testezt/EZTFinder5/images/hardware_overview.png

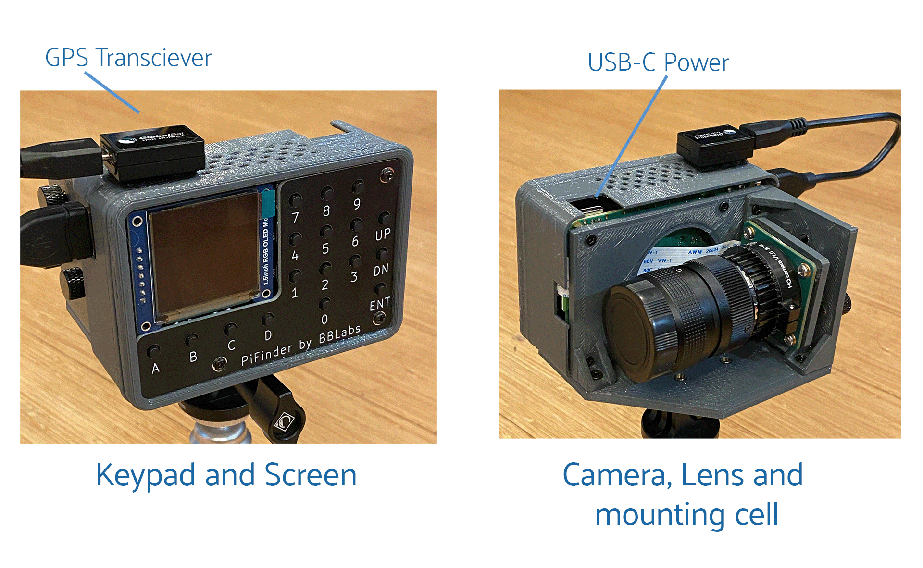
images/hardware_overview.png
