testezt/EZTFinder5/case/v3/flat/flat_plug.stl

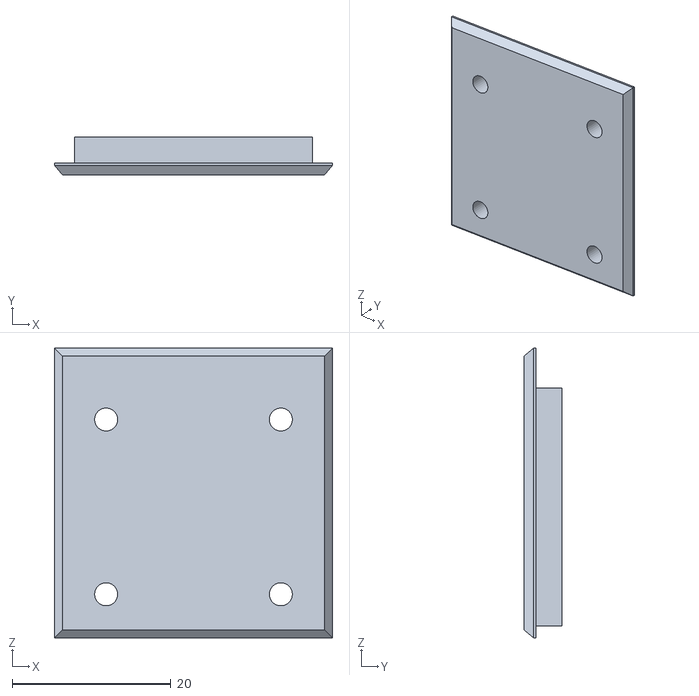
[picture p19: CAD file, 2026-02-22]
case/v3/flat/flat_plug.stl
35.0 x 4.75 x 36.5
