testezt/EZTFinder5/case/v3/left_right/camera_mount.stl

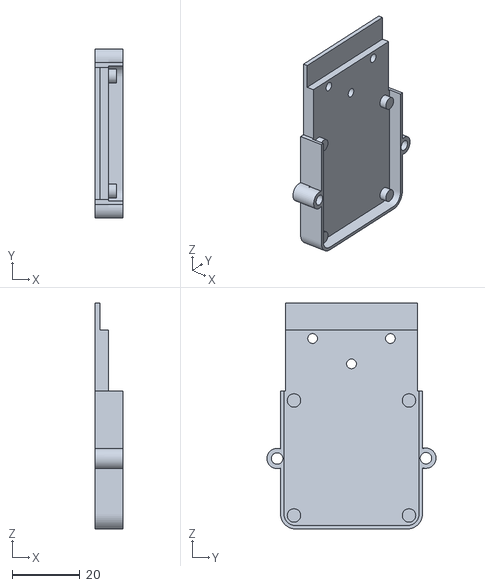
[picture p20: CAD file, 2026-02-22]
case/v3/left_right/camera_mount.stl
8.40 x 50.0 x 66.8
