testezt/EZTFinder5/case/v3/straight/st_tray.stl

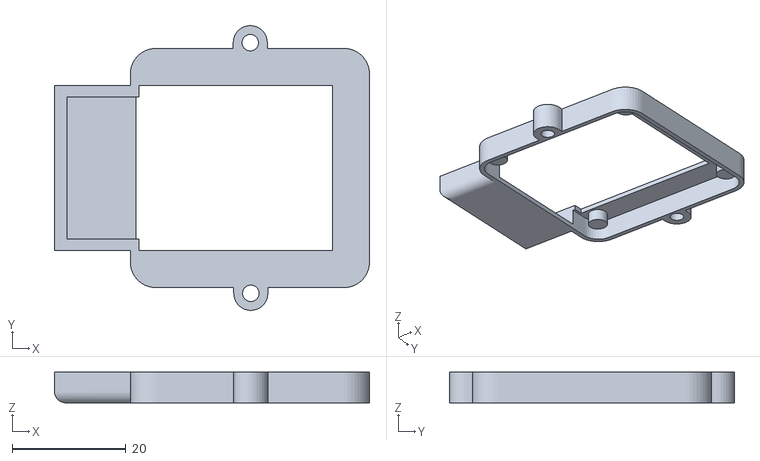
[picture p21: CAD file, 2026-02-22]
case/v3/straight/st_tray.stl
55.3 x 50.0 x 5.40
