testezt/EZTFinder5/case/accessories/tall_dovetal_bottom.stl

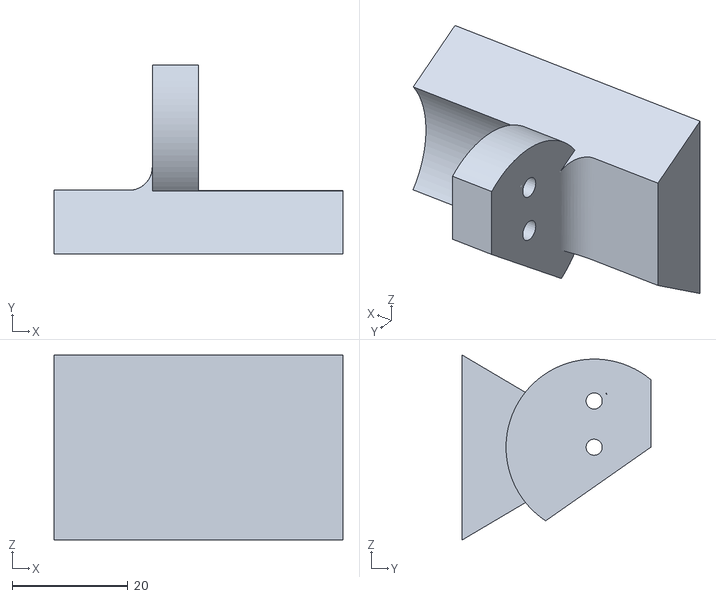
[picture p22: CAD file, 2026-02-22]
case/accessories/tall_dovetal_bottom.stl
50.0 x 32.6 x 32.0
