testezt/EZTFinder5/case/adapters/flat30_adapter_sidemount.stl

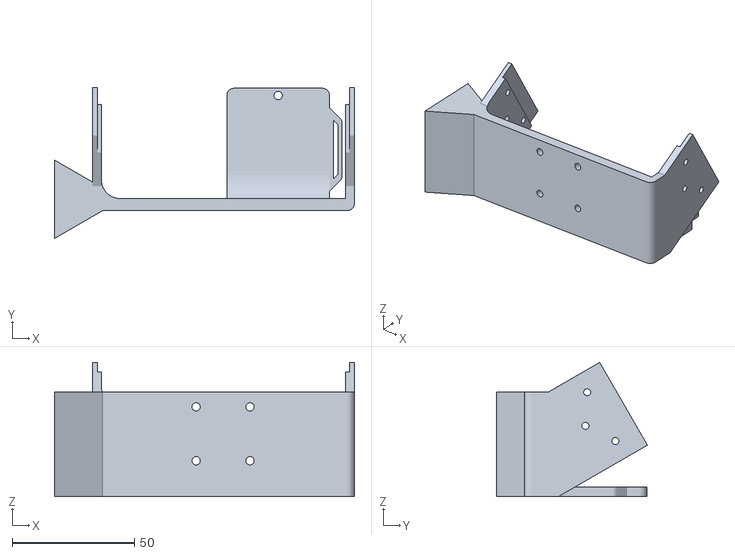
[picture p23: CAD file, 2026-02-22]
case/adapters/flat30_adapter_sidemount.stl
122.5 x 61.6 x 54.8
