testezt/EZTFinder5/case/adapters/quikfinder/PiToQuikfinder v2 - Part 2.stl

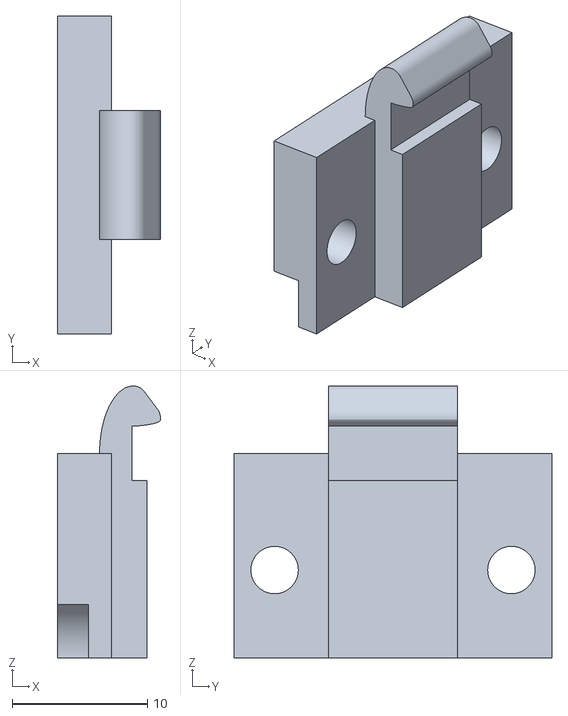
[picture p24: CAD file, 2026-02-22]
case/adapters/quikfinder/PiToQuikfinder v2 - Part 2.stl
7.60 x 23.5 x 20.1
