testezt/EZTFinder5/case/v3/common/shroud_front.stl

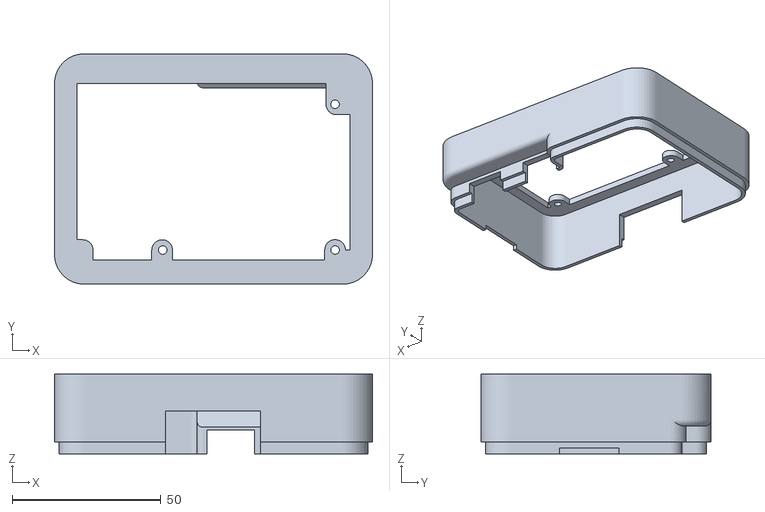
[picture p25: CAD file, 2026-02-22]
case/v3/common/shroud_front.stl
107.0 x 77.5 x 26.9
