testezt/EZTFinder5/case/v3/flat/flat30_adapter.stl

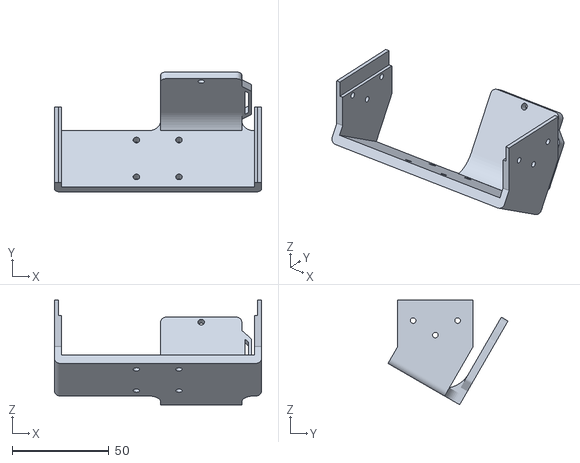
[picture p26: CAD file, 2026-02-22]
case/v3/flat/flat30_adapter.stl
107.0 x 62.1 x 54.0
