testezt/EZTFinder5/case/accessories/tube_shoe_mount_38mm_bottom.stl

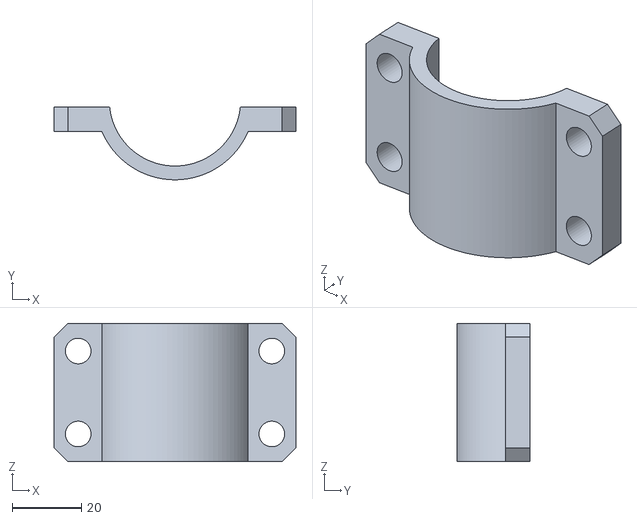
[picture p27: CAD file, 2026-02-22]
case/accessories/tube_shoe_mount_38mm_bottom.stl
70.0 x 21.0 x 40.0
