testezt/EZTFinder5/case/adapters/dovetail_losmandy.stl

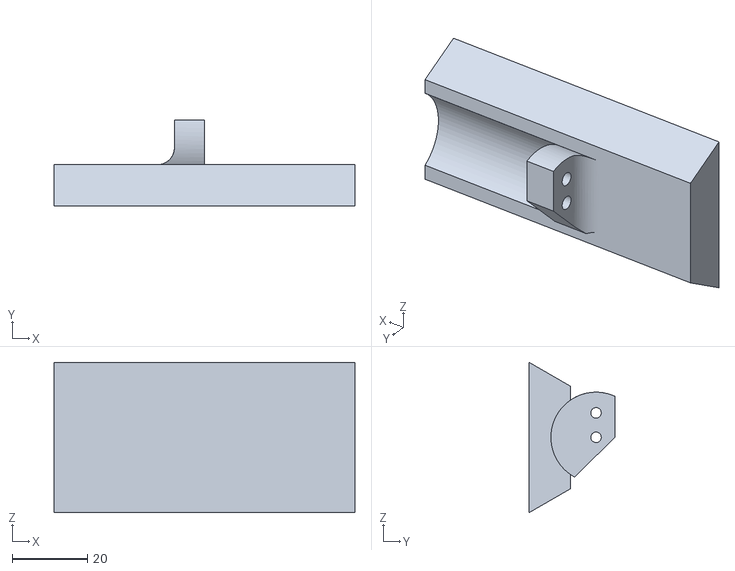
[picture p28: CAD file, 2026-02-22]
case/adapters/dovetail_losmandy.stl
80.0 x 22.9 x 40.0
