testezt/EZTFinder5/case/v3/common/pi_sugar_spacer.stl

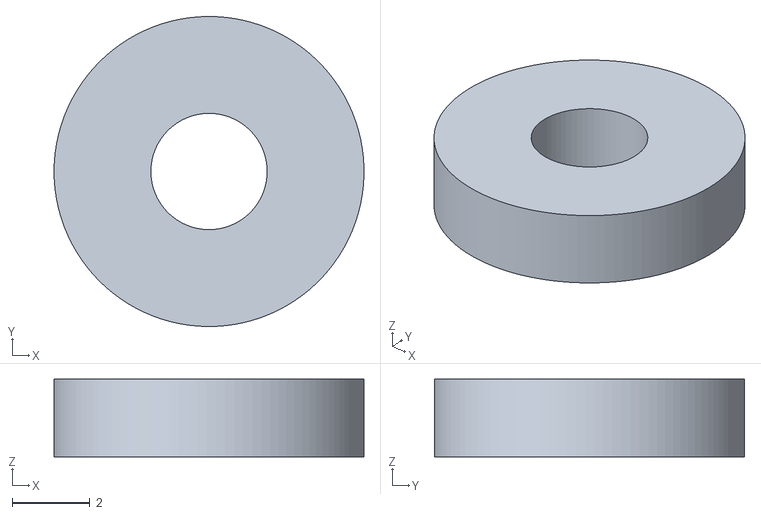
[picture p29: CAD file, 2026-02-22]
case/v3/common/pi_sugar_spacer.stl
8.00 x 8.00 x 2.00
