testezt/EZTFinder5/case/accessories/tube_shoe_mount_38mm_top.stl

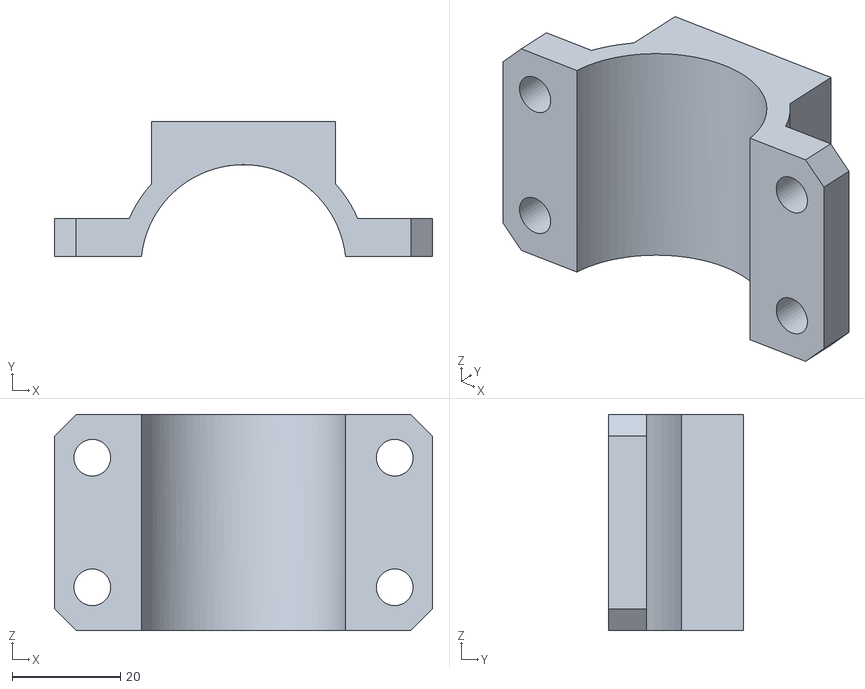
[picture p30: CAD file, 2026-02-22]
case/accessories/tube_shoe_mount_38mm_top.stl
70.0 x 25.0 x 40.0
