testezt/EZTFinder5/case/v3/common/pi_mount.stl

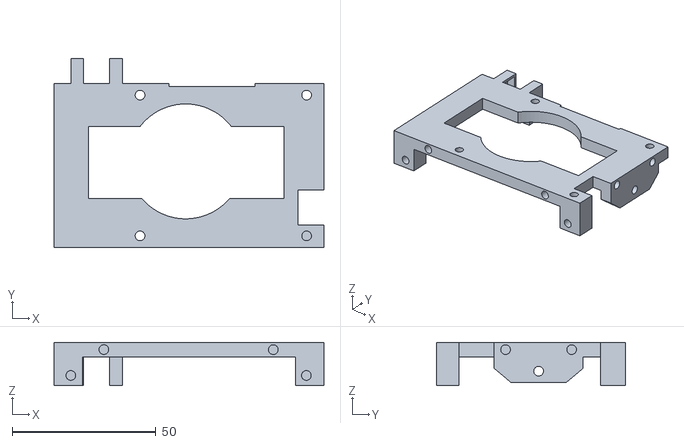
[picture p31: CAD file, 2026-02-22]
case/v3/common/pi_mount.stl
94.0 x 65.7 x 15.0
