testezt/EZTFinder5/case/accessories/tube_shoe_mount_30mm_bottom.stl

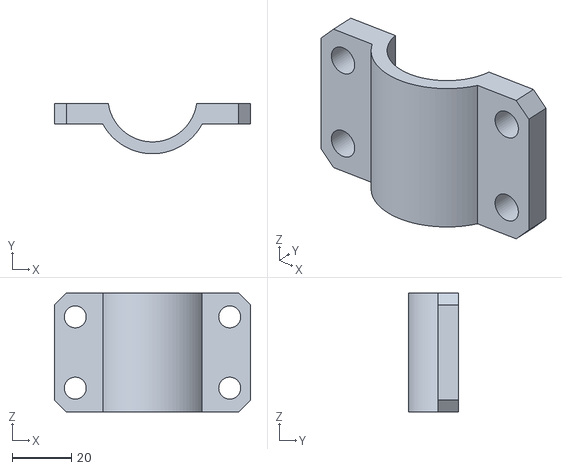
[picture p32: CAD file, 2026-02-22]
case/accessories/tube_shoe_mount_30mm_bottom.stl
66.0 x 17.0 x 40.0
