testezt/EZTFinder5/case/accessories/tube_shoe_mount_25mm_top.stl

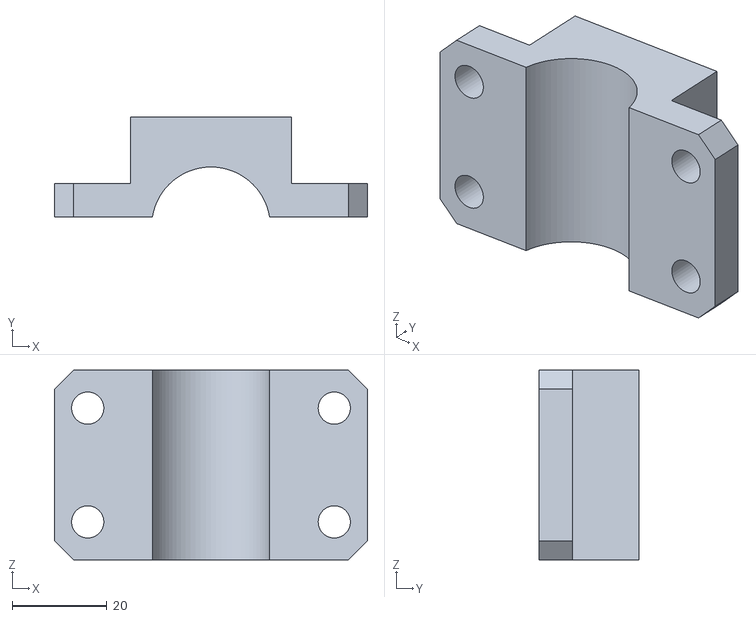
[picture p34: CAD file, 2026-02-22]
case/accessories/tube_shoe_mount_25mm_top.stl
66.0 x 21.0 x 40.0
