testezt/EZTFinder5/case/v3/common/camera_holddown_tap.stl

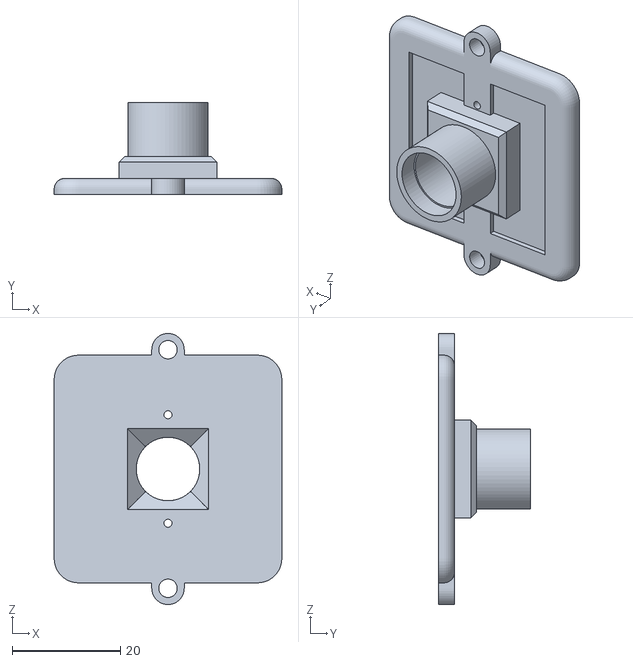
[picture p35: CAD file, 2026-02-22]
case/v3/common/camera_holddown_tap.stl
42.0 x 17.0 x 50.0
