testezt/EZTFinder5/case/accessories/tube_shoe_mount_22mm_bottom.stl

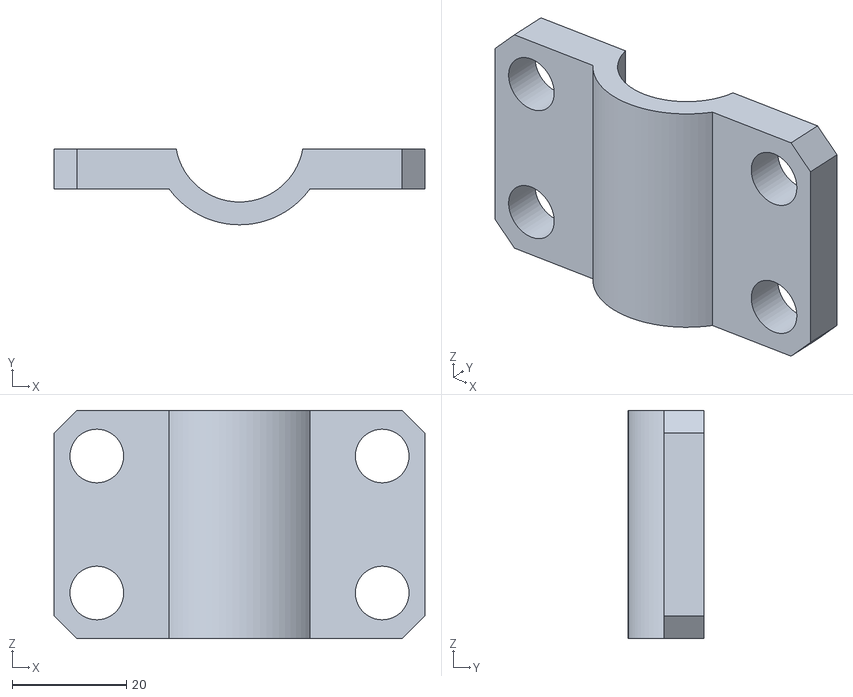
[picture p36: CAD file, 2026-02-22]
case/accessories/tube_shoe_mount_22mm_bottom.stl
65.0 x 13.2 x 40.0
