testezt/EZTFinder5/case/v3/common/shroud_back.stl

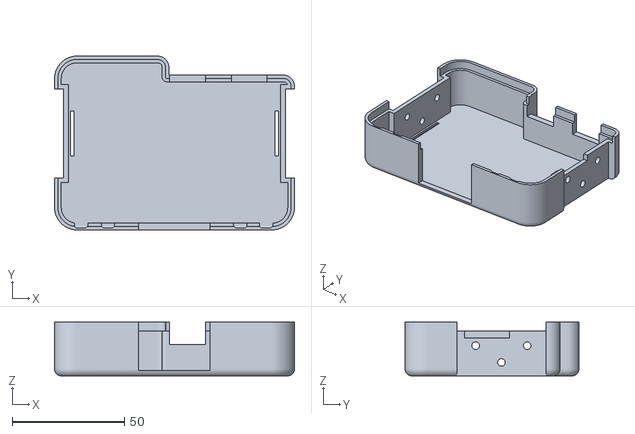
[picture p37: CAD file, 2026-02-22]
case/v3/common/shroud_back.stl
107.0 x 77.5 x 24.0
