testezt/EZTFinder5/case/v3/common/dovetail_bottom.stl

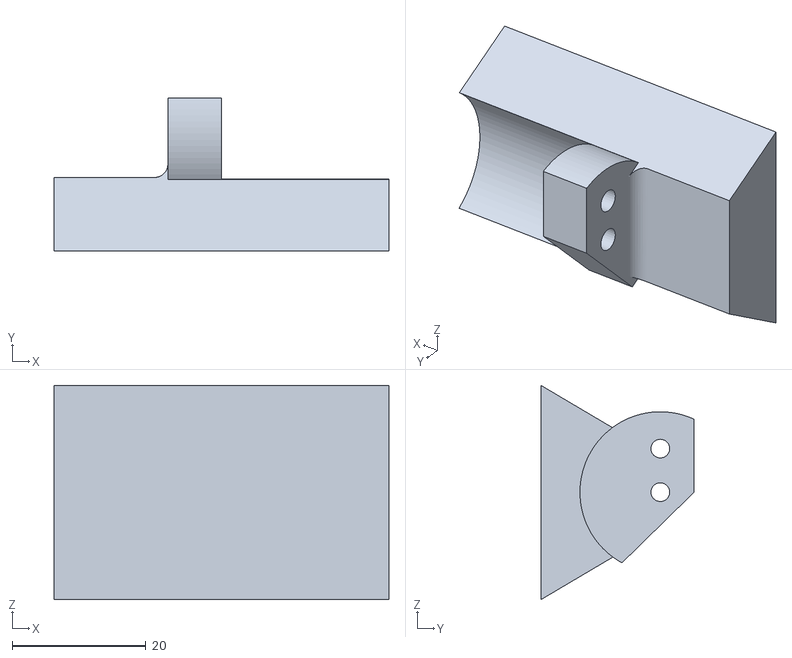
[picture p39: CAD file, 2026-02-22]
case/v3/common/dovetail_bottom.stl
50.0 x 22.9 x 32.0
