testezt/EZTFinder5/case/accessories/vixen_right_angle.stl

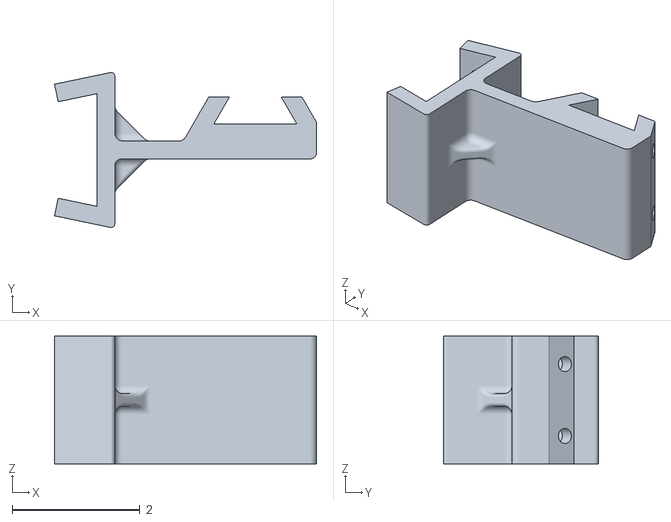
[picture p40: CAD file, 2026-02-22]
case/accessories/vixen_right_angle.stl
4.10 x 2.43 x 2.00
