testezt/EZTFinder5/case/v3/common/dovetail_top.stl

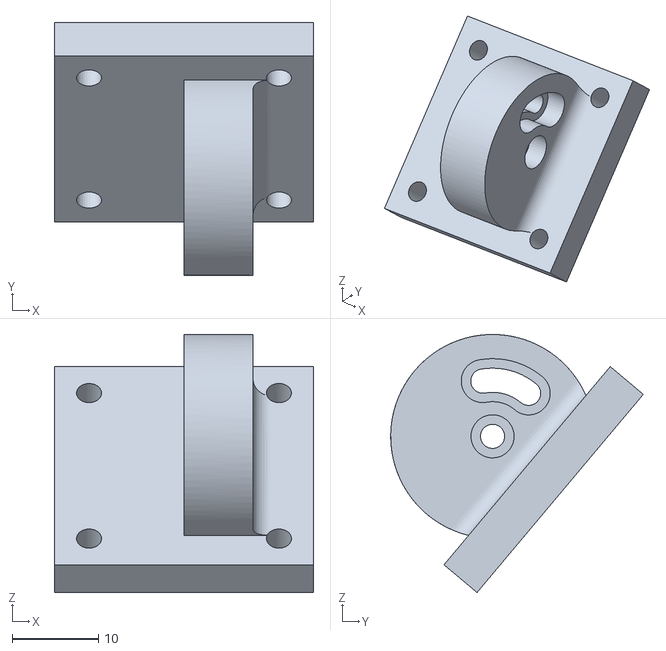
[picture p41: CAD file, 2026-02-22]
case/v3/common/dovetail_top.stl
30.0 x 29.3 x 29.9
