testezt/EZTFinder5/case/accessories/90_degree_dovetail.stl

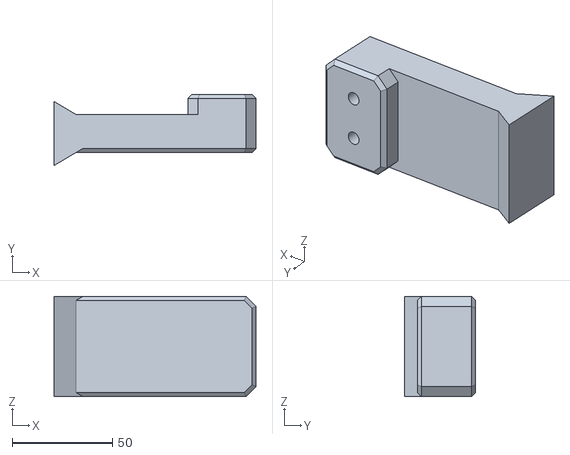
[picture p42: CAD file, 2026-02-22]
case/accessories/90_degree_dovetail.stl
100.9 x 35.5 x 50.0
