testezt/EZTFinder5/case/v3/common/bottom.stl

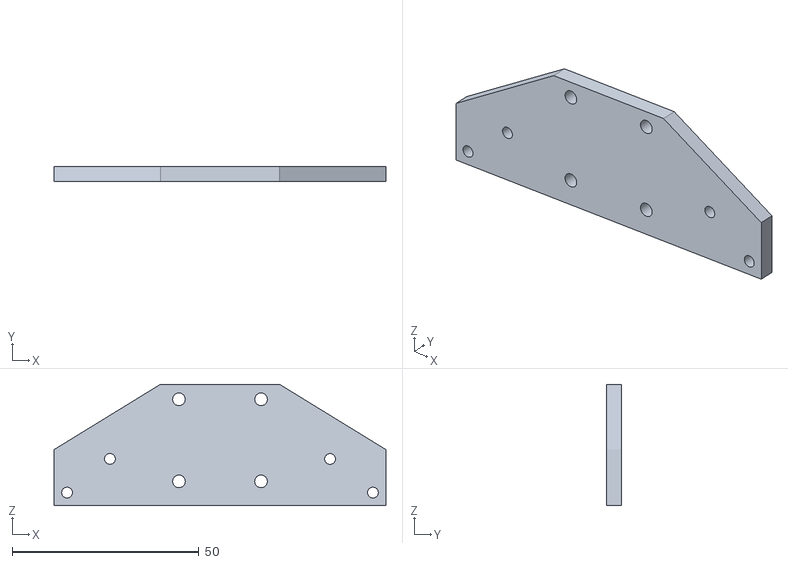
[picture p43: CAD file, 2026-02-22]
case/v3/common/bottom.stl
89.0 x 4.00 x 32.5
