testezt/EZTFinder5/case/accessories/tube_shoe_mount_32mm_bottom.stl

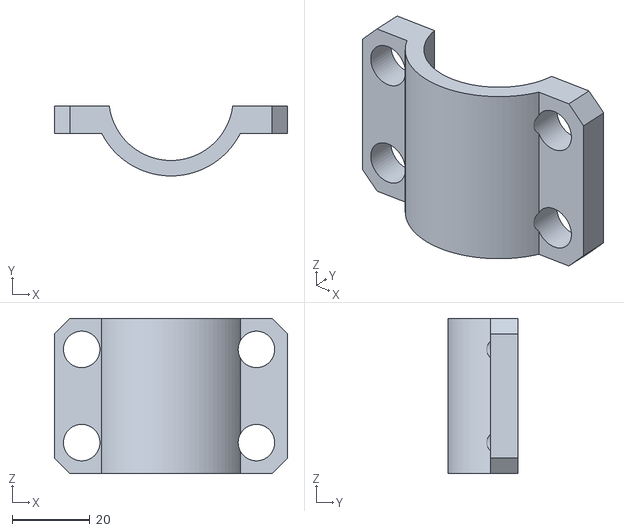
[picture p44: CAD file, 2026-02-22]
case/accessories/tube_shoe_mount_32mm_bottom.stl
60.0 x 18.0 x 40.0
