testezt/EZTFinder5/case/accessories/tube_shoe_mount_22mm_top.stl

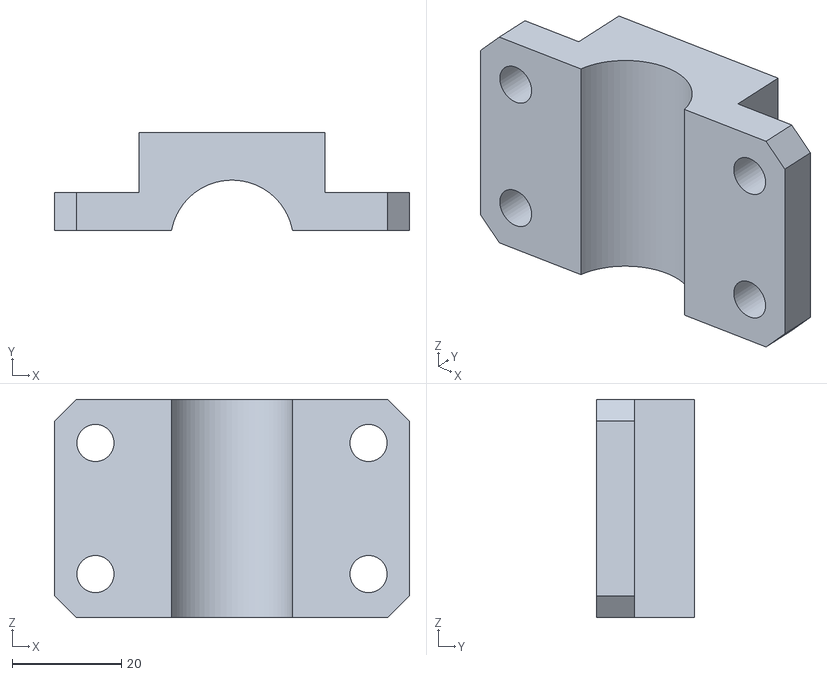
[picture p45: CAD file, 2026-02-22]
case/accessories/tube_shoe_mount_22mm_top.stl
65.0 x 18.0 x 40.0
