testezt/EZTFinder5/case/accessories/tube_shoe_mount_32mm_top.stl

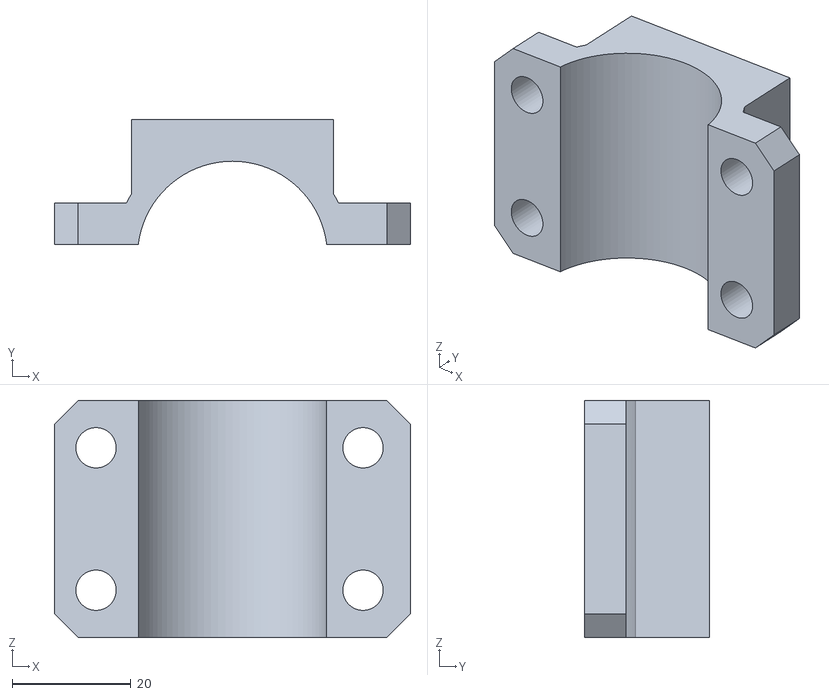
[picture p46: CAD file, 2026-02-22]
case/accessories/tube_shoe_mount_32mm_top.stl
60.0 x 21.0 x 40.0
