testezt/EZTFinder5/docs/source/images/build_guide/assembly_left_02.jpeg

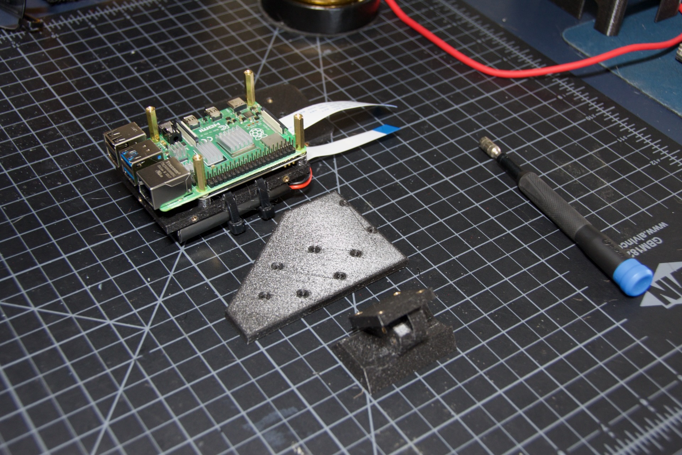
docs/source/images/build_guide/assembly_left_02.jpeg
