testezt/EZTFinder5/docs/source/images/build_guide/assembly_left_09.jpeg

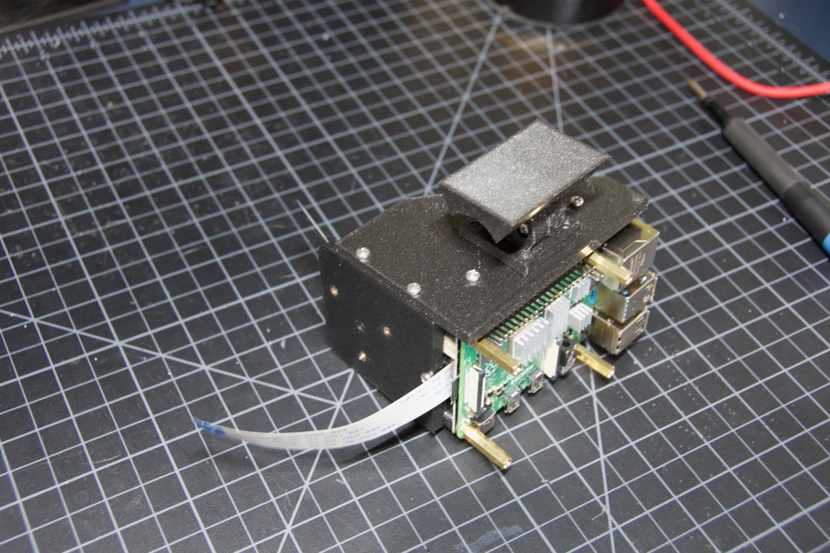
docs/source/images/build_guide/assembly_left_09.jpeg
