testezt/EZTFinder5/docs/source/images/build_guide/assembly_left_11.jpeg

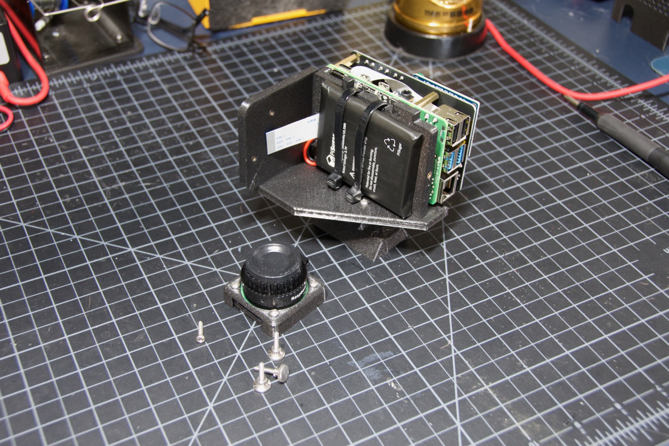
docs/source/images/build_guide/assembly_left_11.jpeg
