testezt/EZTFinder5/docs/source/images/build_guide/assembly_right_01.jpeg

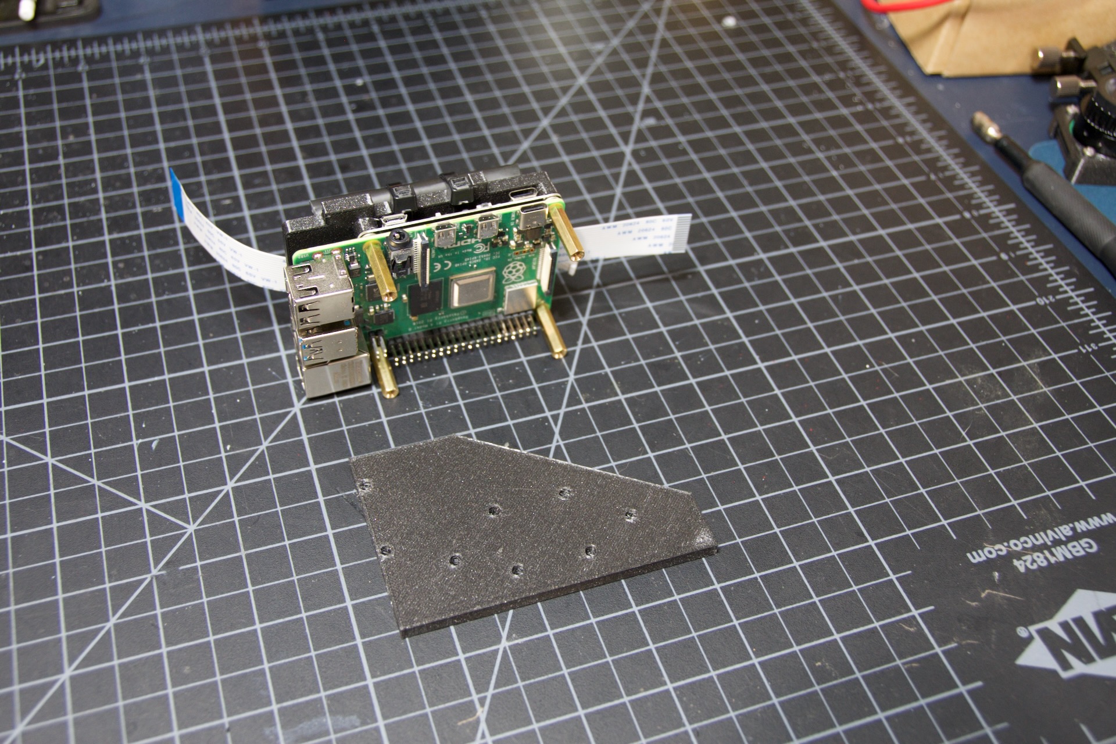
docs/source/images/build_guide/assembly_right_01.jpeg
