testezt/EZTFinder5/docs/source/images/build_guide/assembly_right_11.jpeg

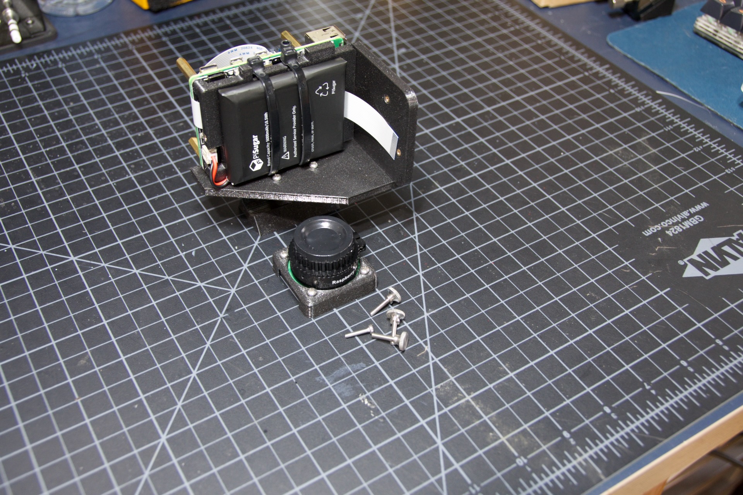
docs/source/images/build_guide/assembly_right_11.jpeg
