testezt/EZTFinder5/docs/source/images/build_guide/assembly_right_14.jpeg

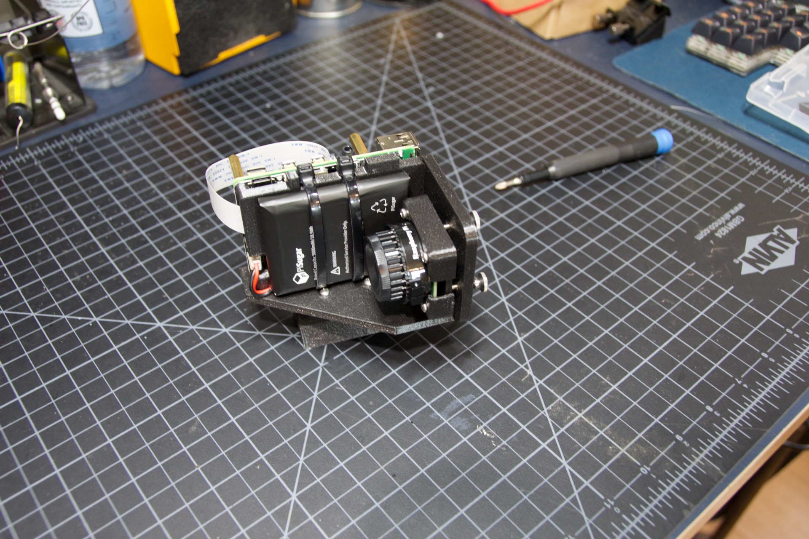
docs/source/images/build_guide/assembly_right_14.jpeg
