testezt/EZTFinder5/docs/source/images/build_guide/left_12.jpeg

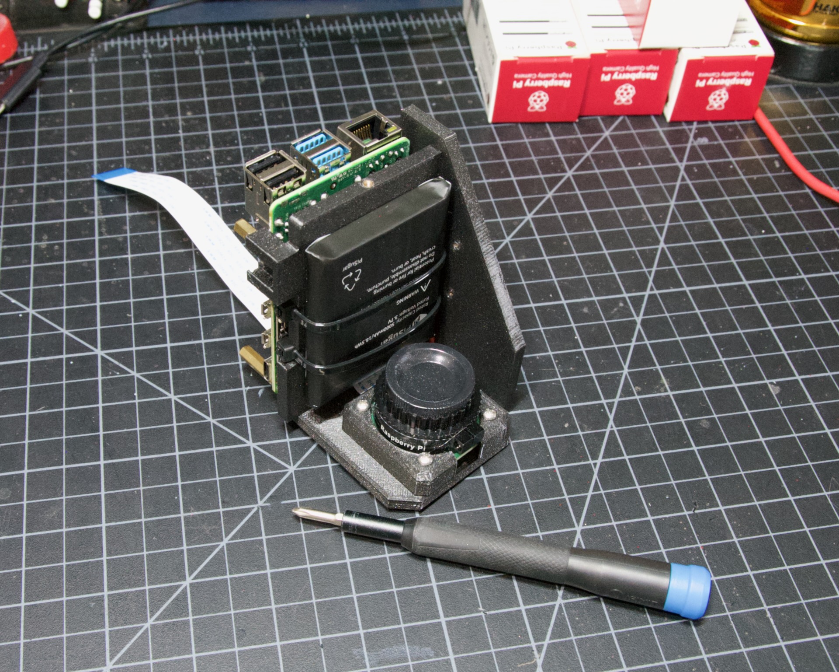
docs/source/images/build_guide/left_12.jpeg
