testezt/EZTFinder5/docs/source/images/build_guide/pisugar_stack_left02.jpeg

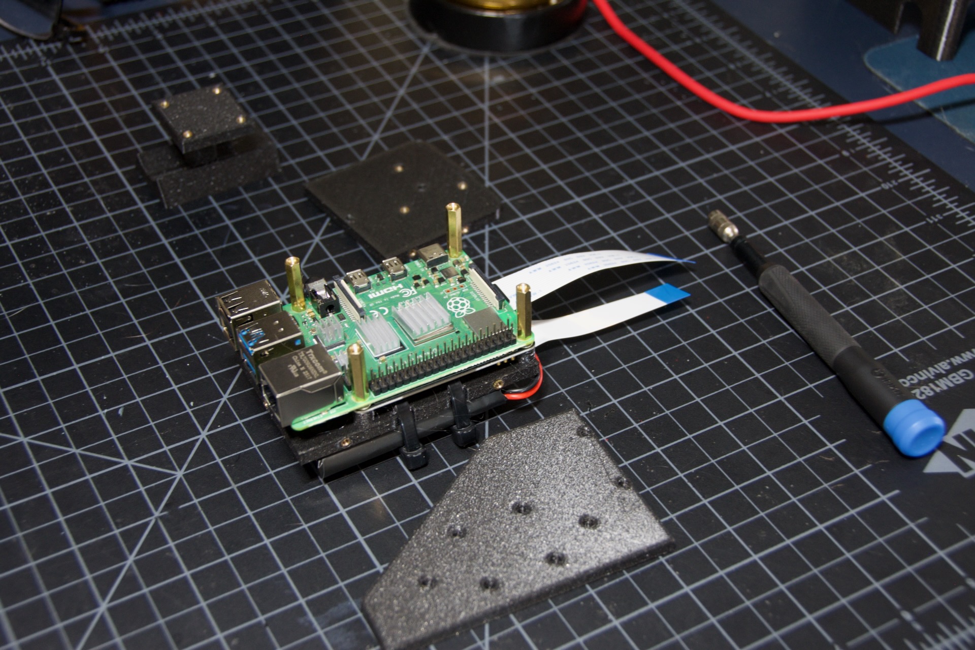
docs/source/images/build_guide/pisugar_stack_left02.jpeg
