testezt/EZTFinder5/docs/source/images/build_guide/right_10.jpeg

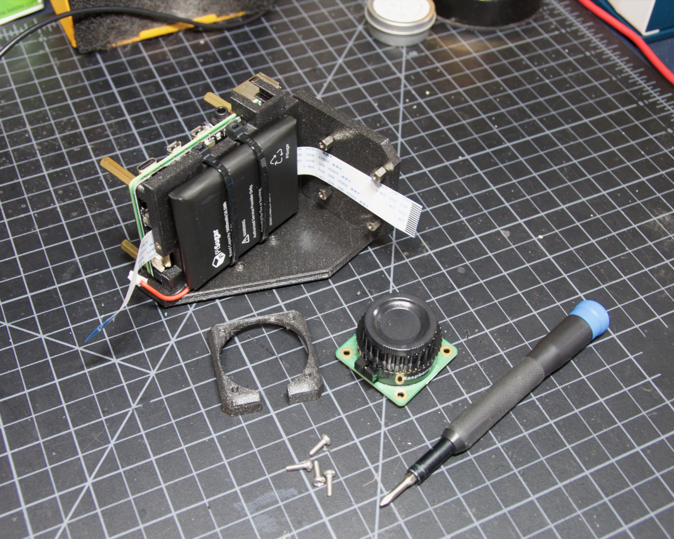
docs/source/images/build_guide/right_10.jpeg
