testezt/EZTFinder5/docs/source/images/build_guide/right_11.jpeg

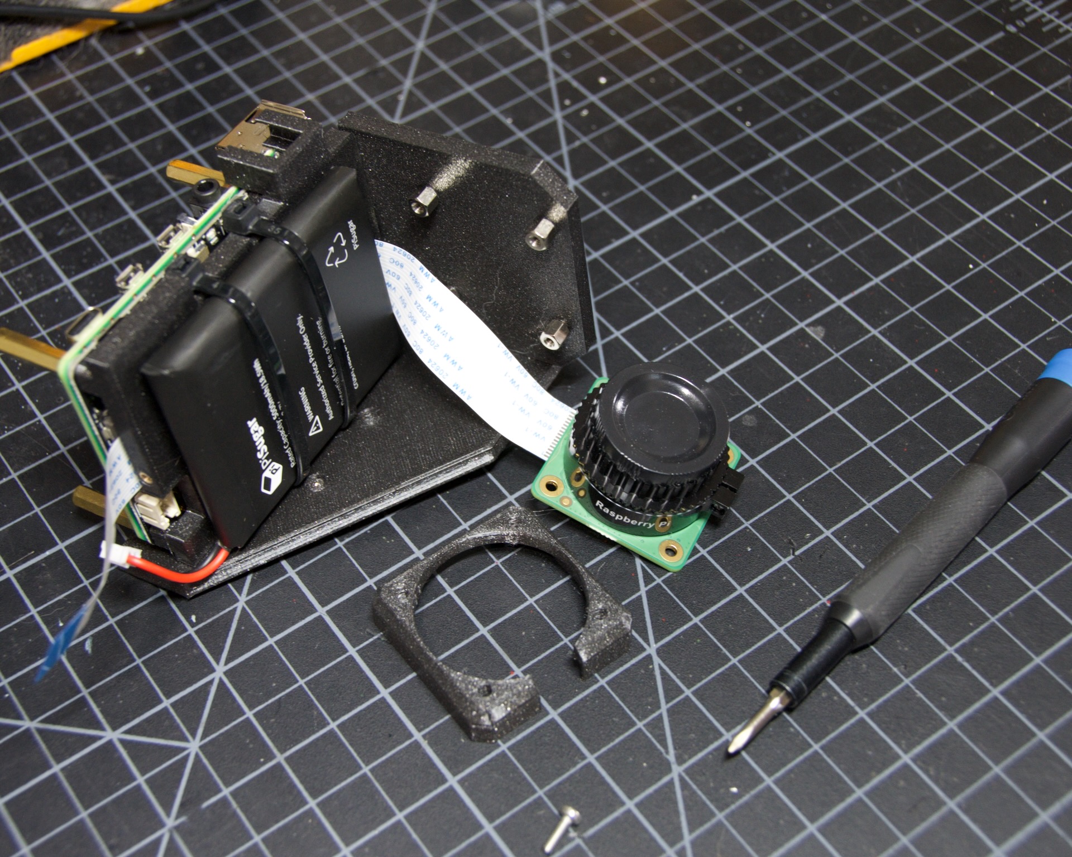
docs/source/images/build_guide/right_11.jpeg
