testezt/EZTFinder5/docs/source/images/build_guide/right_15.jpeg

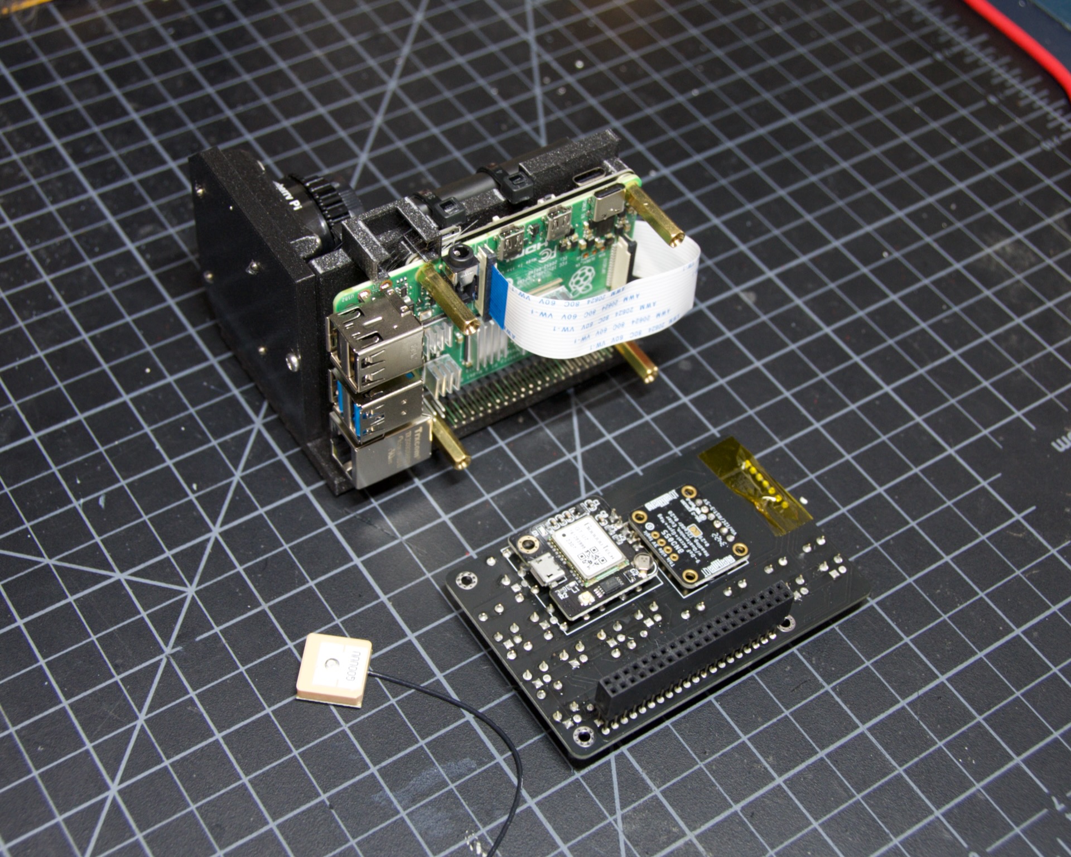
docs/source/images/build_guide/right_15.jpeg
