testezt/EZTFinder5/docs/source/images/build_guide/right_19.jpeg

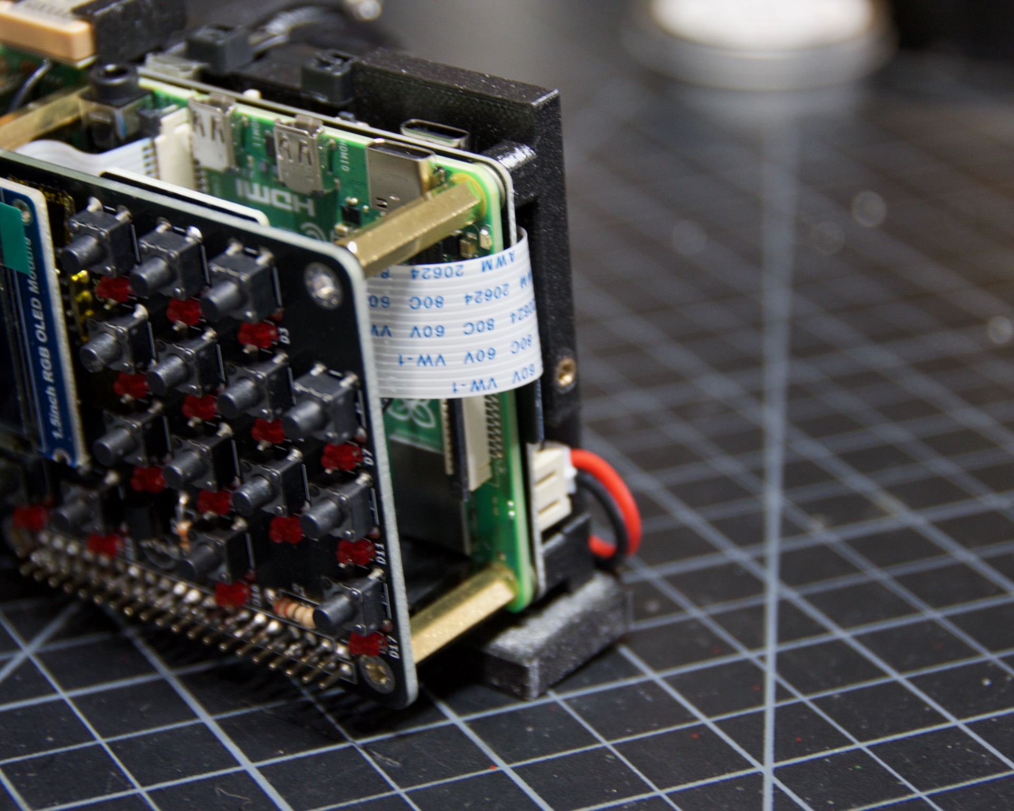
docs/source/images/build_guide/right_19.jpeg
