testezt/EZTFinder5/docs/source/images/user_guide/camera_help_02.png

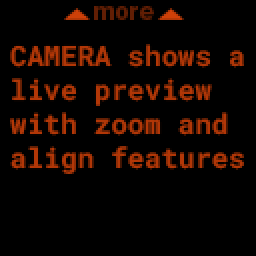
docs/source/images/user_guide/camera_help_02.png
