testezt/EZTFinder5/docs/source/images/user_guide/DEMO_MODE_001_docs.png

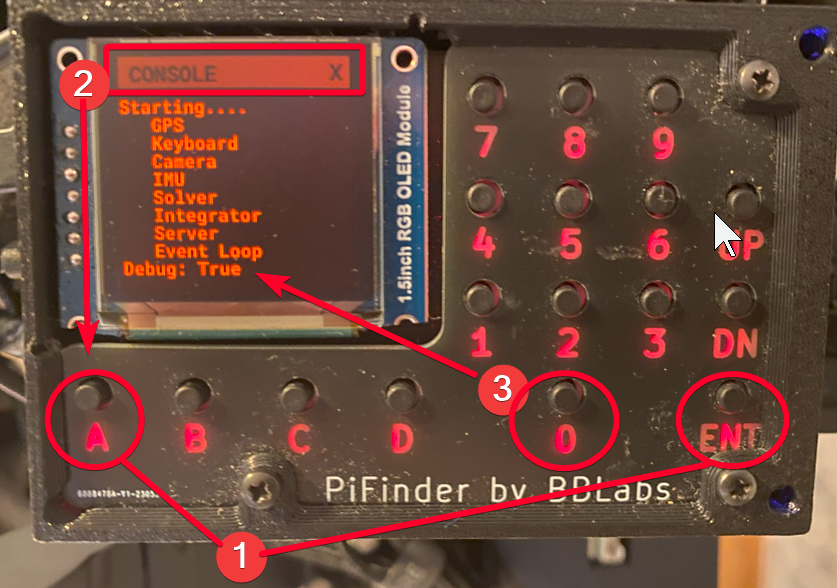
docs/source/images/user_guide/DEMO_MODE_001_docs.png
