testezt/EZTFinder5/docs/source/images/user_guide/filter_catalogs_dso.png

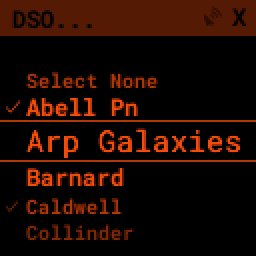
docs/source/images/user_guide/filter_catalogs_dso.png
