testezt/EZTFinder5/docs/source/images/user_guide/IMU_001_docs.png

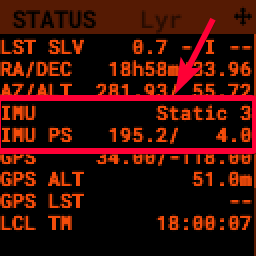
docs/source/images/user_guide/IMU_001_docs.png
