testezt/EZTFinder5/docs/source/images/user_guide/logging_01_docs.png

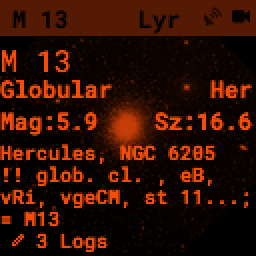
docs/source/images/user_guide/logging_01_docs.png
