testezt/EZTFinder5/docs/source/images/user_guide/logging_02_docs.png

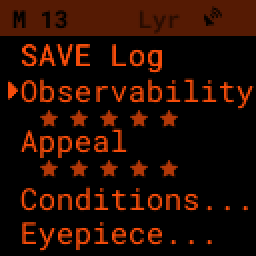
docs/source/images/user_guide/logging_02_docs.png
