testezt/EZTFinder5/docs/source/images/user_guide/main_filter_option.png

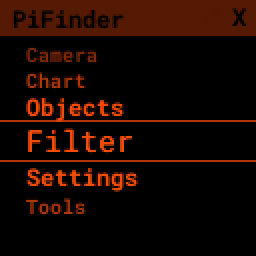
docs/source/images/user_guide/main_filter_option.png
