testezt/EZTFinder5/docs/source/images/user_guide/name_search_02.png

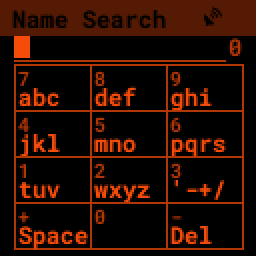
docs/source/images/user_guide/name_search_02.png
