testezt/EZTFinder5/docs/source/images/user_guide/object_details_02.png

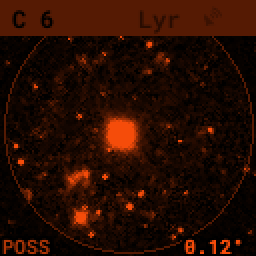
docs/source/images/user_guide/object_details_02.png
