testezt/EZTFinder5/docs/source/images/user_guide/object_details_03.png

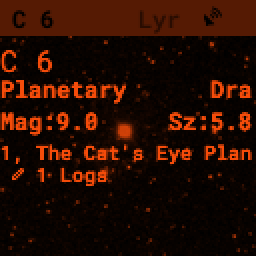
docs/source/images/user_guide/object_details_03.png
