testezt/EZTFinder5/docs/source/images/user_guide/object_list_04_docs.png

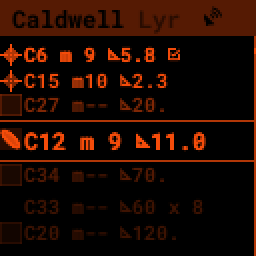
docs/source/images/user_guide/object_list_04_docs.png
