testezt/EZTFinder5/docs/source/images/user_guide/object_list_sort_docs.png

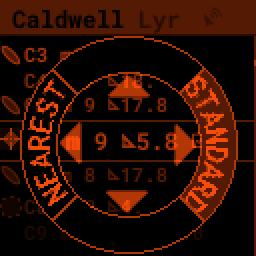
docs/source/images/user_guide/object_list_sort_docs.png
