testezt/EZTFinder5/docs/source/images/user_guide/objects_menu.png

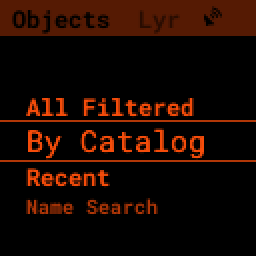
docs/source/images/user_guide/objects_menu.png
