testezt/EZTFinder5/docs/source/images/user_guide/options_menu_04.png

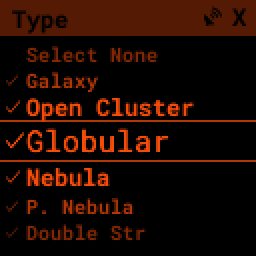
docs/source/images/user_guide/options_menu_04.png
