testezt/EZTFinder5/docs/source/images/user_guide/pf_web_home_hamburger.jpg

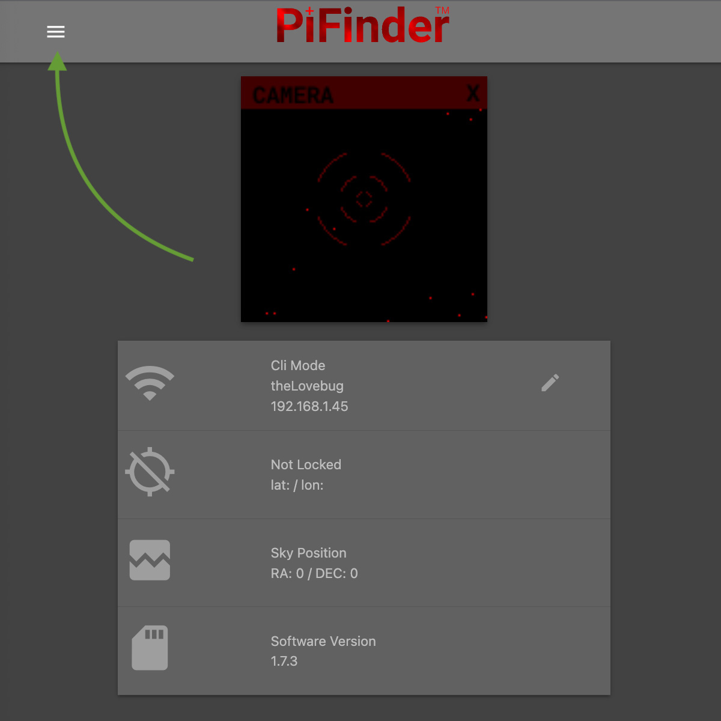
docs/source/images/user_guide/pf_web_home_hamburger.jpg
