testezt/EZTFinder5/docs/source/images/user_guide/pf_web_net0.png

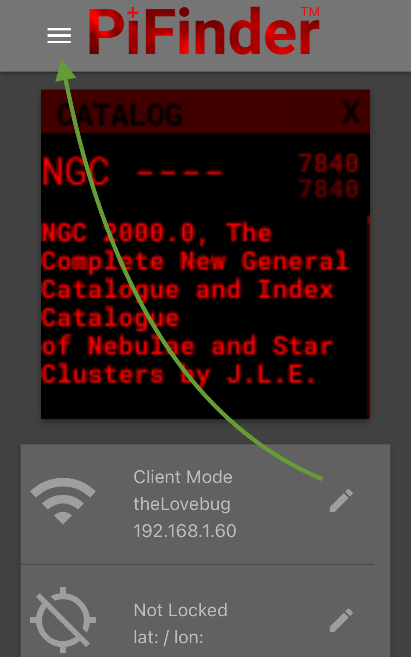
docs/source/images/user_guide/pf_web_net0.png
