testezt/EZTFinder5/docs/source/images/user_guide/pf_web_net1.jpg

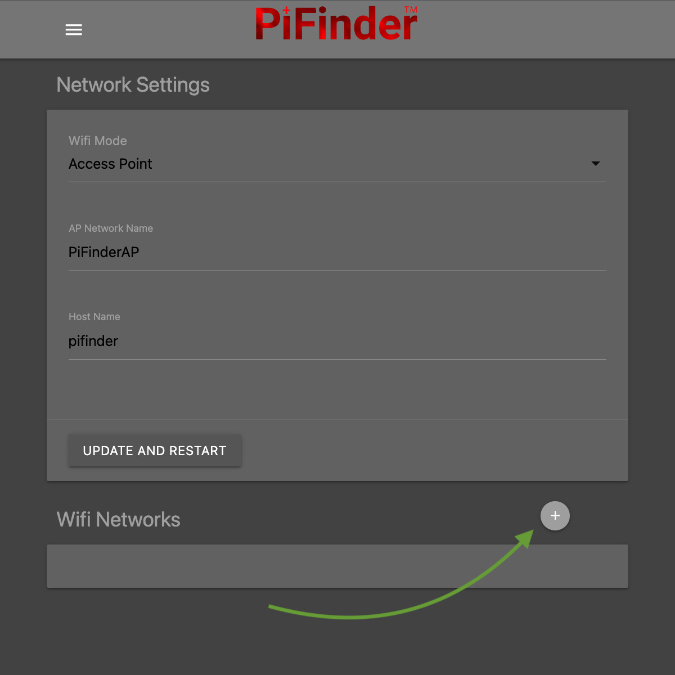
docs/source/images/user_guide/pf_web_net1.jpg
