testezt/EZTFinder5/docs/source/images/user_guide/pf_web_net2.jpg

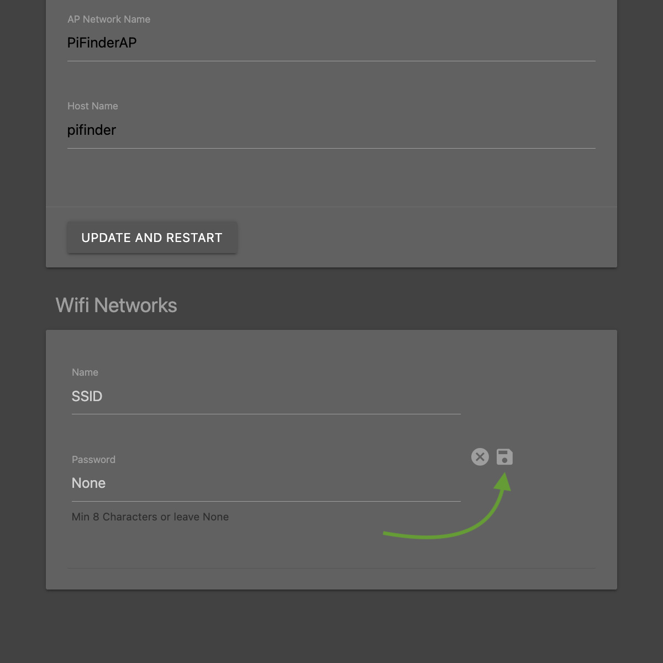
docs/source/images/user_guide/pf_web_net2.jpg
