testezt/EZTFinder5/docs/source/images/user_guide/quick_menu_00.png

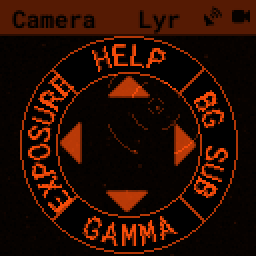
docs/source/images/user_guide/quick_menu_00.png
