testezt/EZTFinder5/docs/source/images/user_guide/settings_01.png

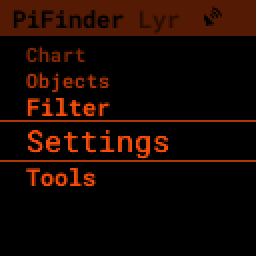
docs/source/images/user_guide/settings_01.png
