testezt/EZTFinder5/docs/source/images/user_guide/settings_02.png

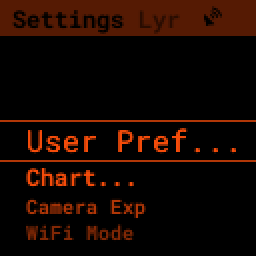
docs/source/images/user_guide/settings_02.png
