testezt/EZTFinder5/docs/source/images/user_guide/settings_03.png

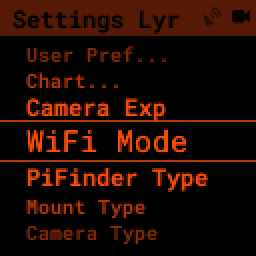
docs/source/images/user_guide/settings_03.png
