testezt/EZTFinder5/docs/source/images/user_guide/software_update_01_docs.png

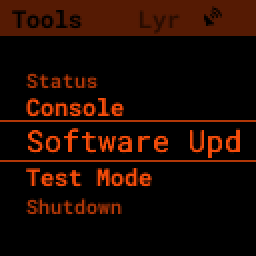
docs/source/images/user_guide/software_update_01_docs.png
