testezt/EZTFinder5/docs/source/images/user_guide/software_update_03_docs.png

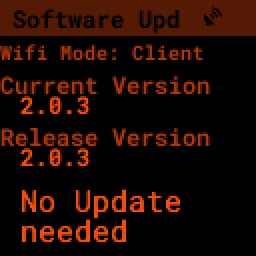
docs/source/images/user_guide/software_update_03_docs.png
