testezt/EZTFinder5/docs/source/images/user_guide/software_update_04_docs.png

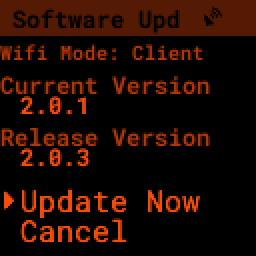
docs/source/images/user_guide/software_update_04_docs.png
