testezt/EZTFinder5/docs/source/images/user_guide/status_screen_docs.png

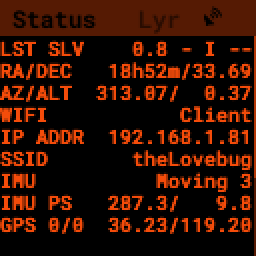
docs/source/images/user_guide/status_screen_docs.png
