testezt/EZTFinder5/images/build_guide/adjustable_dovetail/DSC_8569.jpeg

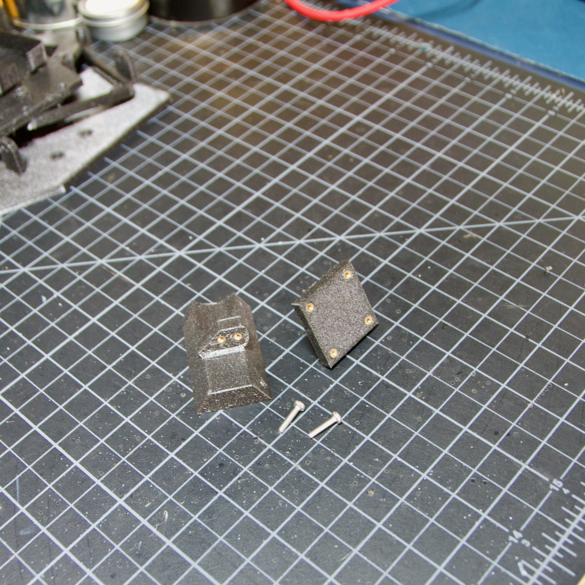
images/build_guide/adjustable_dovetail/DSC_8569.jpeg
