testezt/EZTFinder5/images/build_guide/adjustable_dovetail/DSC_8574.jpeg

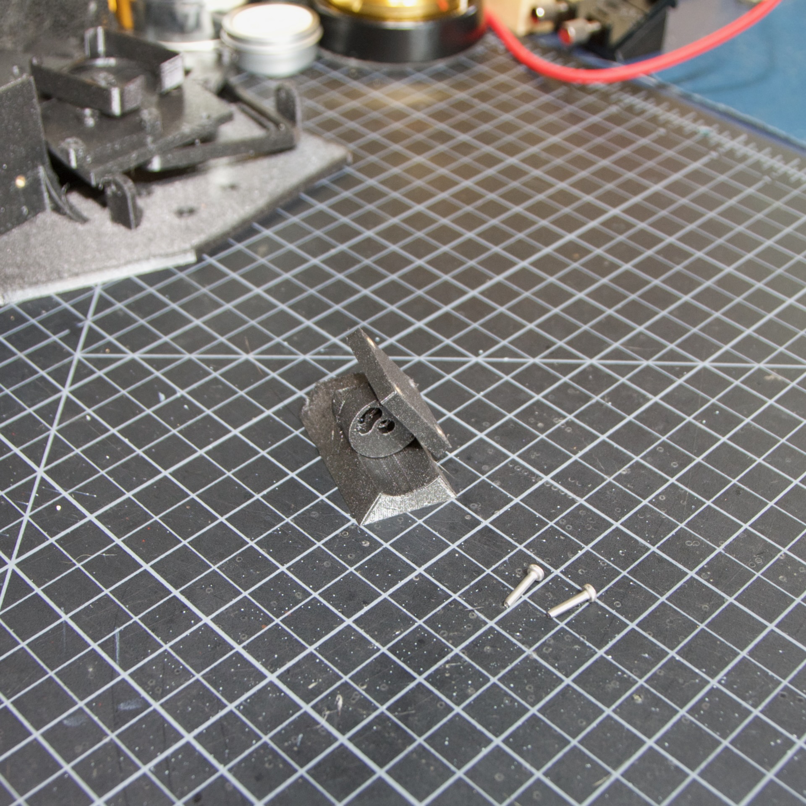
images/build_guide/adjustable_dovetail/DSC_8574.jpeg
