testezt/EZTFinder5/images/build_guide/adjustable_dovetail/DSC_8575.jpeg

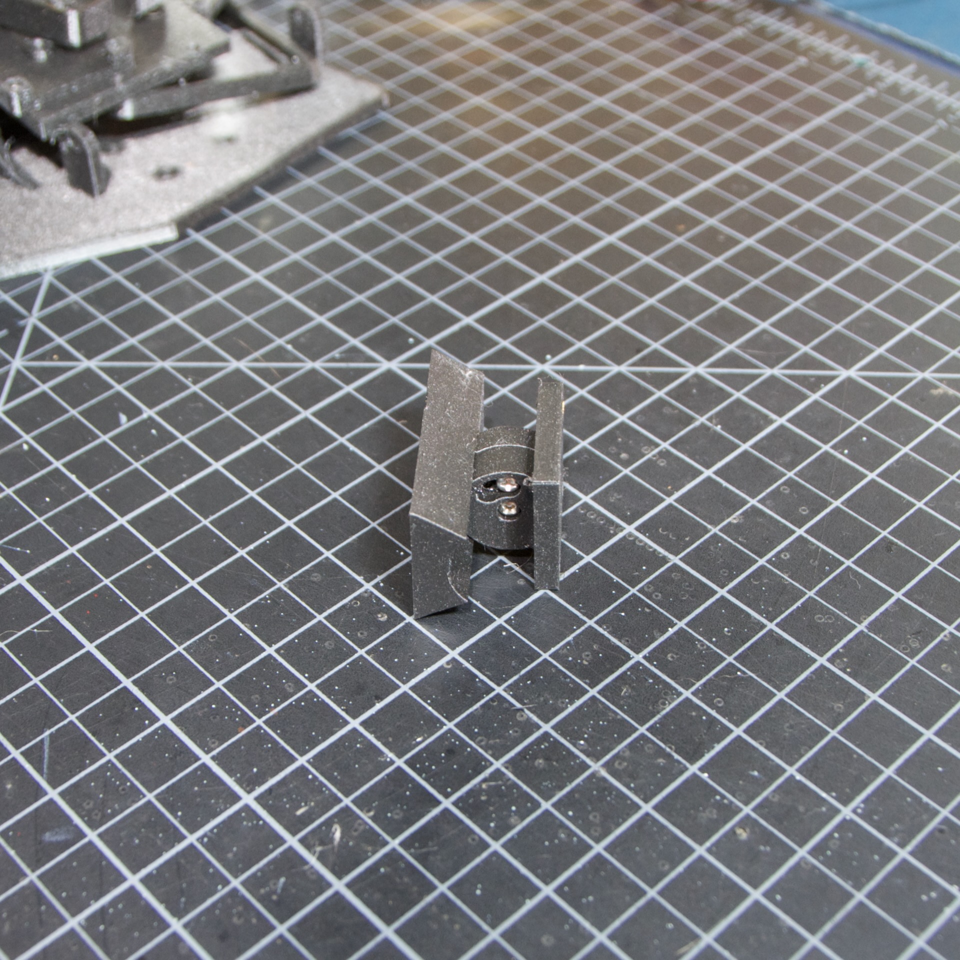
images/build_guide/adjustable_dovetail/DSC_8575.jpeg
