testezt/EZTFinder5/images/build_guide/IMG_4633.jpeg

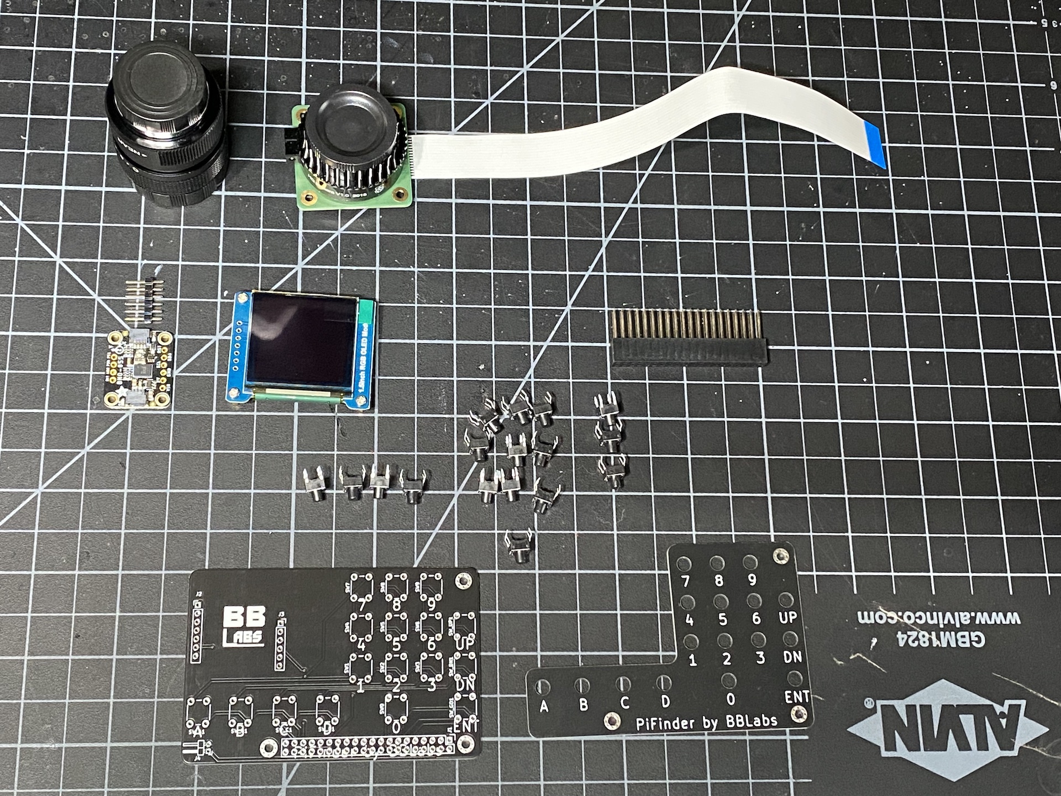
images/build_guide/IMG_4633.jpeg
