testezt/EZTFinder5/images/build_guide/IMG_4634.jpeg

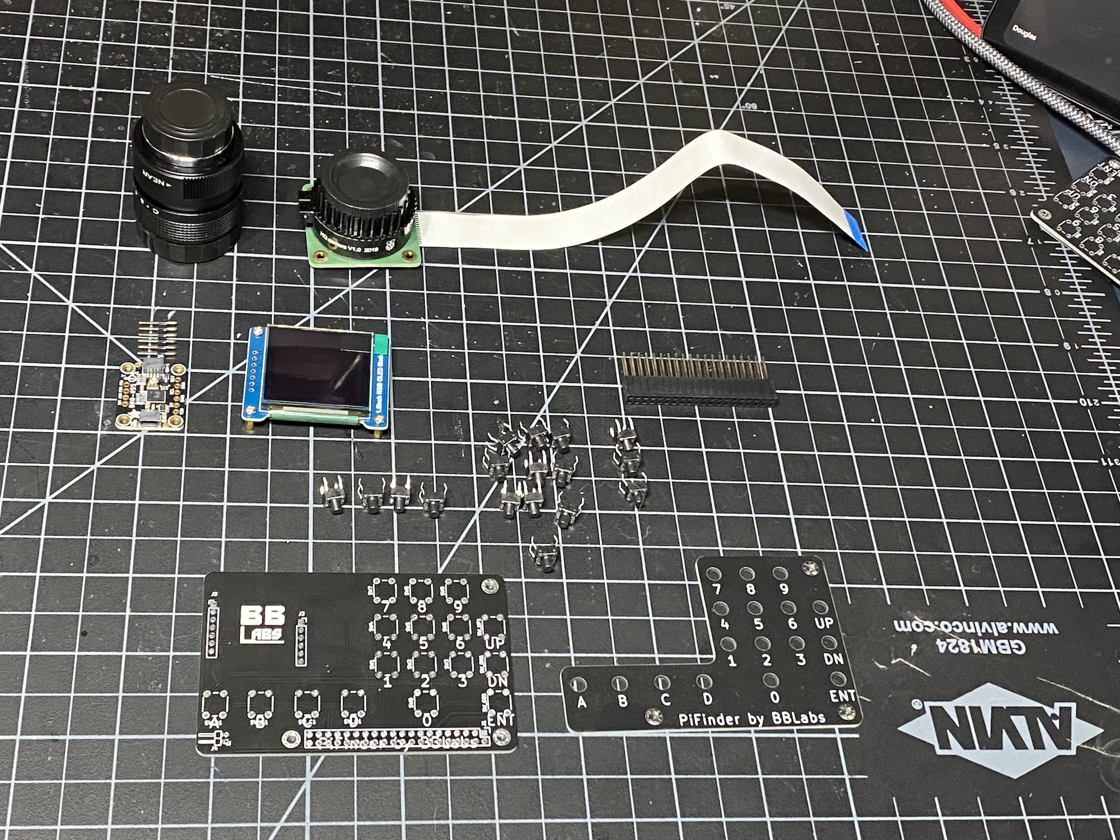
images/build_guide/IMG_4634.jpeg
