testezt/EZTFinder5/images/build_guide/IMG_4636.jpeg

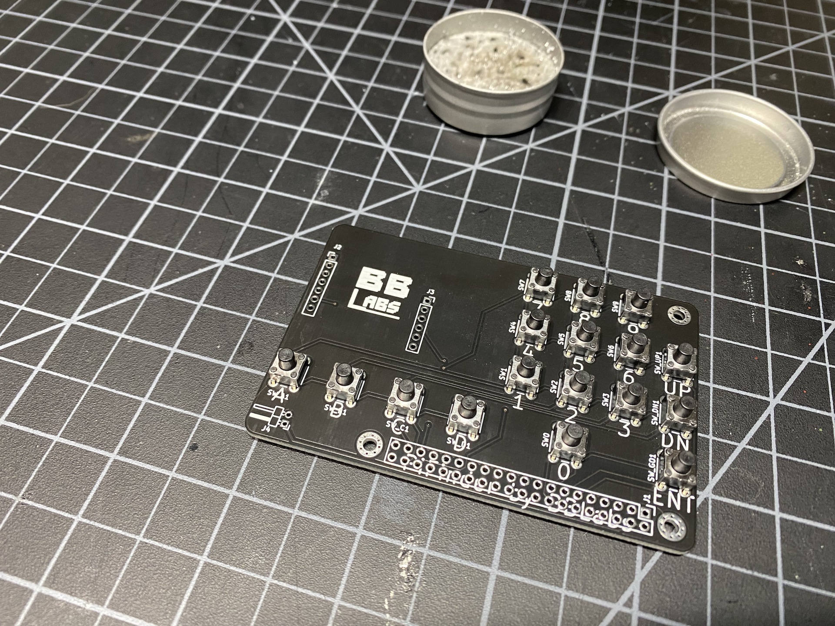
images/build_guide/IMG_4636.jpeg
