testezt/EZTFinder5/images/build_guide/IMG_4637.jpeg

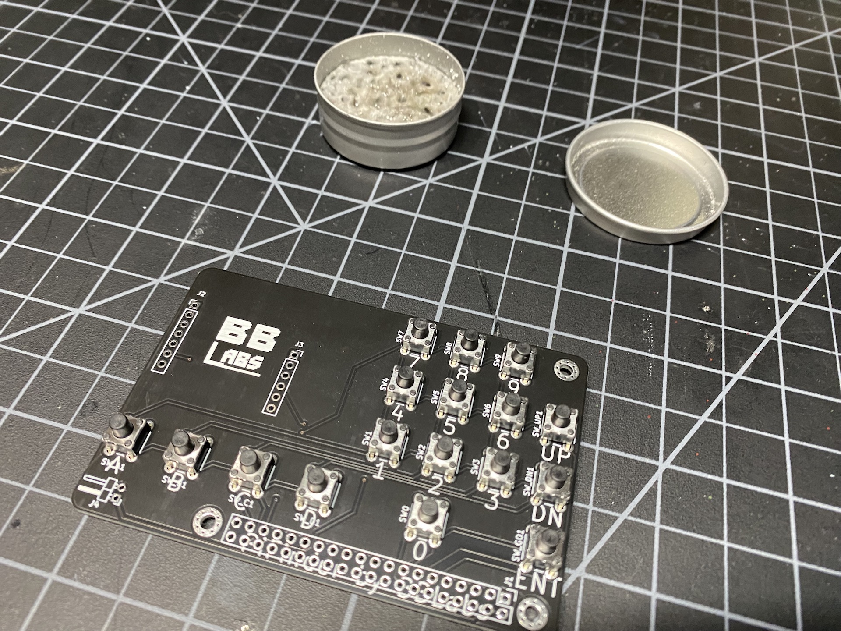
images/build_guide/IMG_4637.jpeg
