testezt/EZTFinder5/images/build_guide/IMG_4638.jpeg

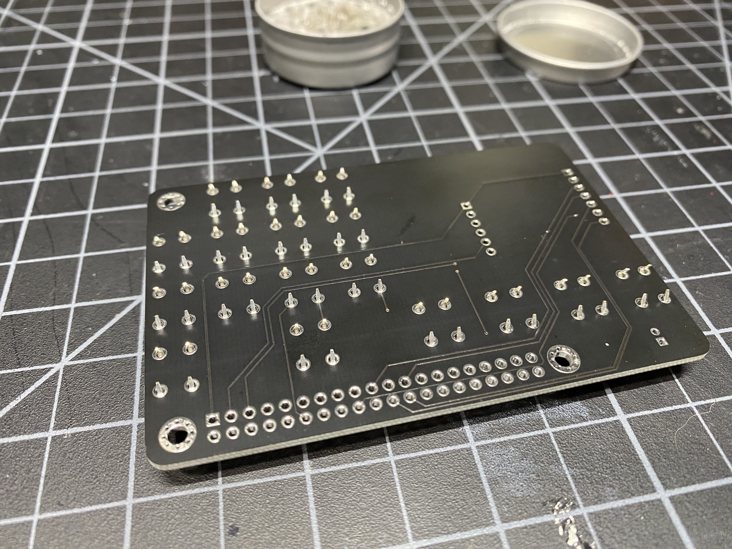
images/build_guide/IMG_4638.jpeg
