testezt/EZTFinder5/images/build_guide/IMG_4641.jpeg

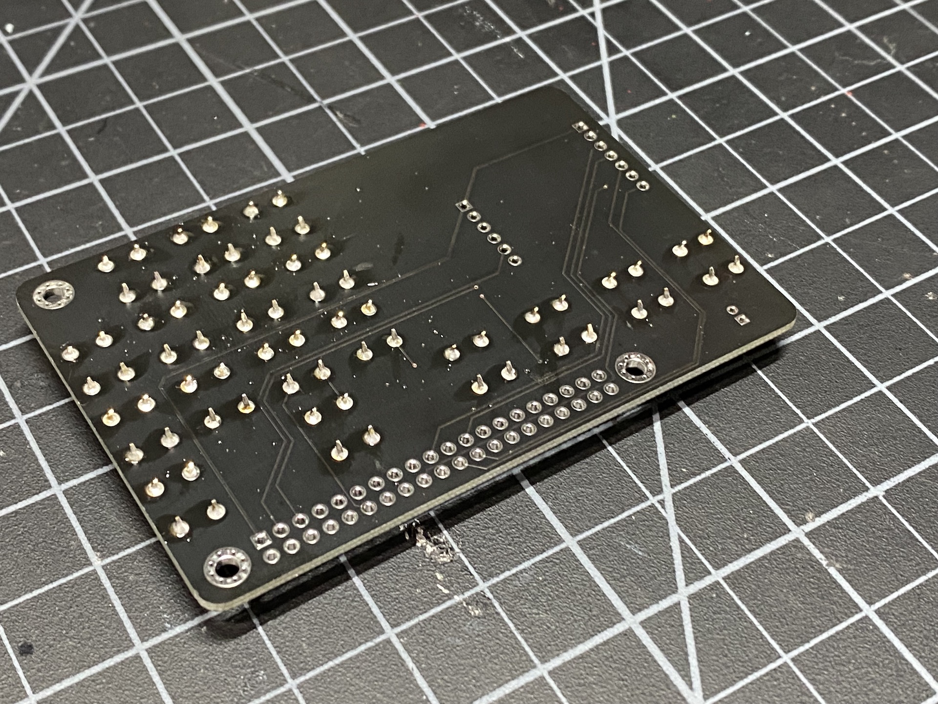
images/build_guide/IMG_4641.jpeg
