testezt/EZTFinder5/images/build_guide/IMG_4643.jpeg

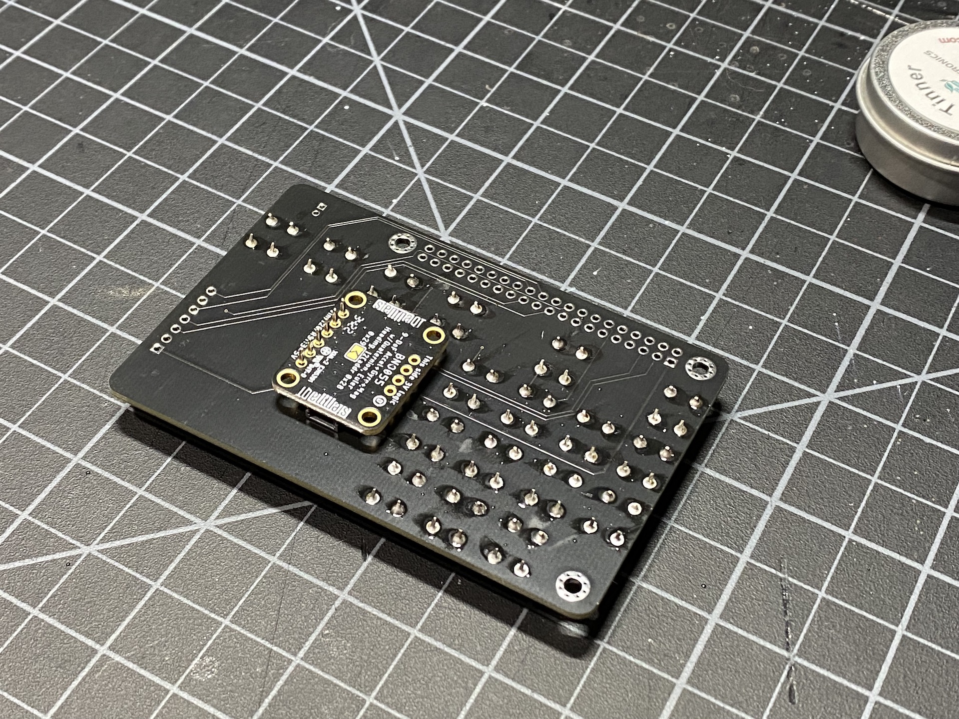
images/build_guide/IMG_4643.jpeg
