testezt/EZTFinder5/images/build_guide/IMG_4651.jpeg

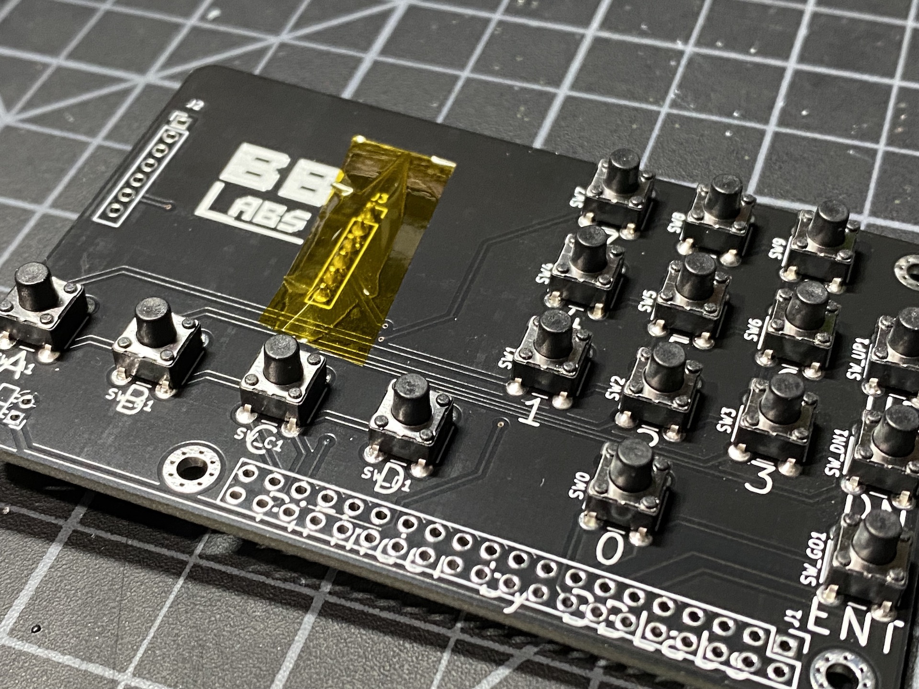
images/build_guide/IMG_4651.jpeg
