testezt/EZTFinder5/images/build_guide/IMG_4655.jpeg

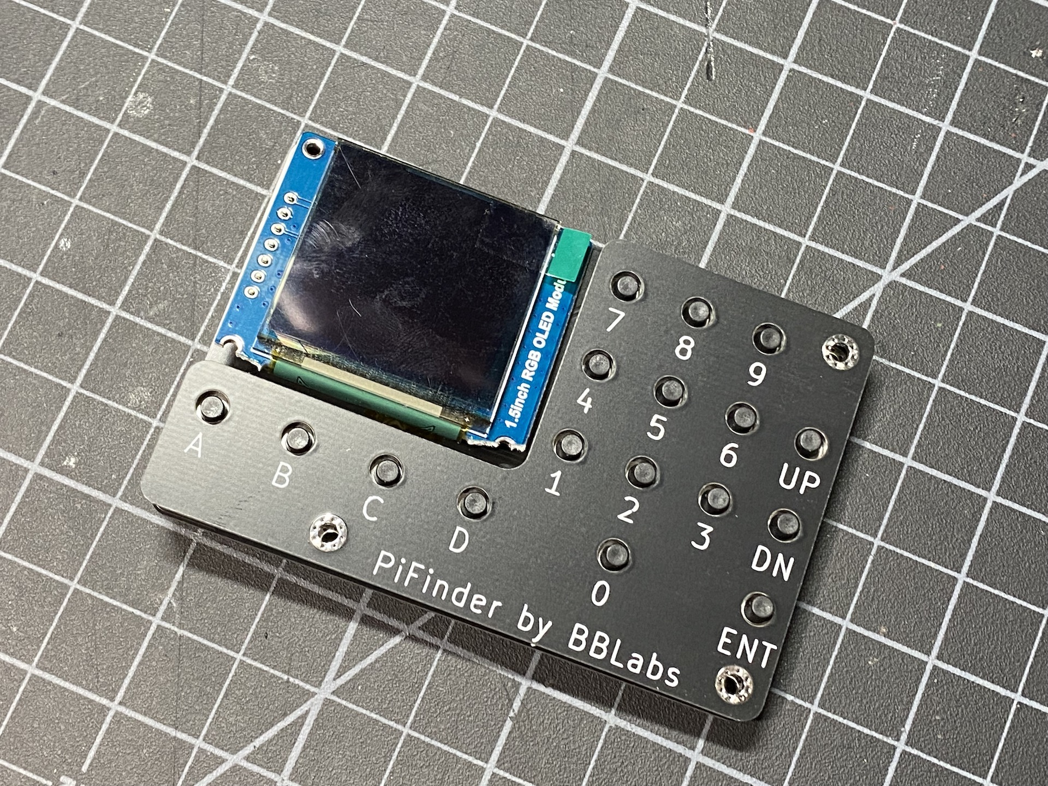
images/build_guide/IMG_4655.jpeg
