testezt/EZTFinder5/images/build_guide/IMG_4657.jpeg

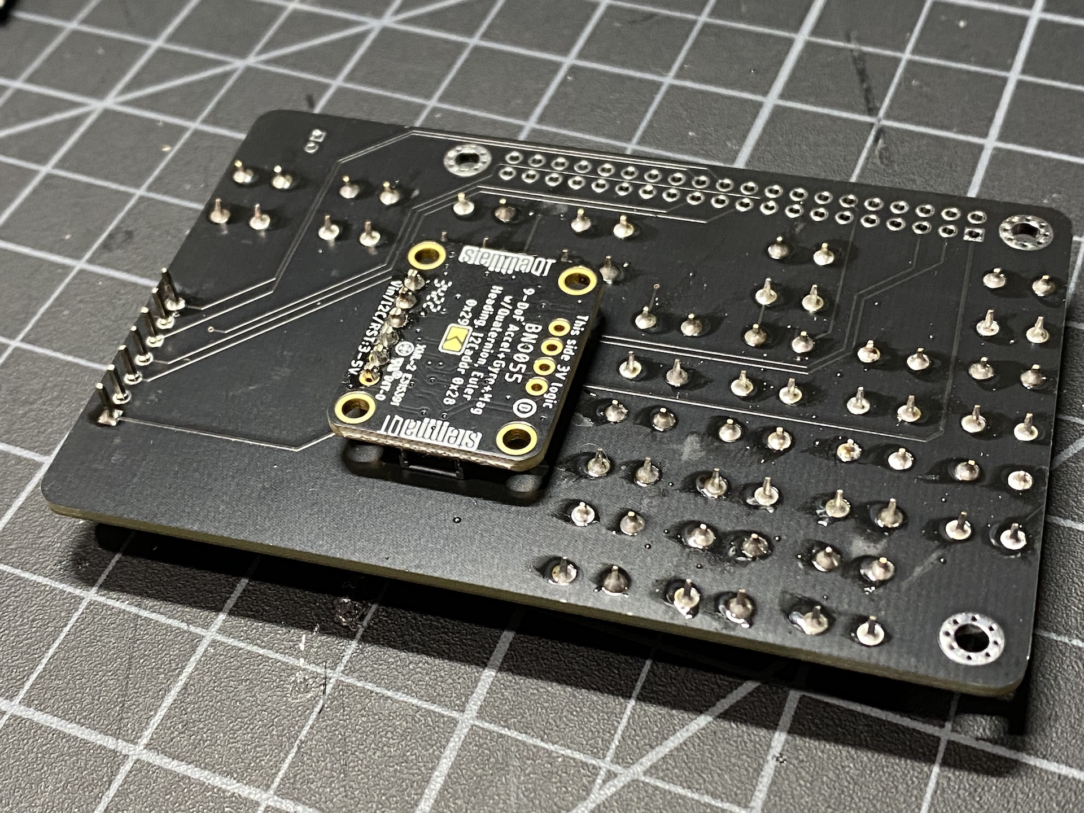
images/build_guide/IMG_4657.jpeg
