testezt/EZTFinder5/images/build_guide/IMG_4658.jpeg

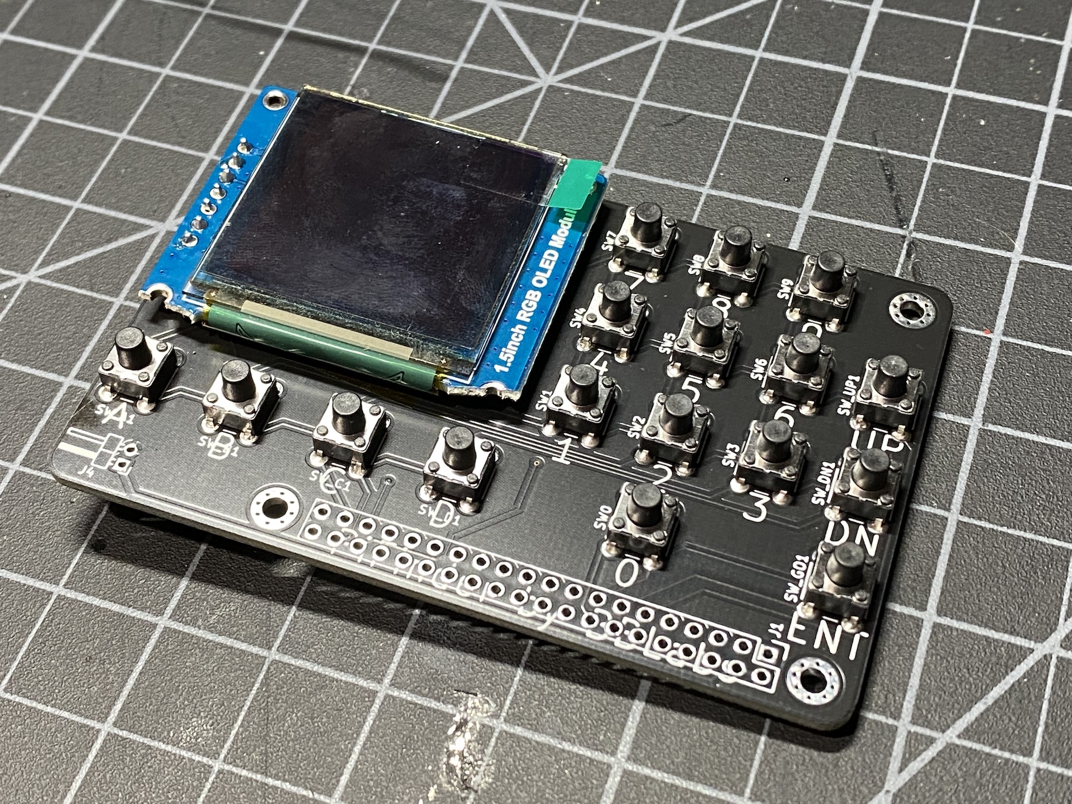
images/build_guide/IMG_4658.jpeg
