testezt/EZTFinder5/images/build_guide/IMG_4661.jpeg

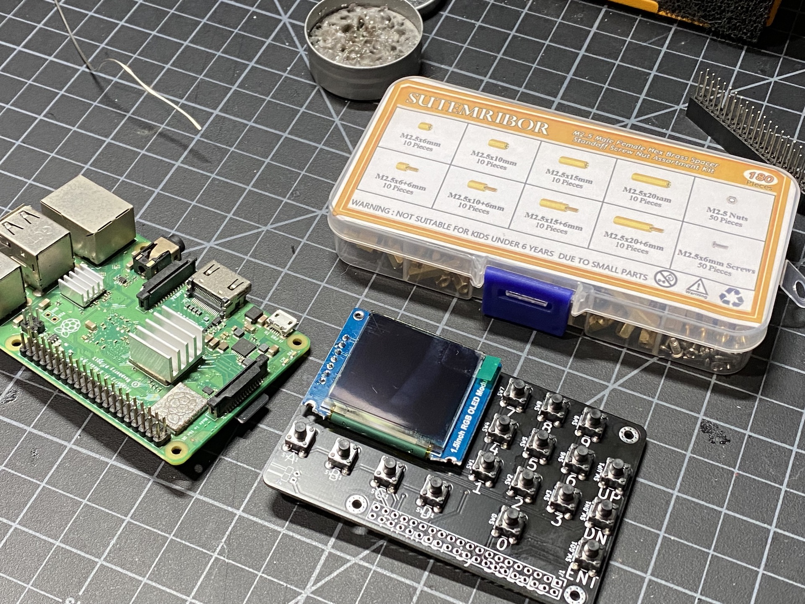
images/build_guide/IMG_4661.jpeg
