testezt/EZTFinder5/images/build_guide/IMG_4662.jpeg

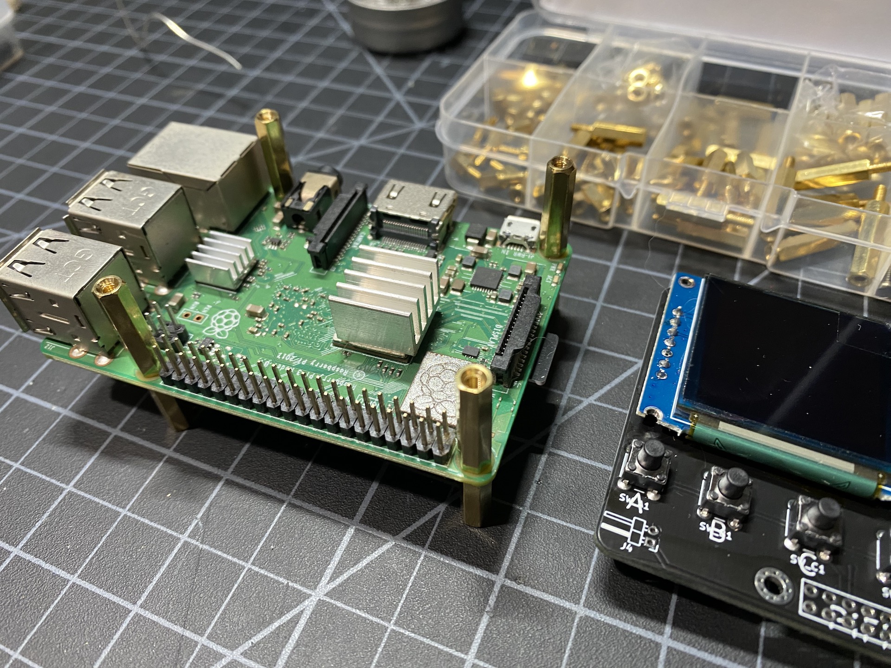
images/build_guide/IMG_4662.jpeg
