testezt/EZTFinder5/images/build_guide/IMG_4663.jpeg

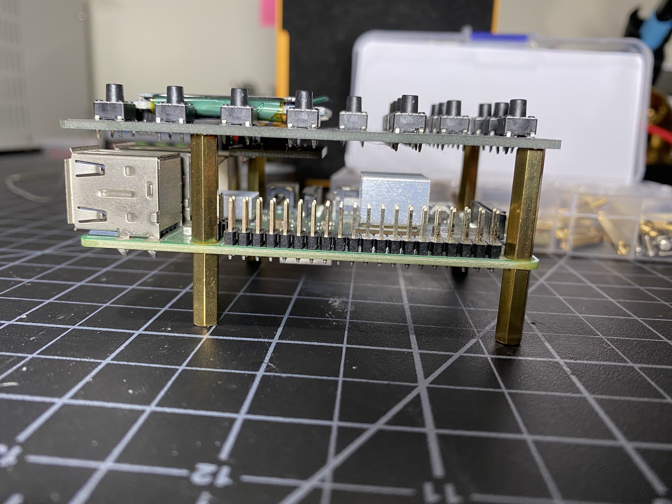
images/build_guide/IMG_4663.jpeg
