testezt/EZTFinder5/images/build_guide/IMG_4667.jpeg

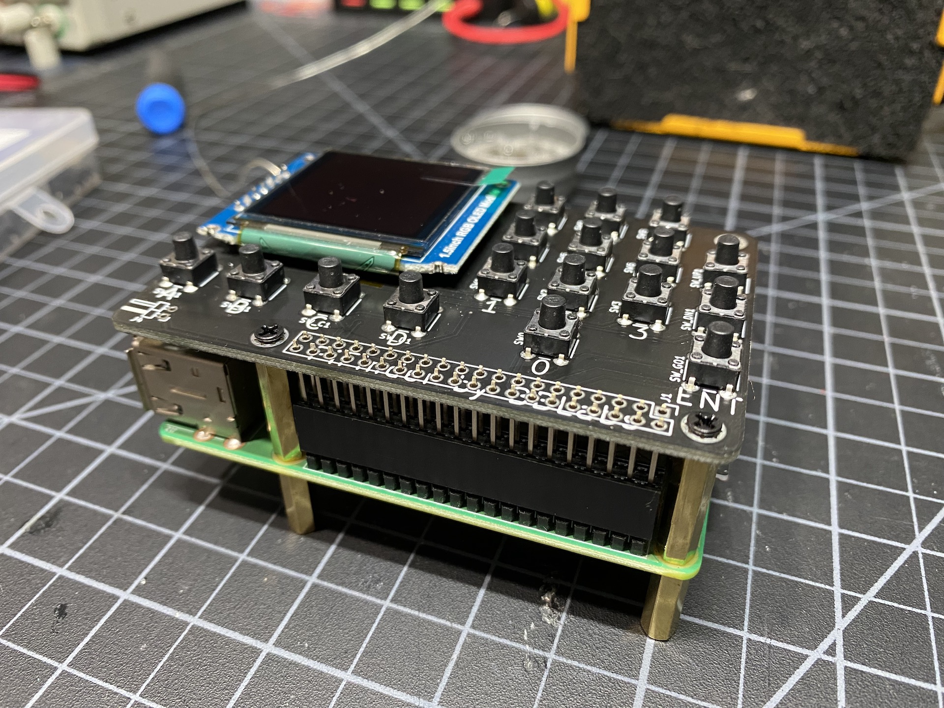
images/build_guide/IMG_4667.jpeg
