testezt/EZTFinder5/images/build_guide/IMG_4669.jpeg

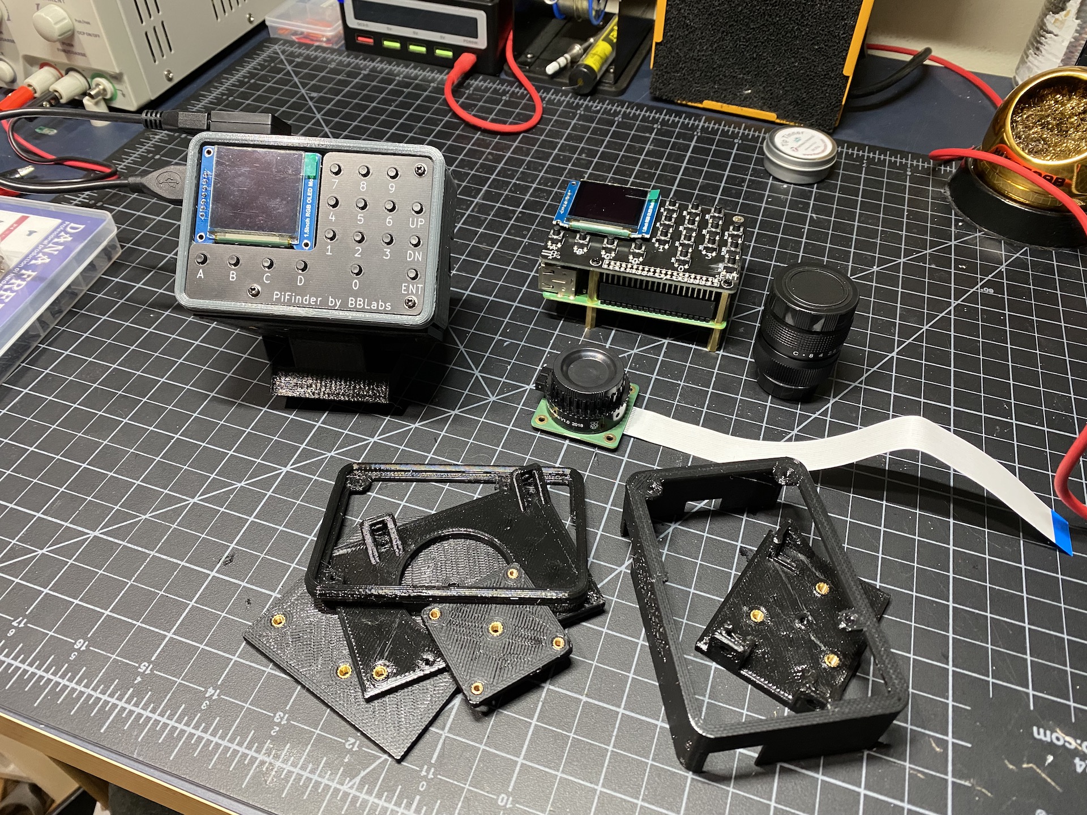
images/build_guide/IMG_4669.jpeg
