testezt/EZTFinder5/images/build_guide/IMG_4686.jpeg

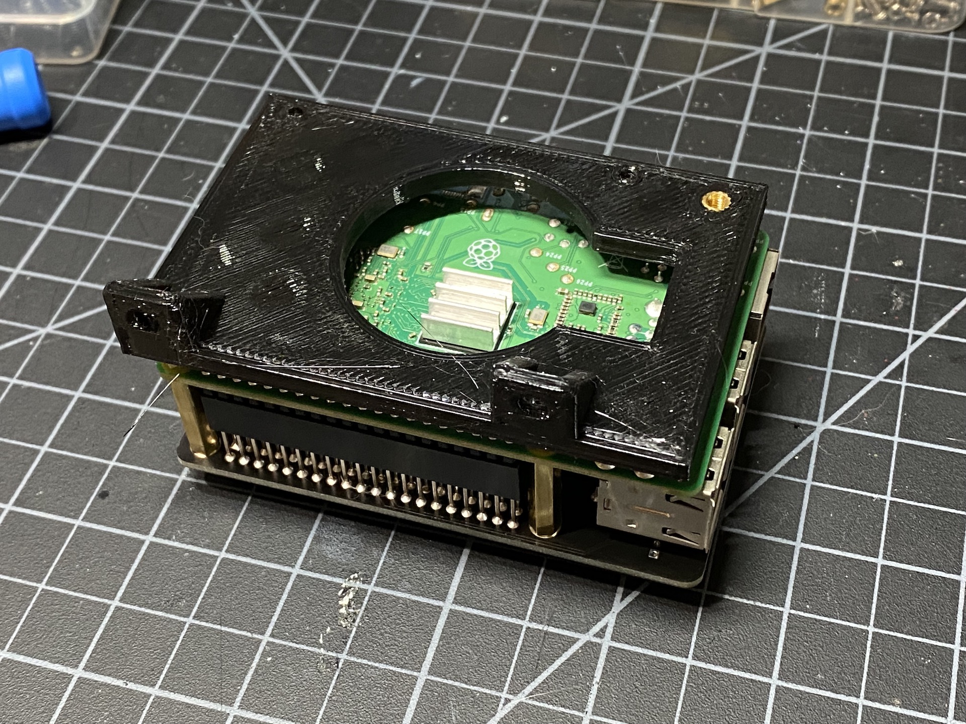
images/build_guide/IMG_4686.jpeg
