testezt/EZTFinder5/images/build_guide/IMG_4687.jpeg

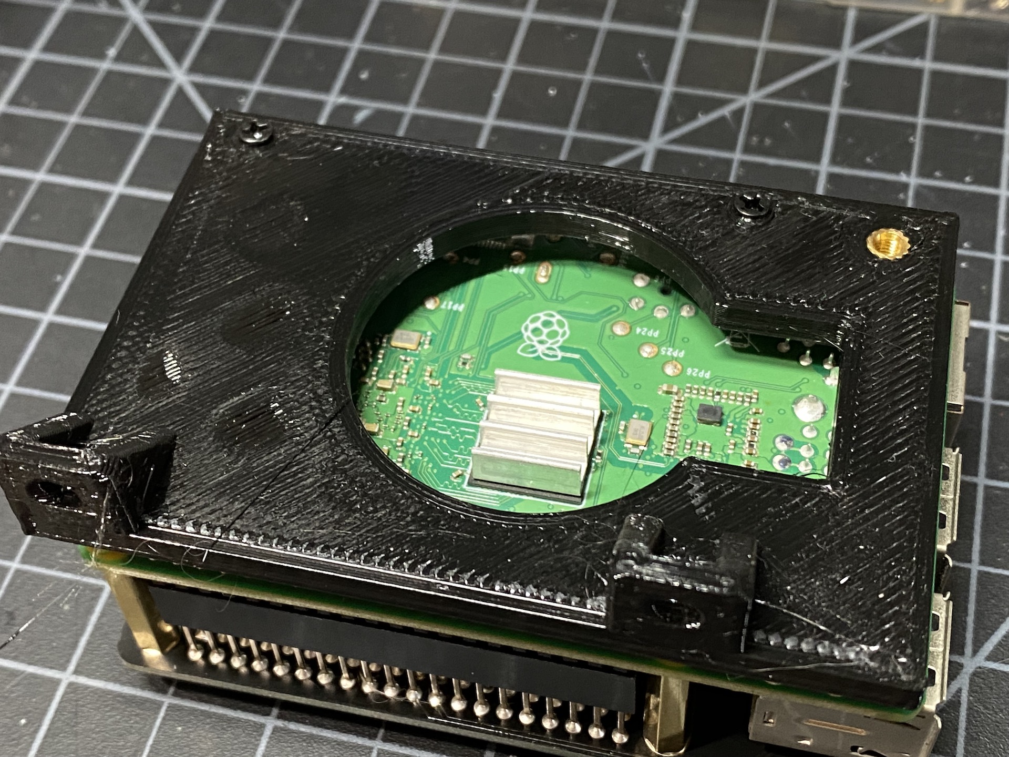
images/build_guide/IMG_4687.jpeg
