testezt/EZTFinder5/images/build_guide/IMG_4688.jpeg

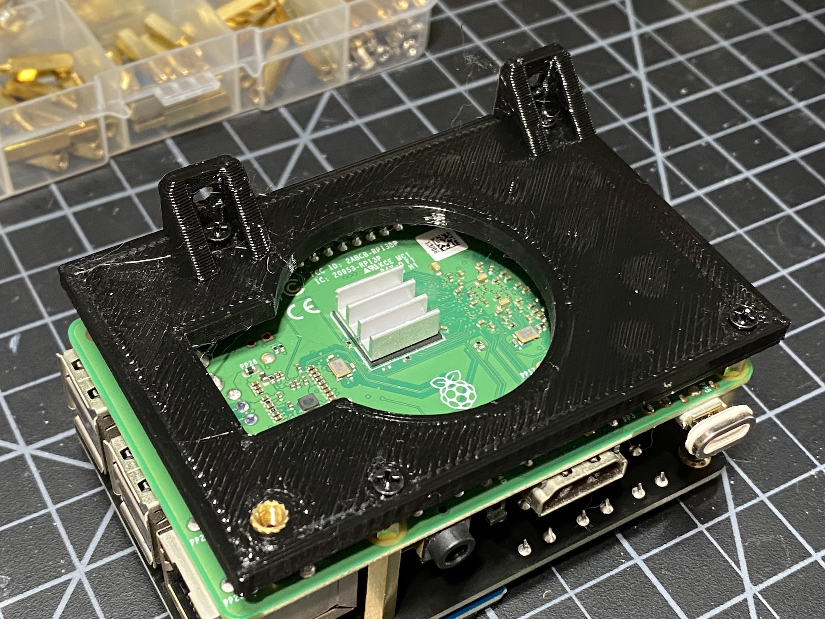
images/build_guide/IMG_4688.jpeg
