testezt/EZTFinder5/images/build_guide/IMG_4689.jpeg

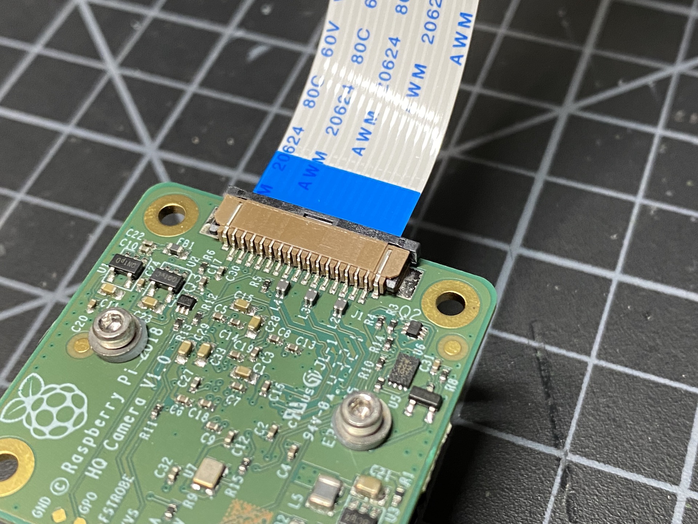
images/build_guide/IMG_4689.jpeg
