testezt/EZTFinder5/images/build_guide/IMG_4693.jpeg

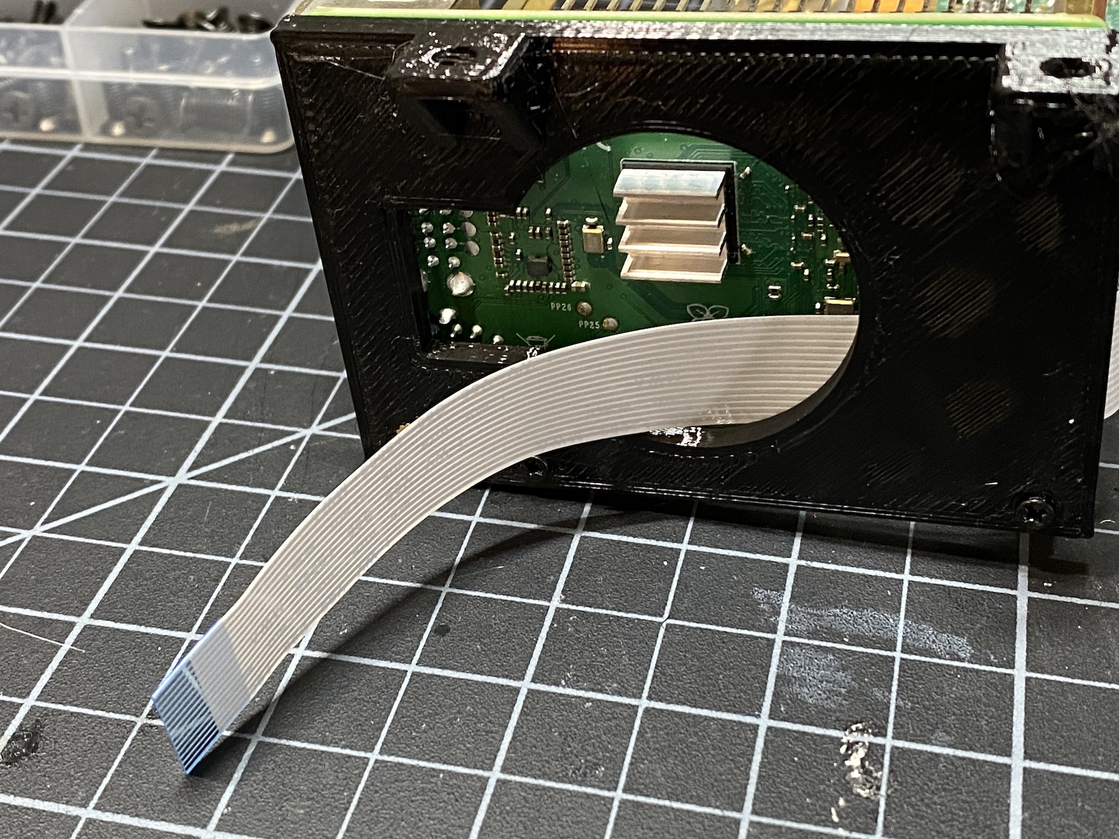
images/build_guide/IMG_4693.jpeg
