testezt/EZTFinder5/images/build_guide/IMG_4695.jpeg

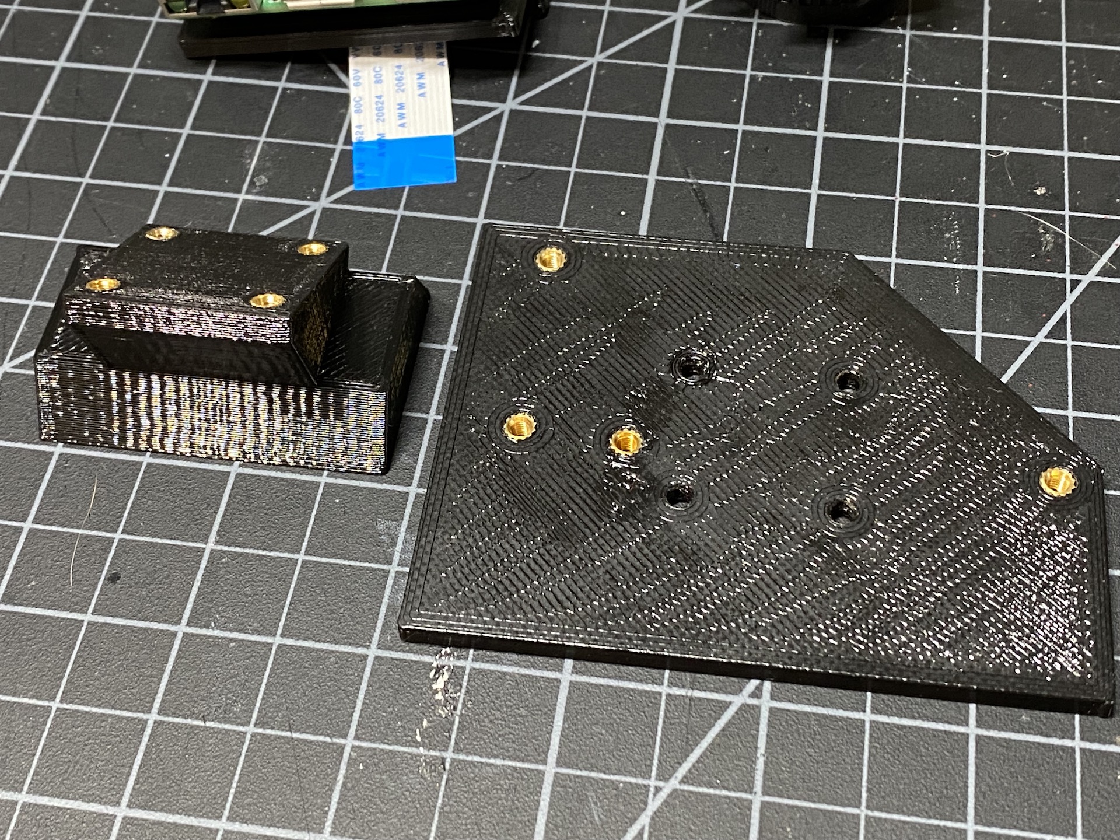
images/build_guide/IMG_4695.jpeg
