testezt/EZTFinder5/images/build_guide/IMG_4701.jpeg

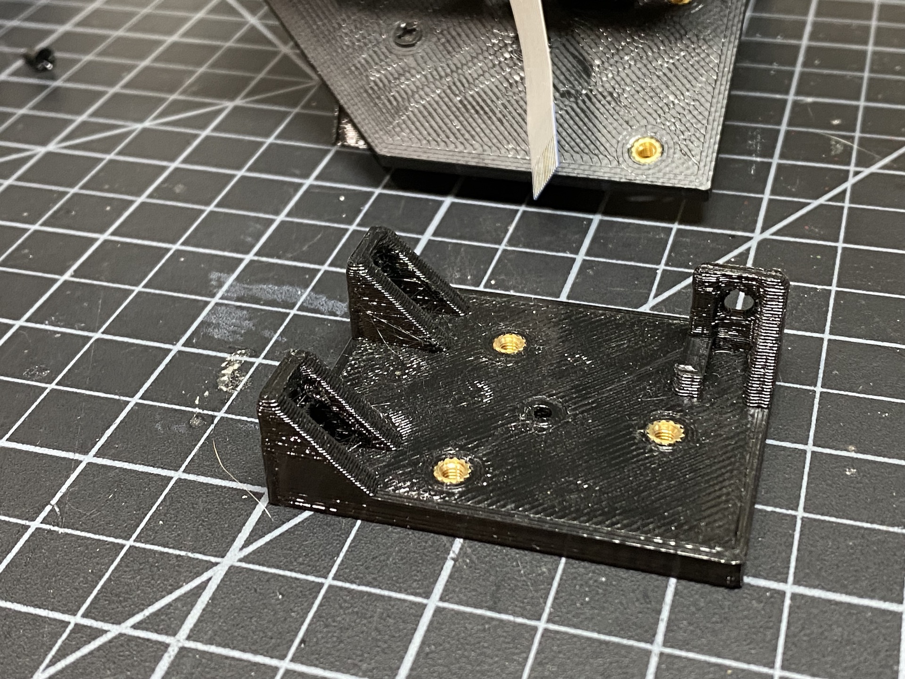
images/build_guide/IMG_4701.jpeg
