testezt/EZTFinder5/images/build_guide/IMG_4702.jpeg

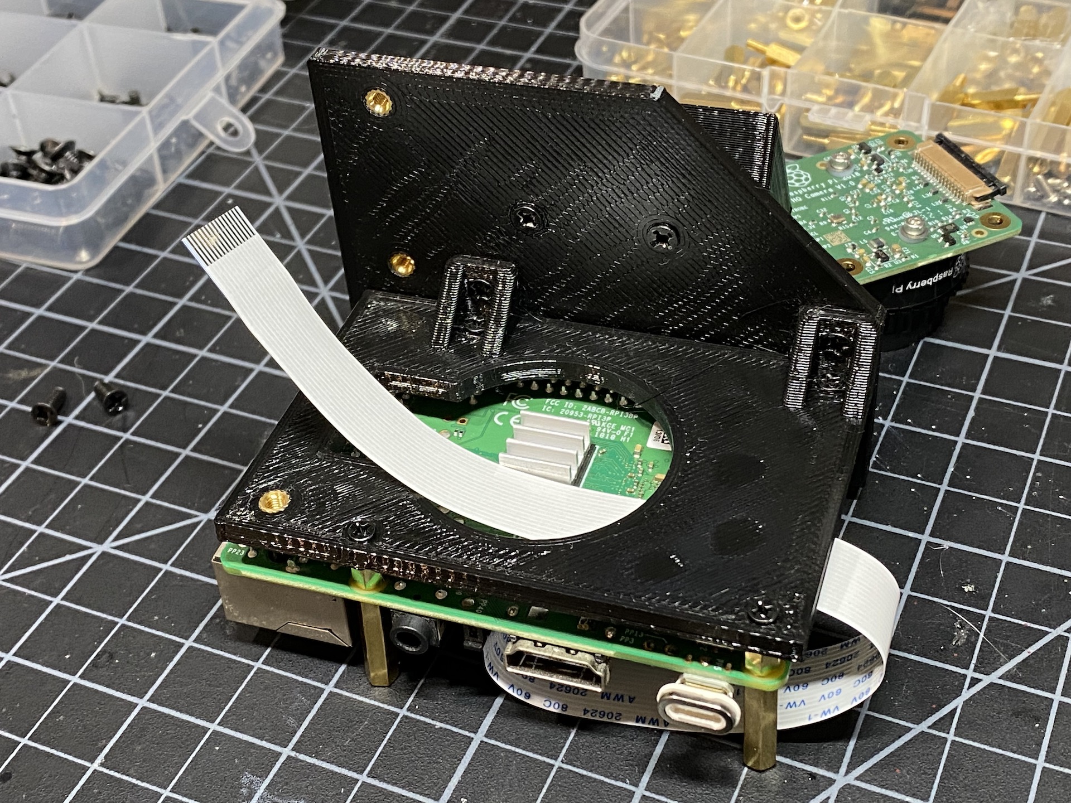
images/build_guide/IMG_4702.jpeg
