testezt/EZTFinder5/images/build_guide/IMG_4703.jpeg

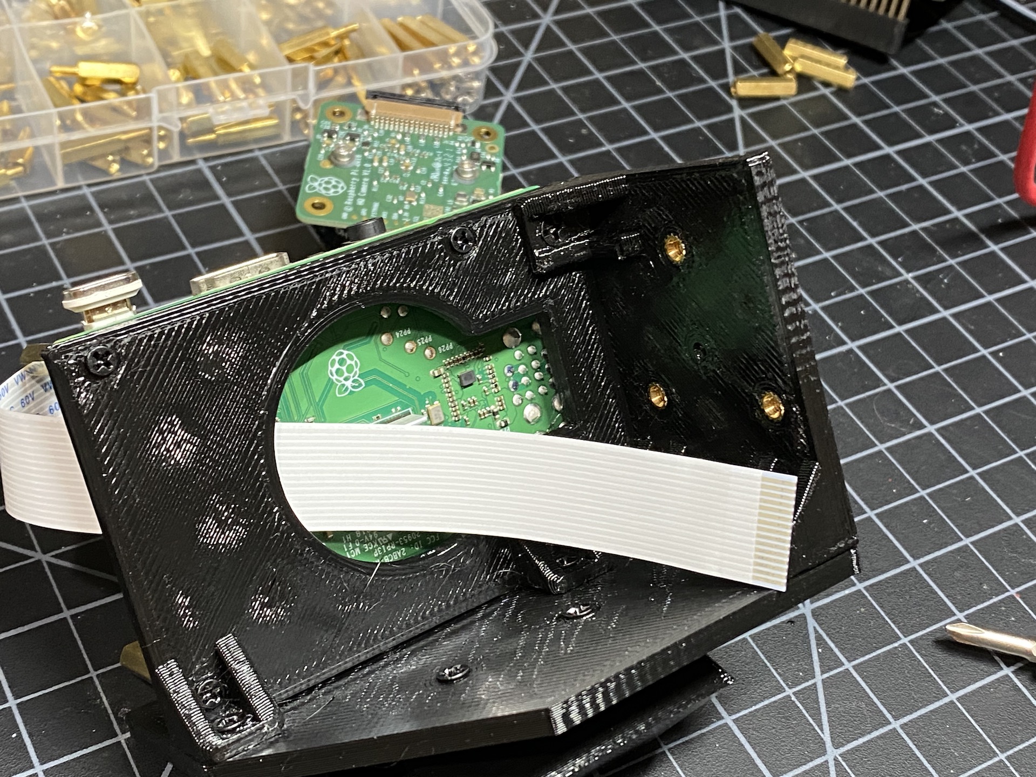
images/build_guide/IMG_4703.jpeg
