testezt/EZTFinder5/images/build_guide/IMG_4704.jpeg

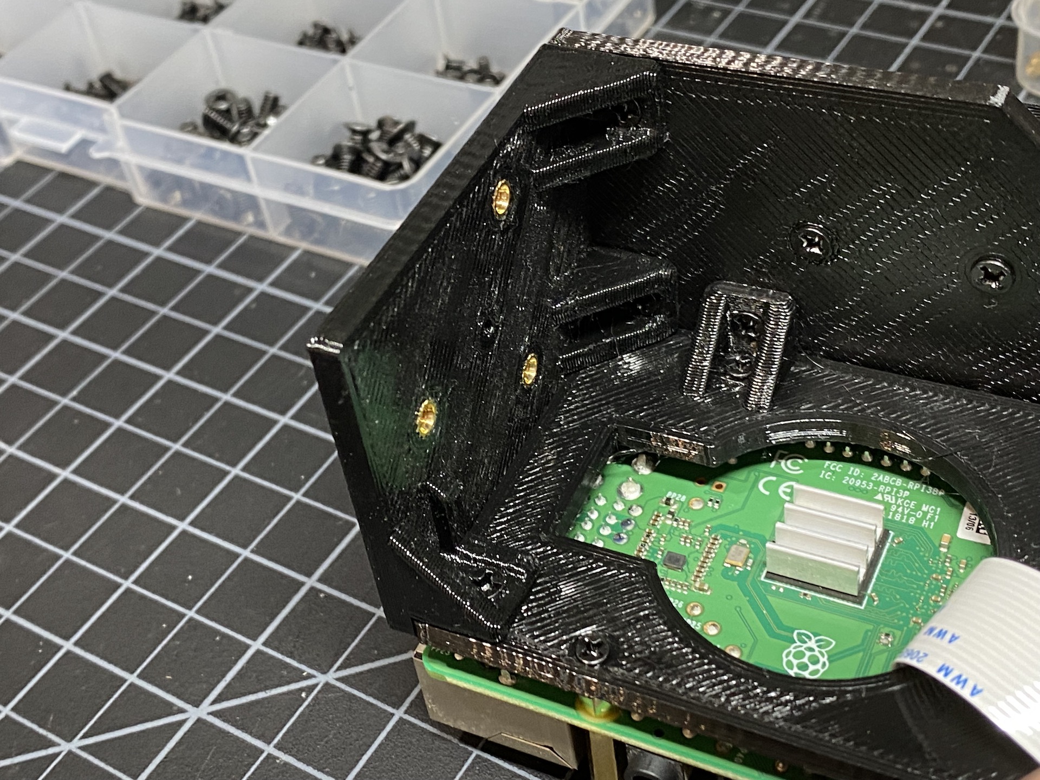
images/build_guide/IMG_4704.jpeg
