testezt/EZTFinder5/images/build_guide/IMG_4706.jpeg

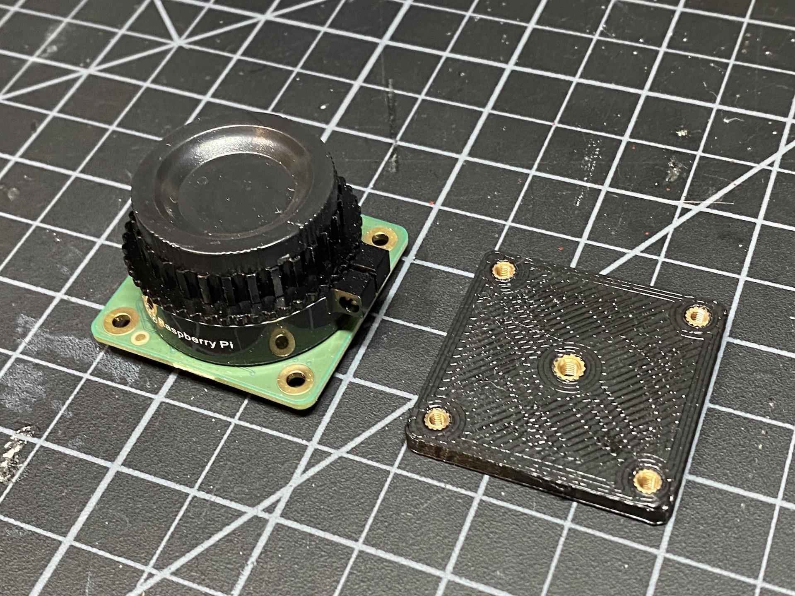
images/build_guide/IMG_4706.jpeg
