testezt/EZTFinder5/images/build_guide/IMG_4709.jpeg

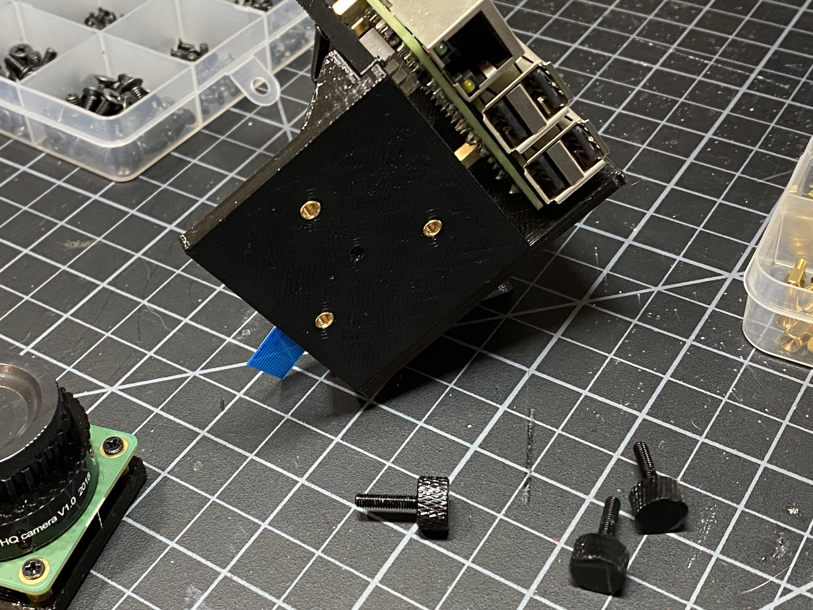
images/build_guide/IMG_4709.jpeg
