testezt/EZTFinder5/images/build_guide/IMG_4710.jpeg

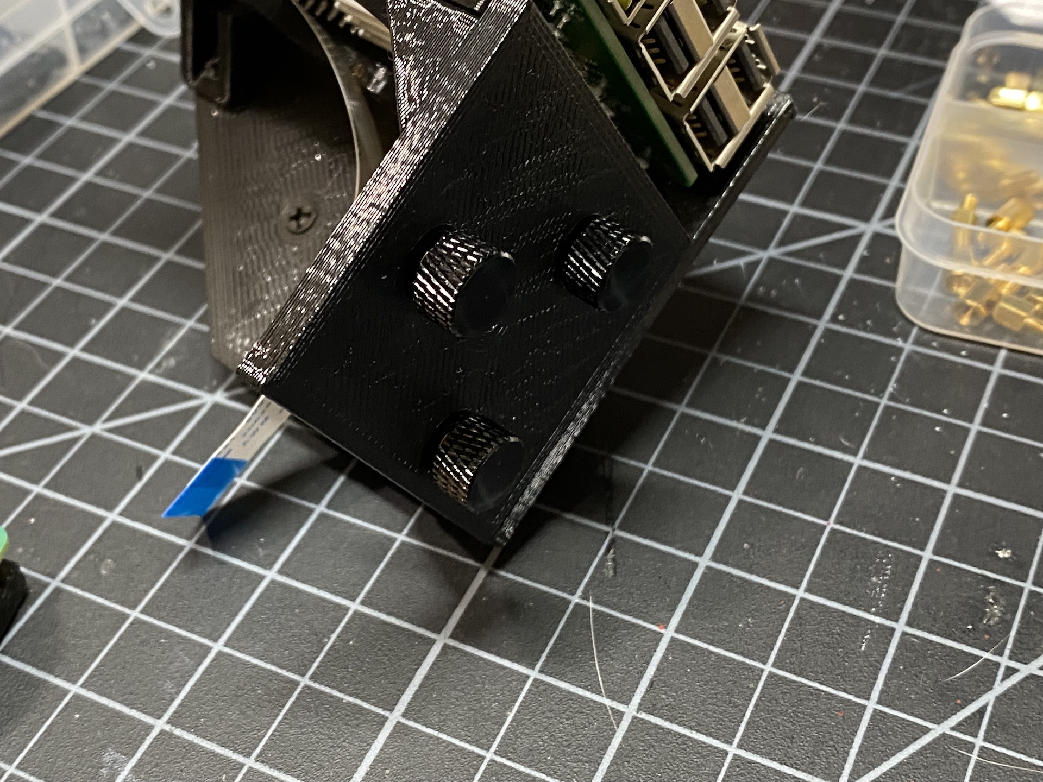
images/build_guide/IMG_4710.jpeg
