testezt/EZTFinder5/images/build_guide/IMG_4711.jpeg

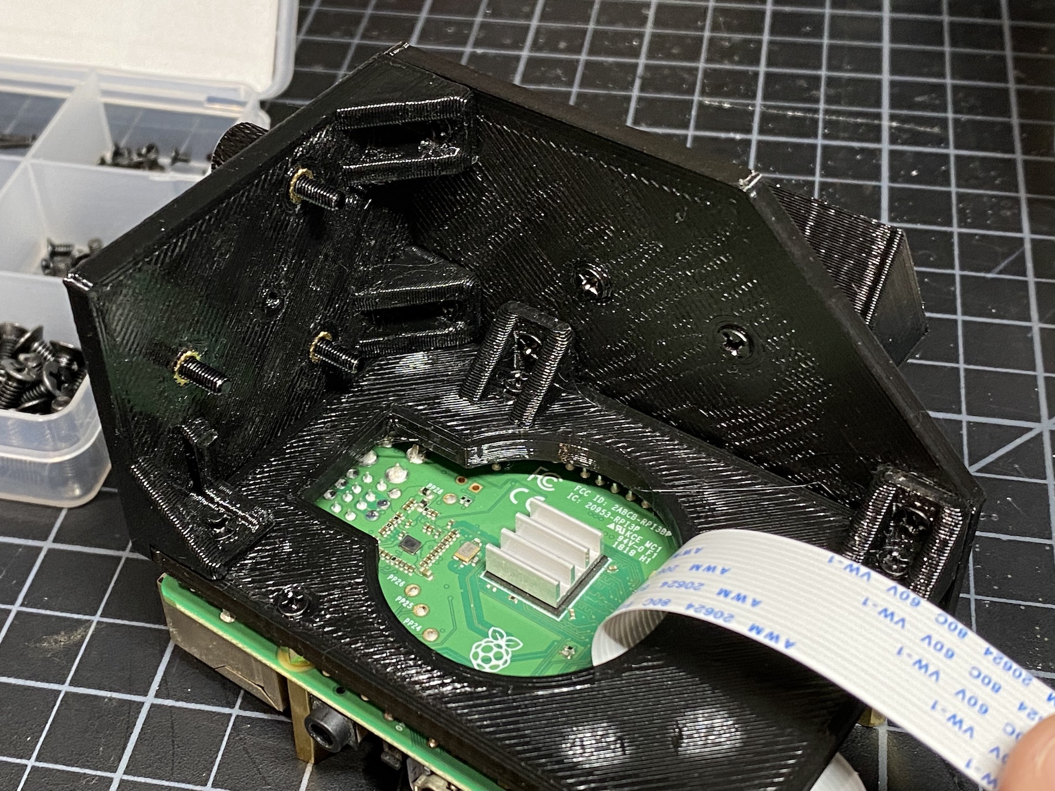
images/build_guide/IMG_4711.jpeg
