testezt/EZTFinder5/images/build_guide/IMG_4712.jpeg

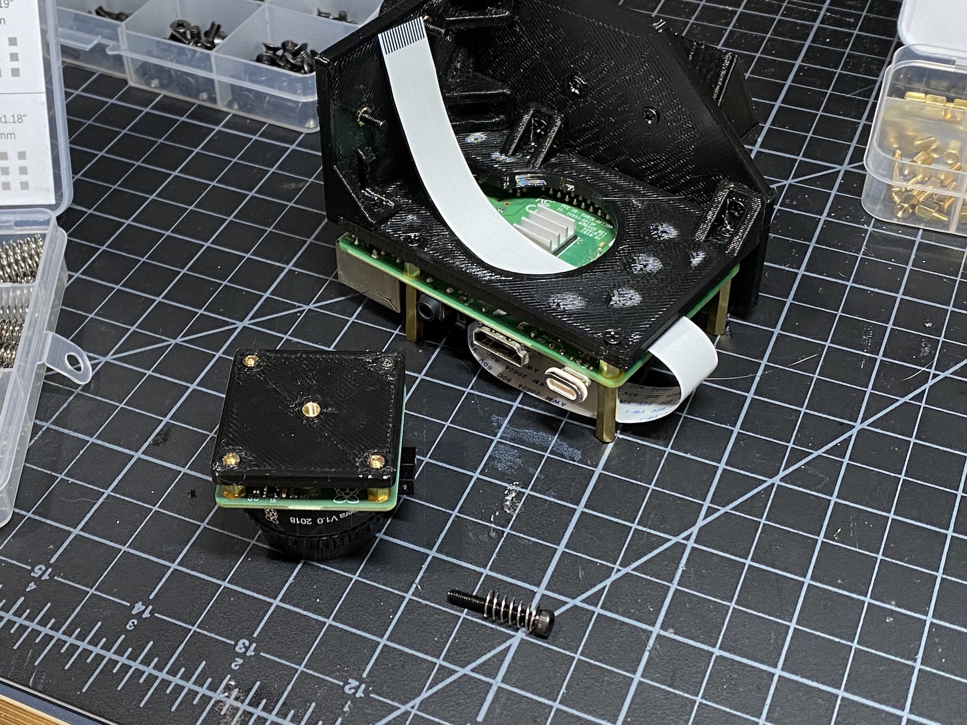
images/build_guide/IMG_4712.jpeg
