testezt/EZTFinder5/images/build_guide/IMG_4713.jpeg

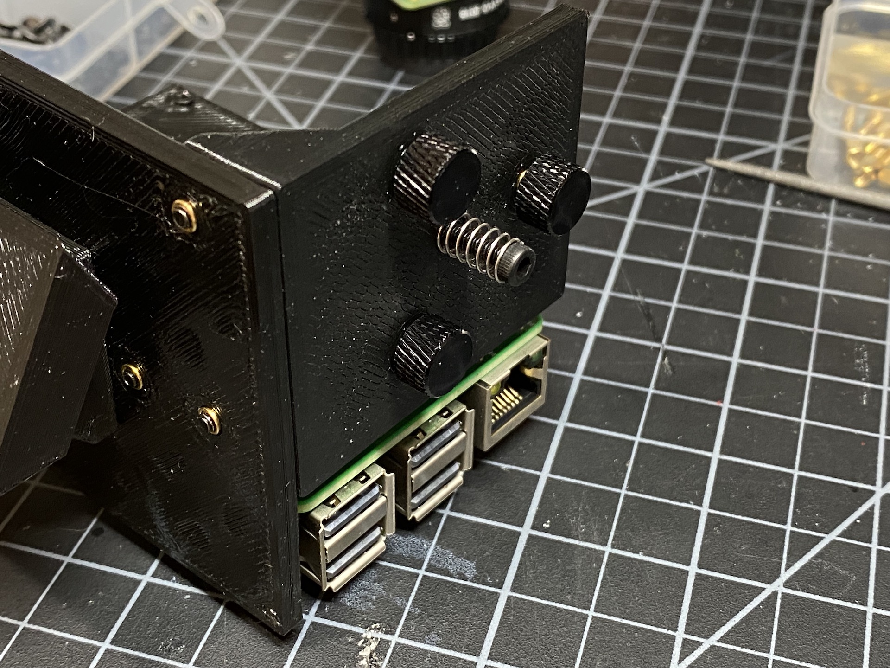
images/build_guide/IMG_4713.jpeg
