testezt/EZTFinder5/images/build_guide/IMG_4714.jpeg

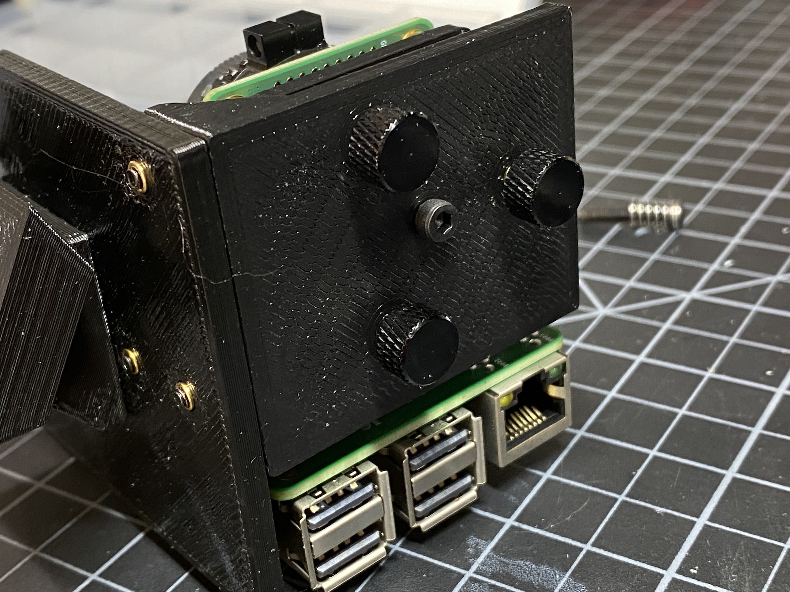
images/build_guide/IMG_4714.jpeg
