testezt/EZTFinder5/images/build_guide/IMG_4718.jpeg

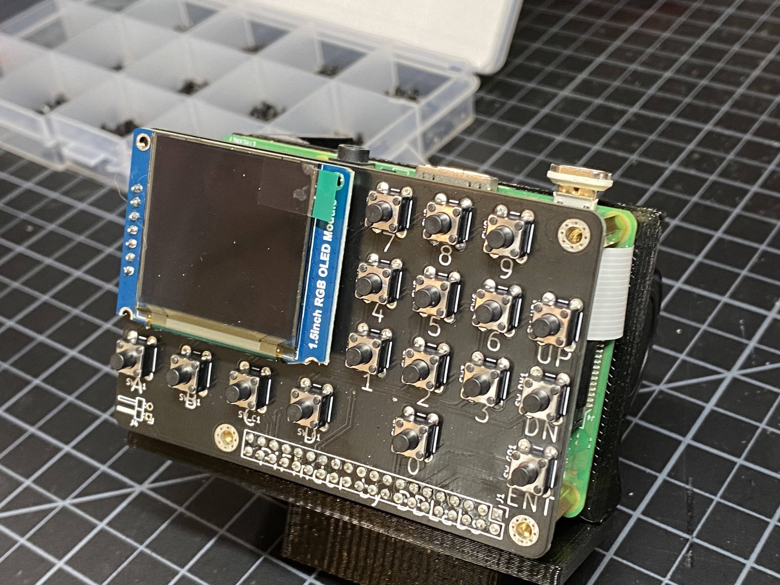
images/build_guide/IMG_4718.jpeg
