testezt/EZTFinder5/images/build_guide/IMG_4719.jpeg

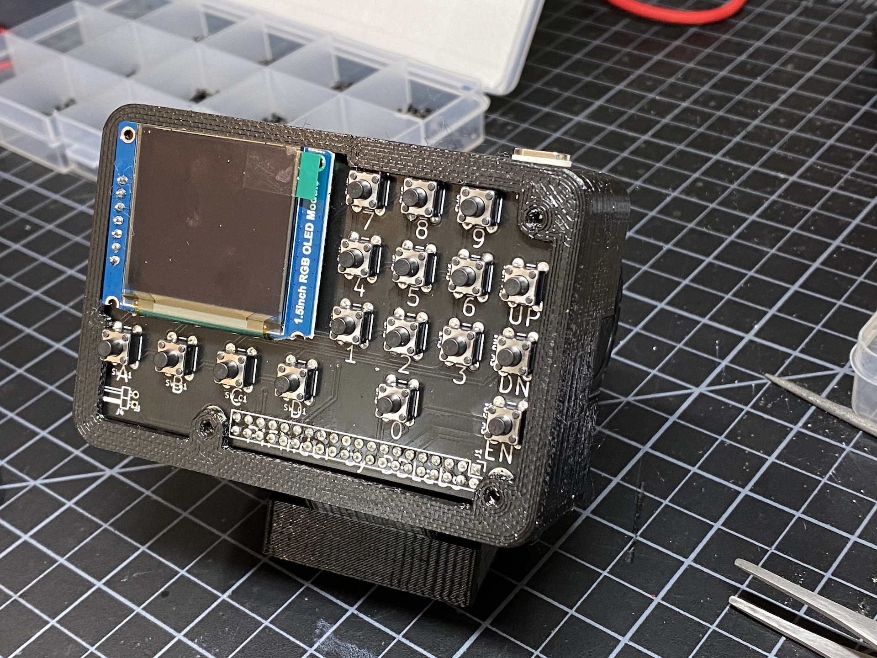
images/build_guide/IMG_4719.jpeg
