testezt/EZTFinder5/images/build_guide/IMG_4721.jpeg

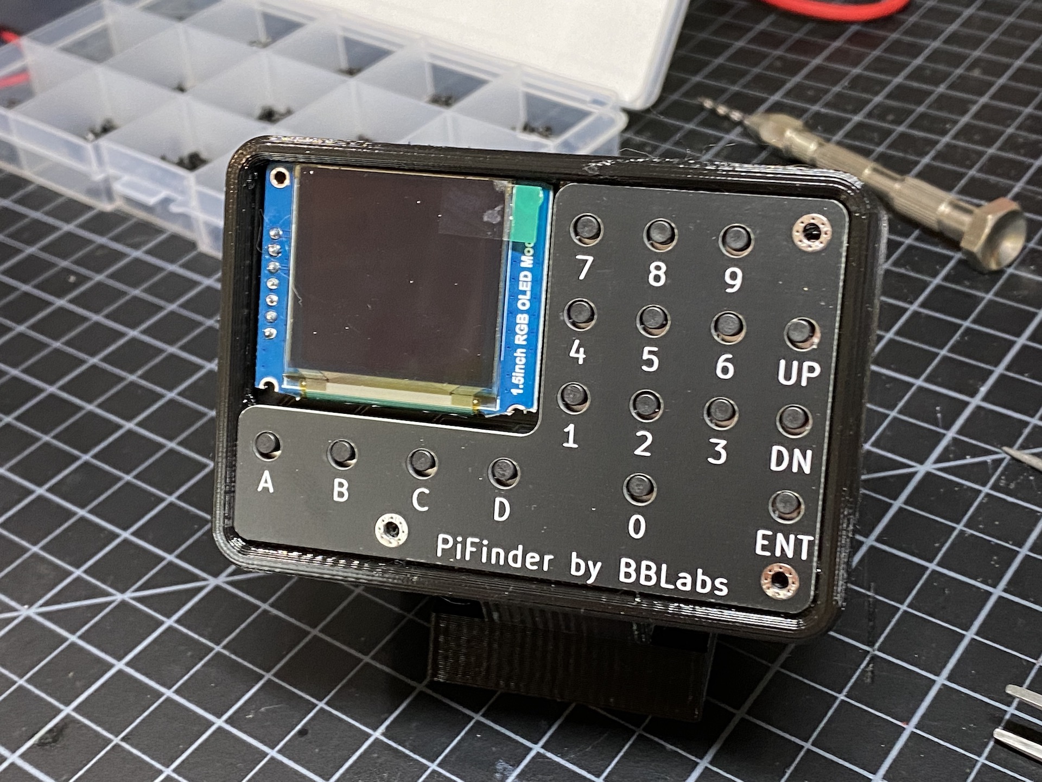
images/build_guide/IMG_4721.jpeg
