testezt/EZTFinder5/images/build_guide/IMG_4724.jpeg

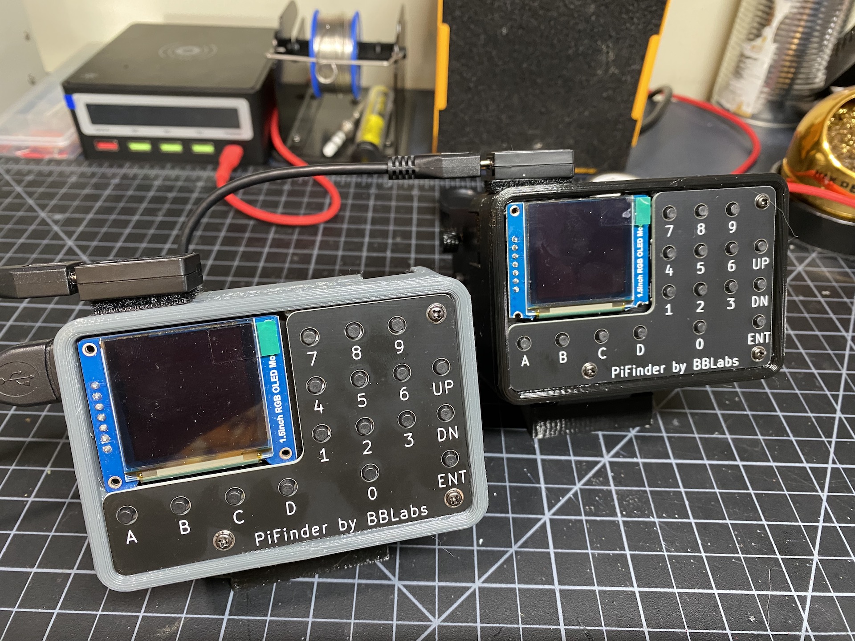
images/build_guide/IMG_4724.jpeg
