testezt/EZTFinder5/images/build_guide/IMG_4809.jpeg

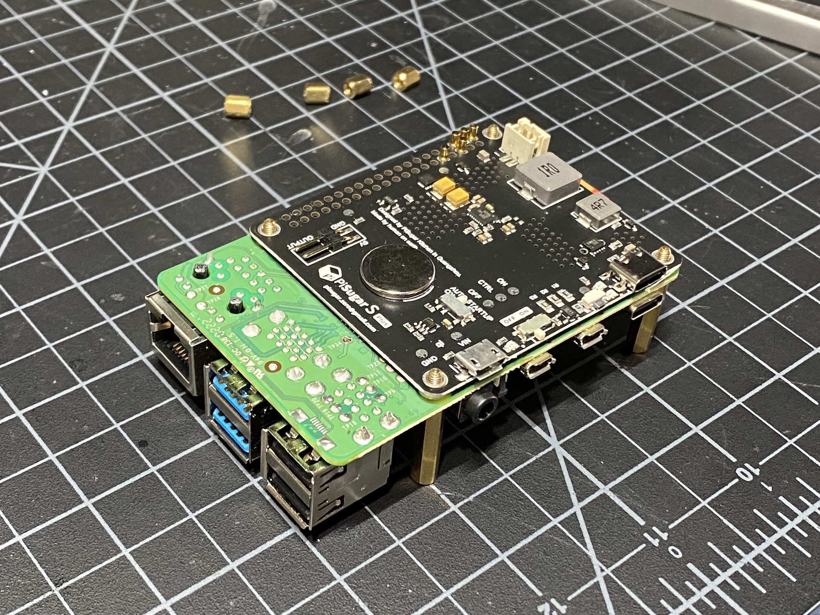
images/build_guide/IMG_4809.jpeg
