testezt/EZTFinder5/images/build_guide/IMG_4813.jpeg

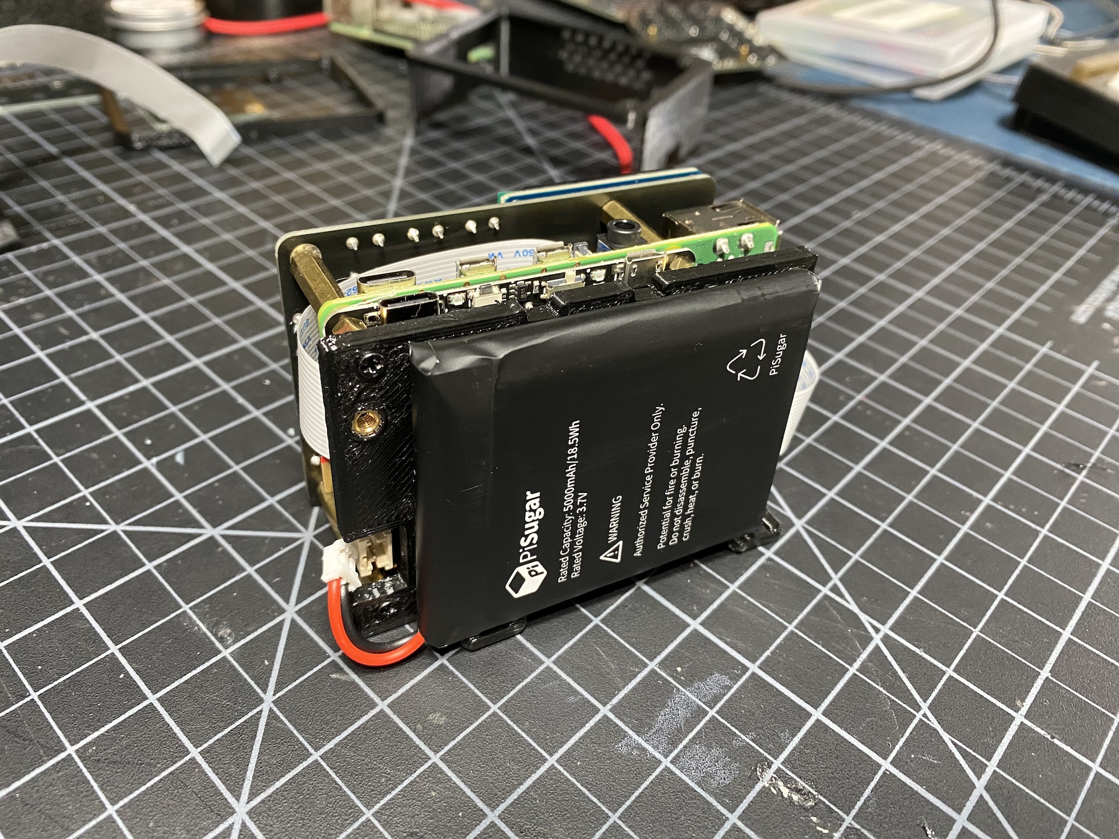
images/build_guide/IMG_4813.jpeg
