testezt/EZTFinder5/images/build_guide/IMG_4814.jpeg

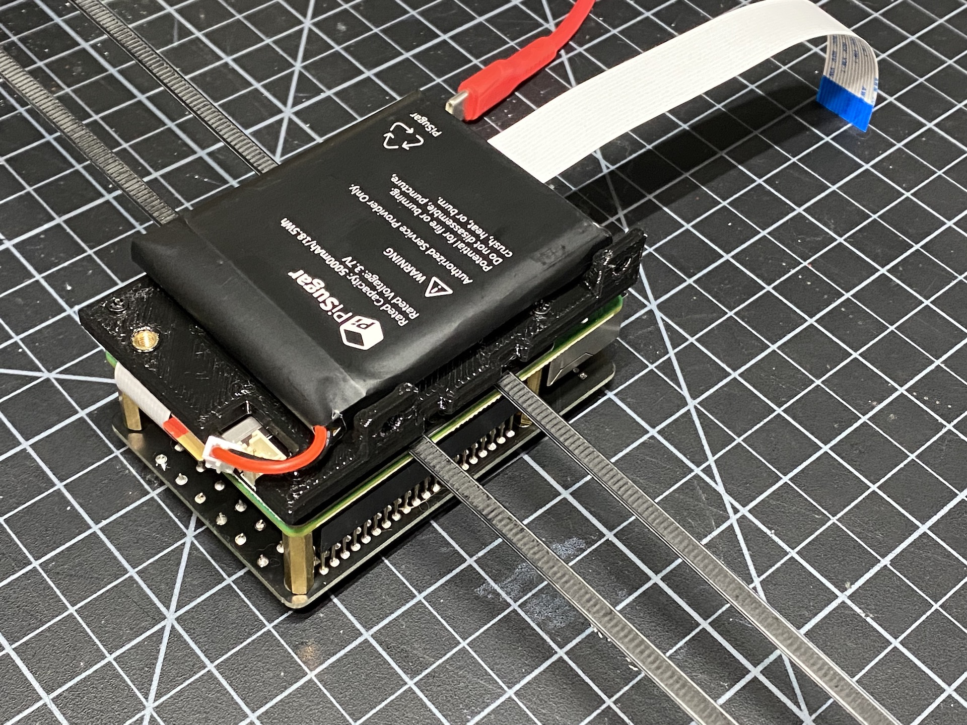
images/build_guide/IMG_4814.jpeg
