testezt/EZTFinder5/images/build_guide/IMG_4819.jpeg

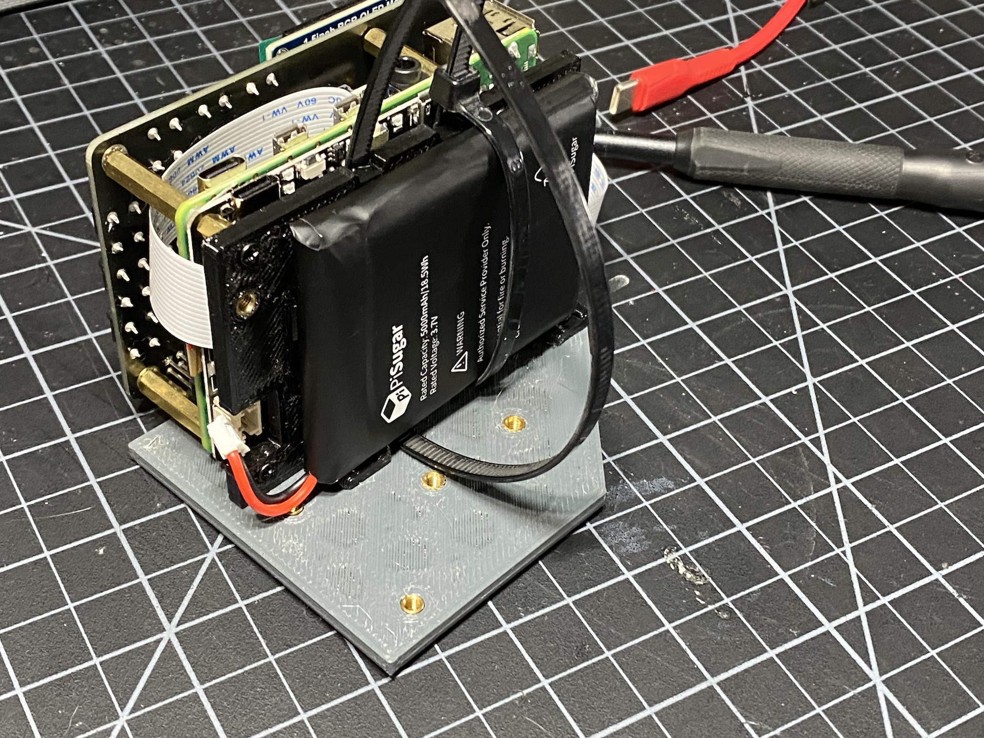
images/build_guide/IMG_4819.jpeg
