testezt/EZTFinder5/images/build_guide/IMG_4821.jpeg

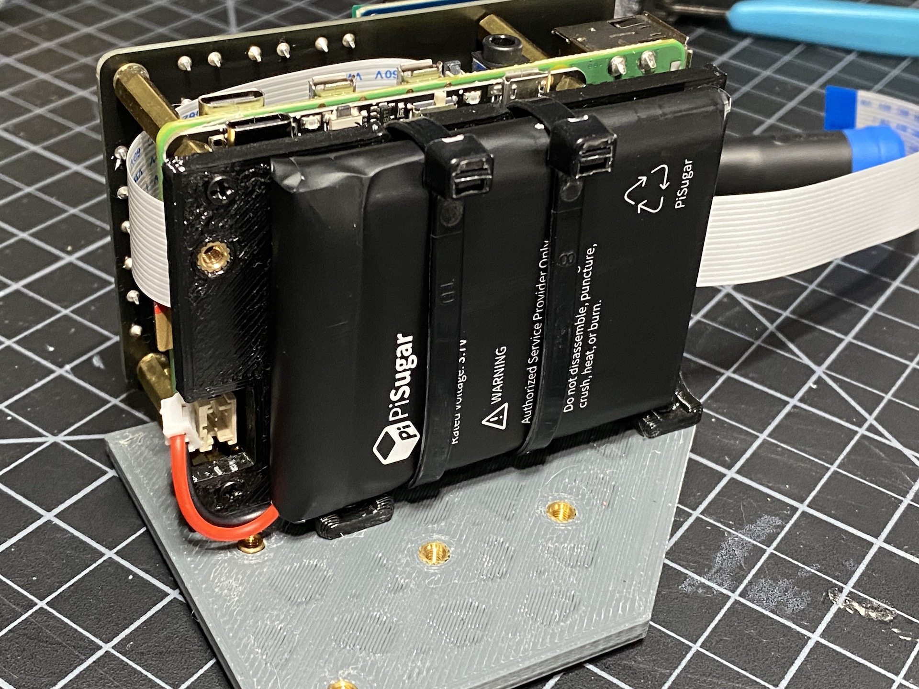
images/build_guide/IMG_4821.jpeg
