testezt/EZTFinder5/images/build_guide/IMG_4822.jpeg

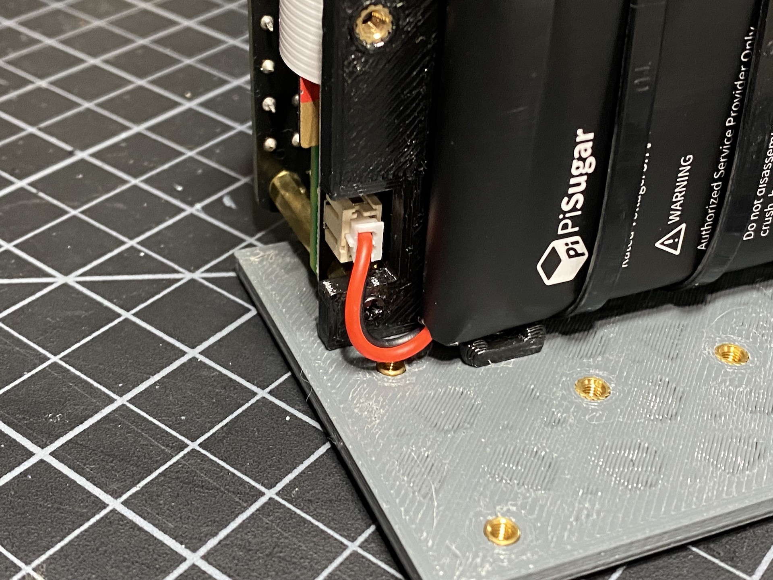
images/build_guide/IMG_4822.jpeg
