testezt/EZTFinder5/images/build_guide/IMG_4824.jpeg

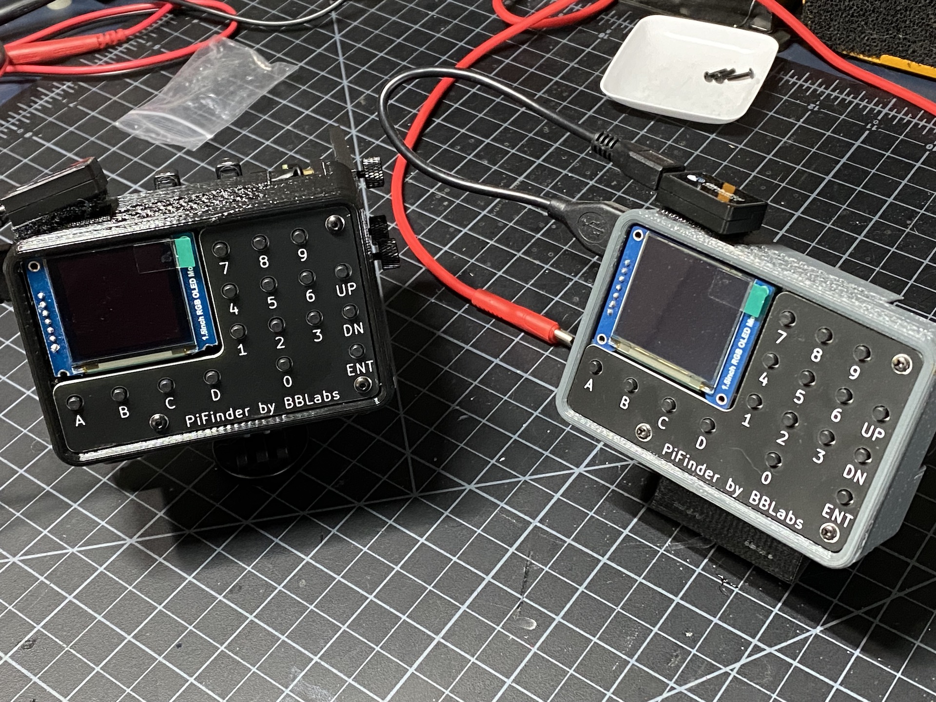
images/build_guide/IMG_4824.jpeg
