testezt/EZTFinder5/images/build_guide/IMG_4825.jpeg

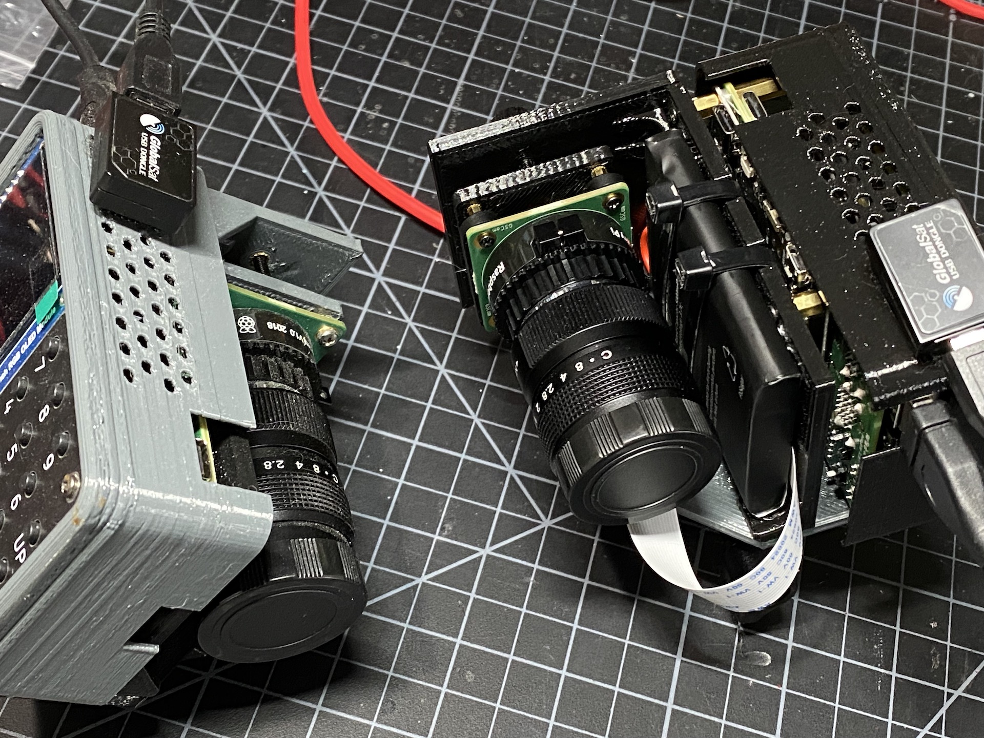
images/build_guide/IMG_4825.jpeg
