testezt/EZTFinder5/images/build_guide/IMG_4829.jpeg

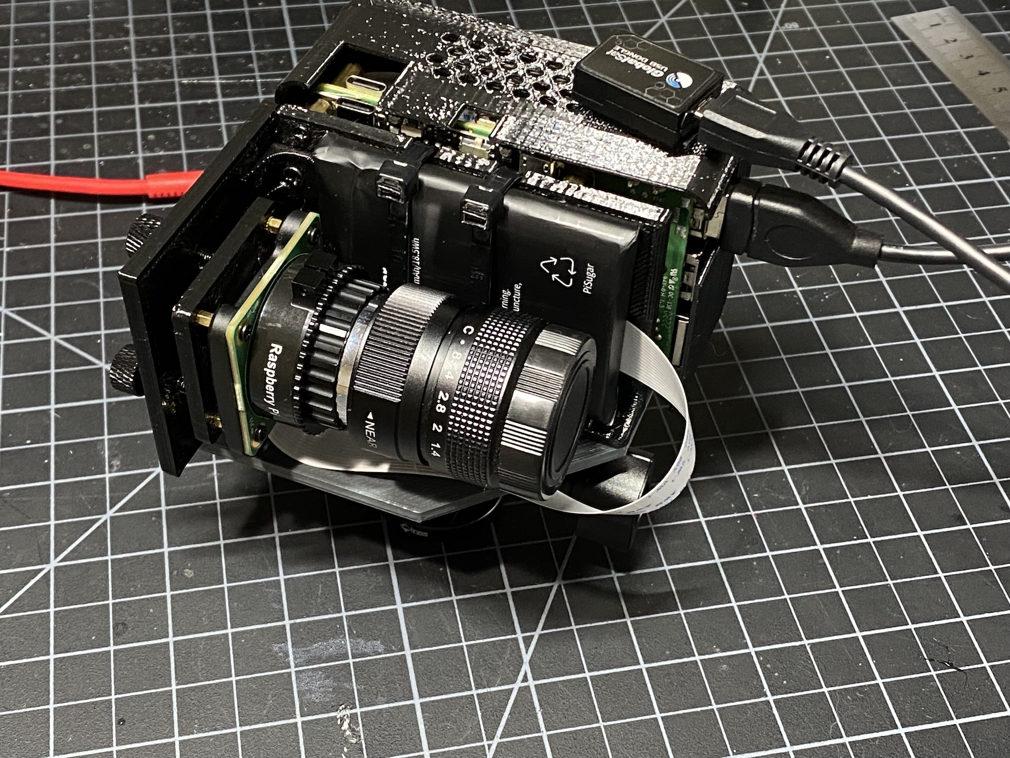
images/build_guide/IMG_4829.jpeg
