testezt/EZTFinder5/images/build_guide/IMG_4830.jpeg

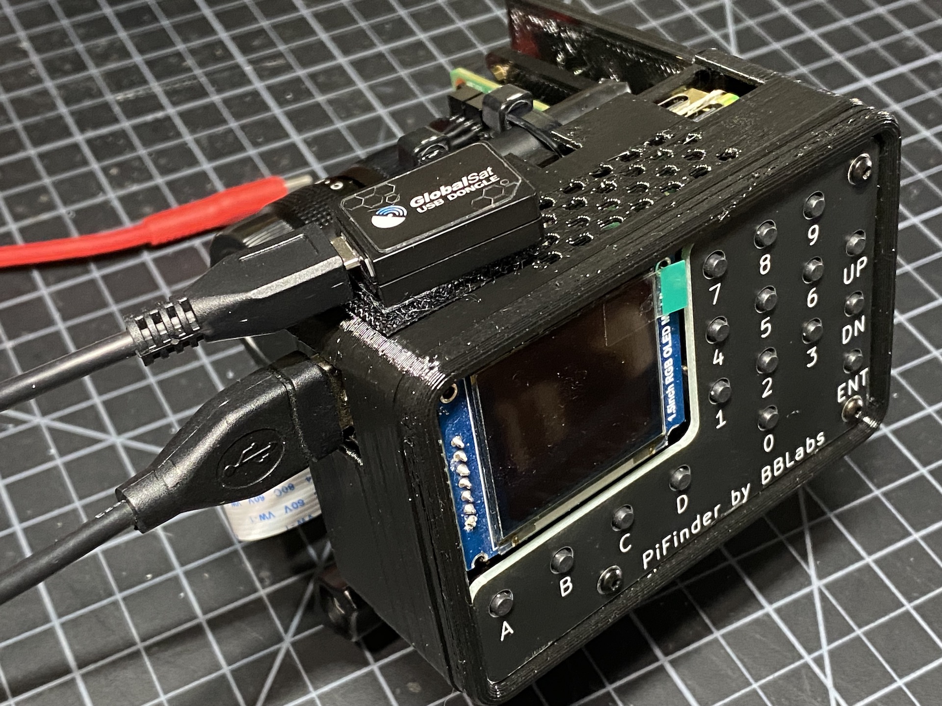
images/build_guide/IMG_4830.jpeg
