testezt/EZTFinder5/images/build_guide/IMG_4831.jpeg

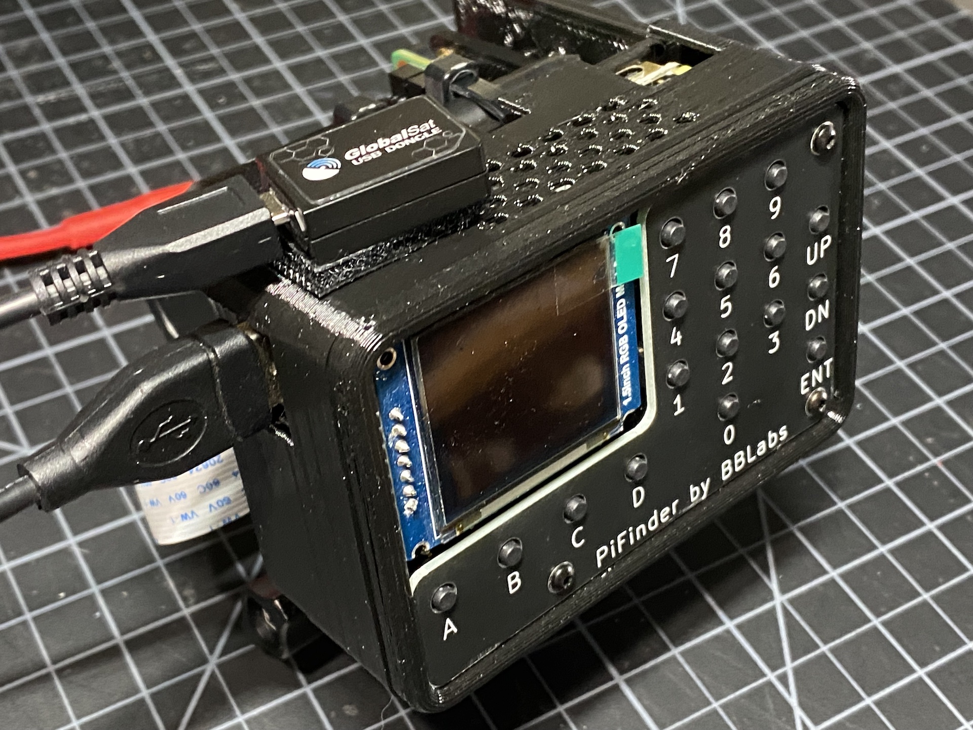
images/build_guide/IMG_4831.jpeg
