testezt/EZTFinder5/images/build_guide/led_build_01.jpeg

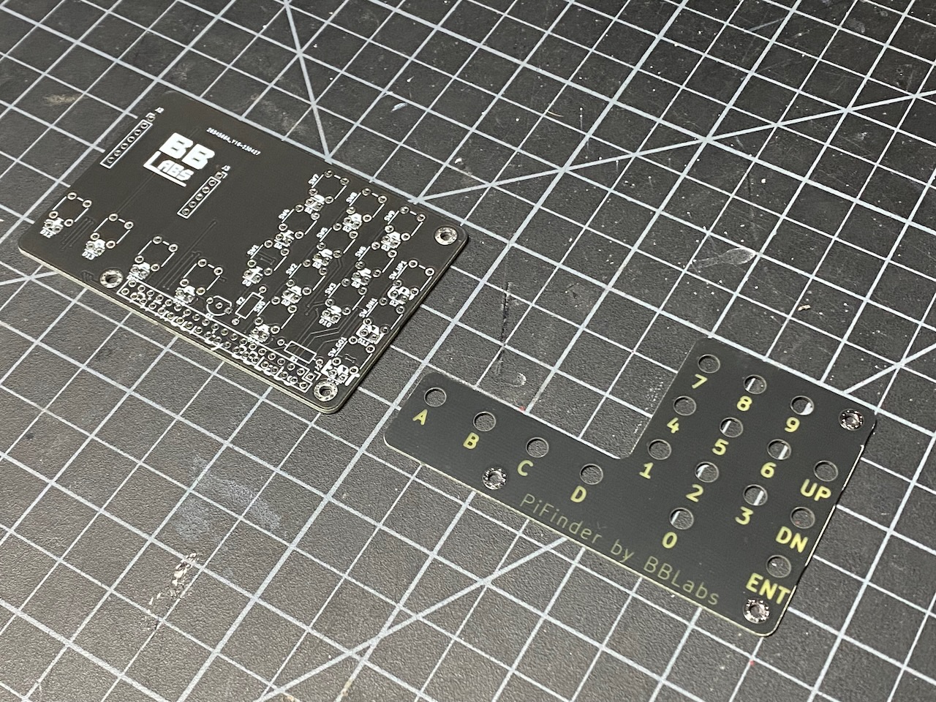
images/build_guide/led_build_01.jpeg
