testezt/EZTFinder5/images/build_guide/led_build_02.jpeg

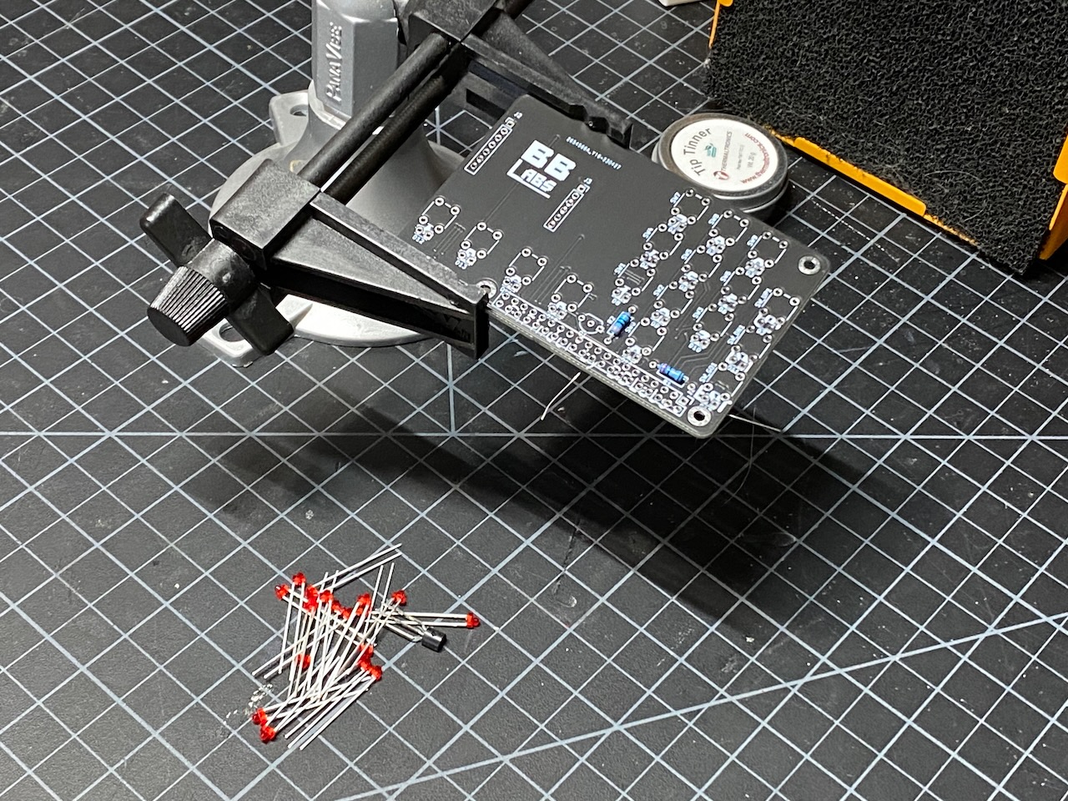
images/build_guide/led_build_02.jpeg
