testezt/EZTFinder5/images/build_guide/led_build_04.jpeg

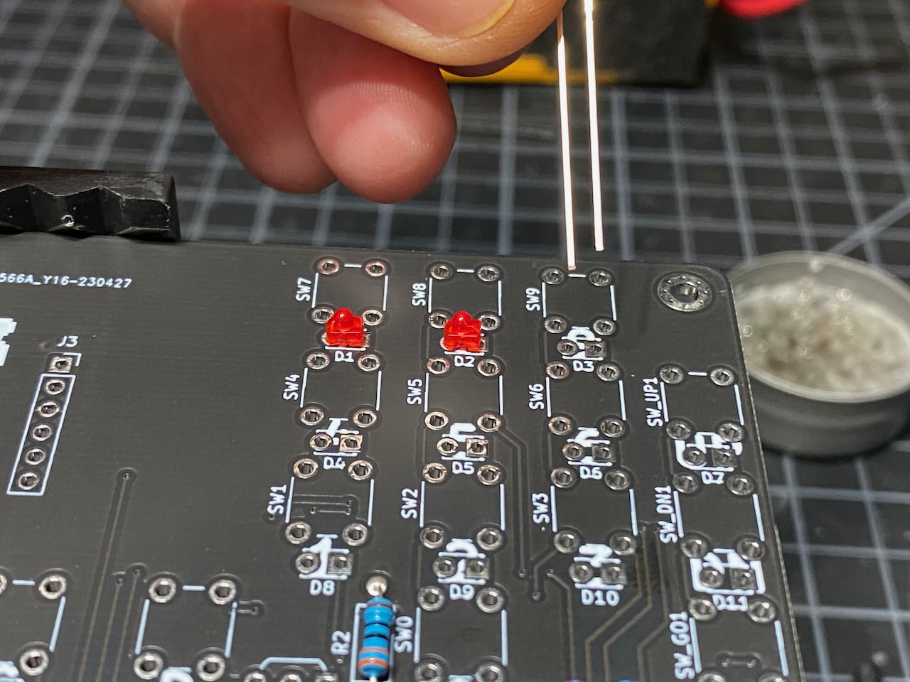
images/build_guide/led_build_04.jpeg
