testezt/EZTFinder5/images/build_guide/led_build_05.jpeg

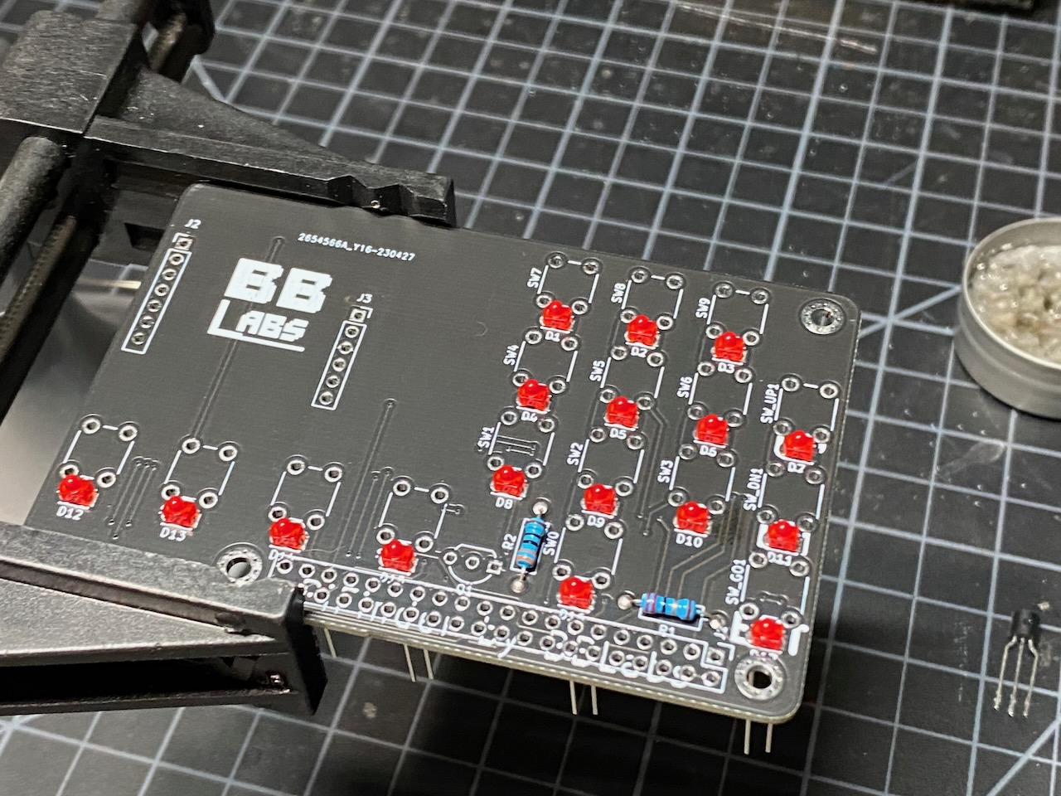
images/build_guide/led_build_05.jpeg
