testezt/EZTFinder5/images/build_guide/led_build_06.jpeg

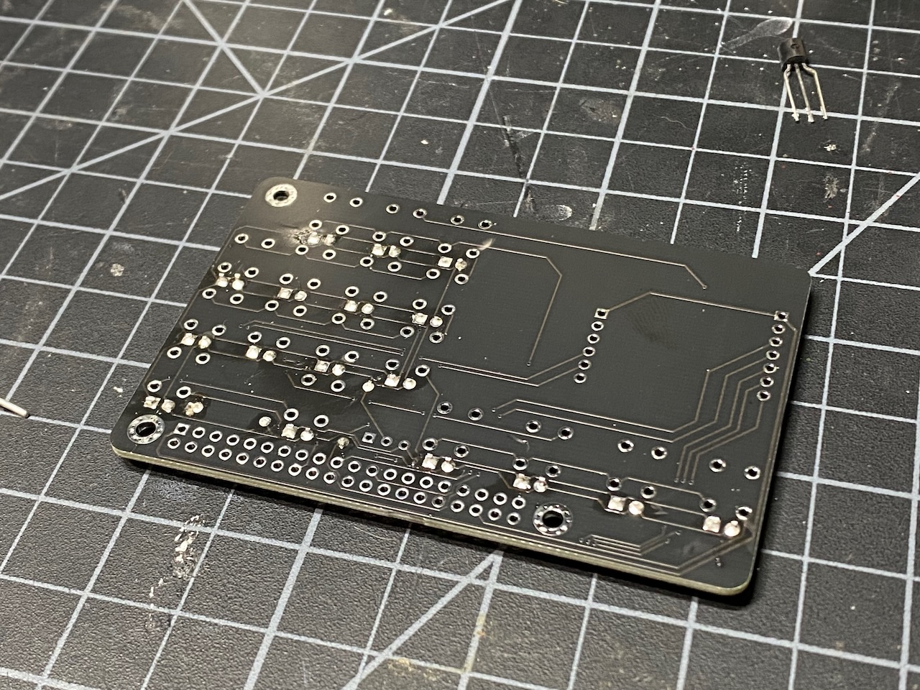
images/build_guide/led_build_06.jpeg
