testezt/EZTFinder5/images/build_guide/led_build_07.jpeg

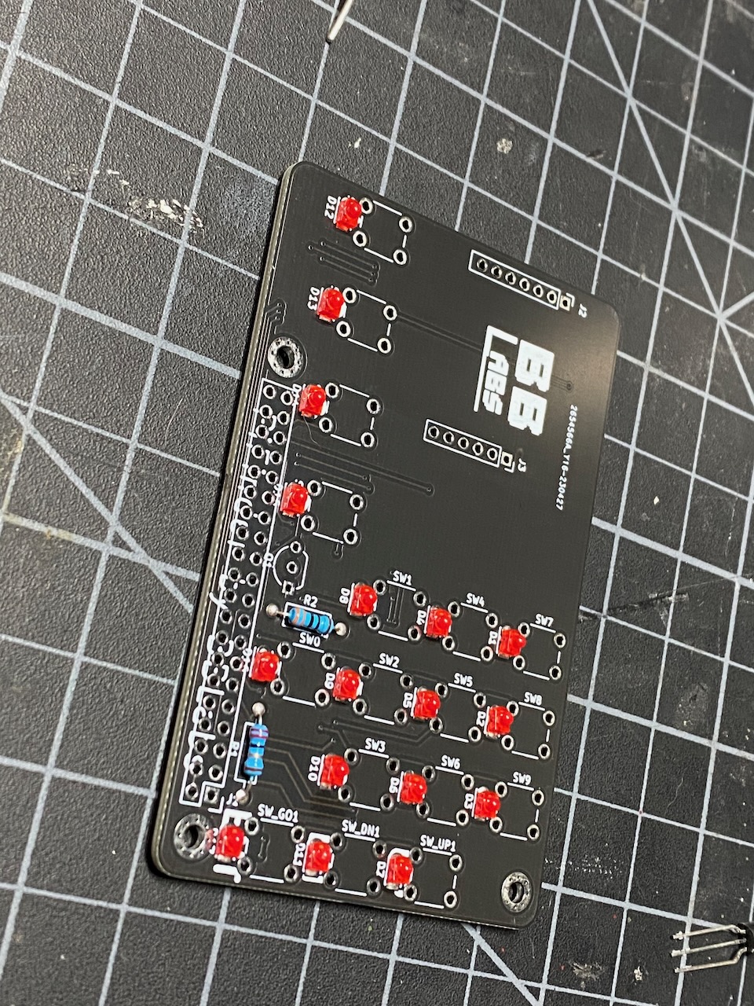
images/build_guide/led_build_07.jpeg
