testezt/EZTFinder5/images/build_guide/led_build_10.jpeg

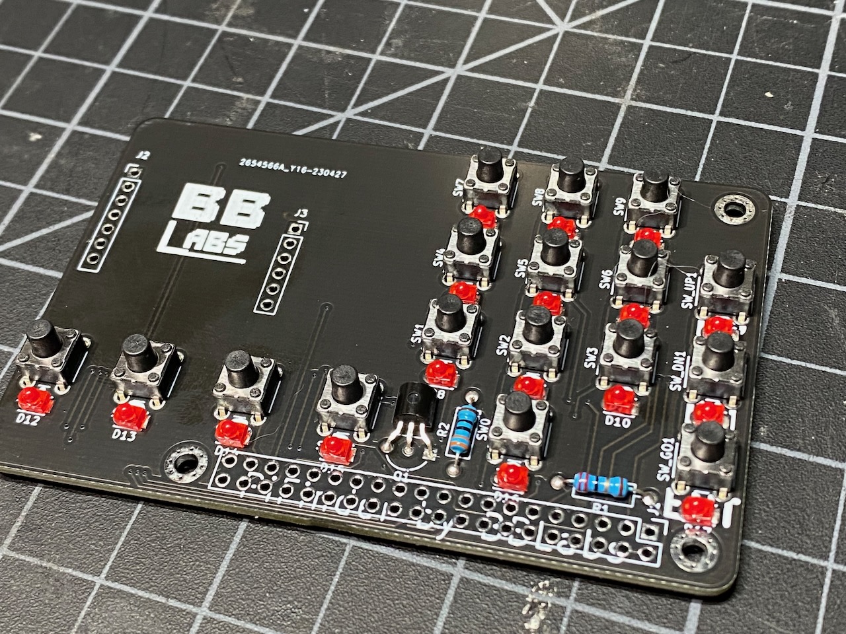
images/build_guide/led_build_10.jpeg
