testezt/EZTFinder5/images/build_guide/led_build_11.jpeg

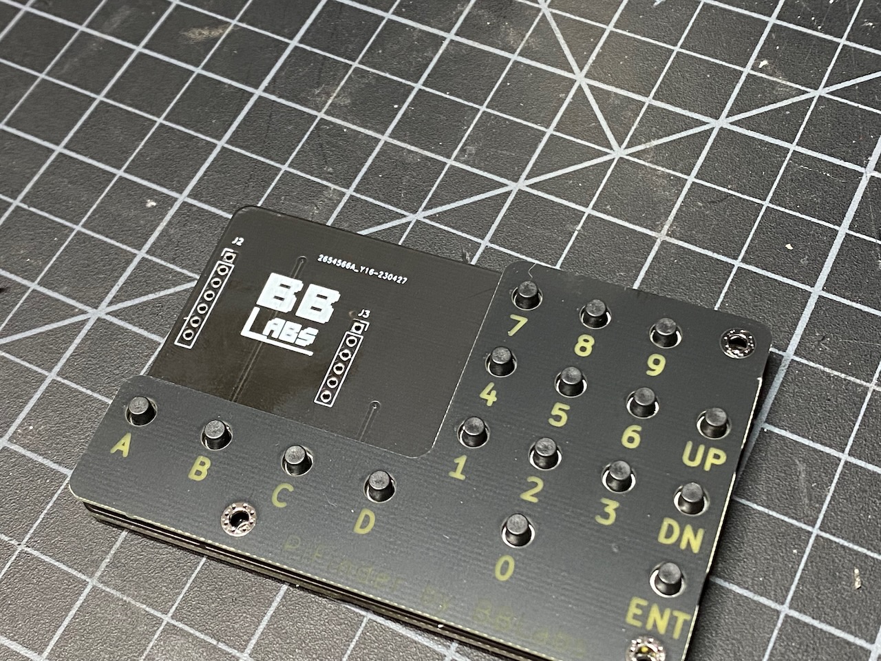
images/build_guide/led_build_11.jpeg
