testezt/EZTFinder5/images/build_guide/v1.6/build_guide_42.jpeg

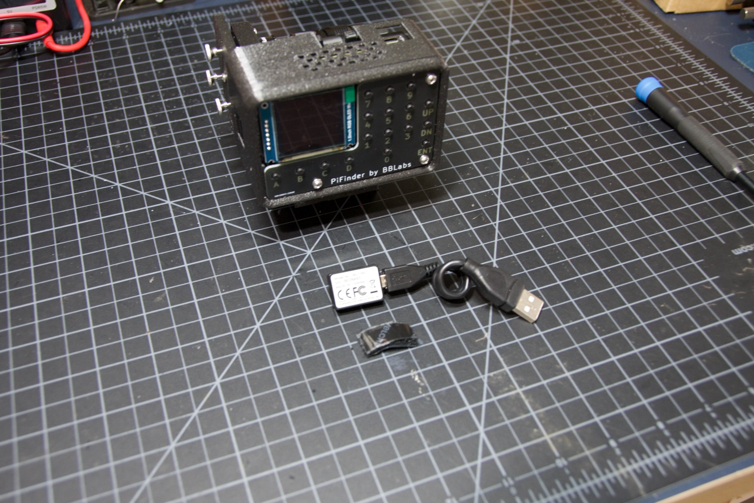
images/build_guide/v1.6/build_guide_42.jpeg
