testezt/EZTFinder5/images/build_guide/v1.6/flat/flat_build_guide_18.jpeg

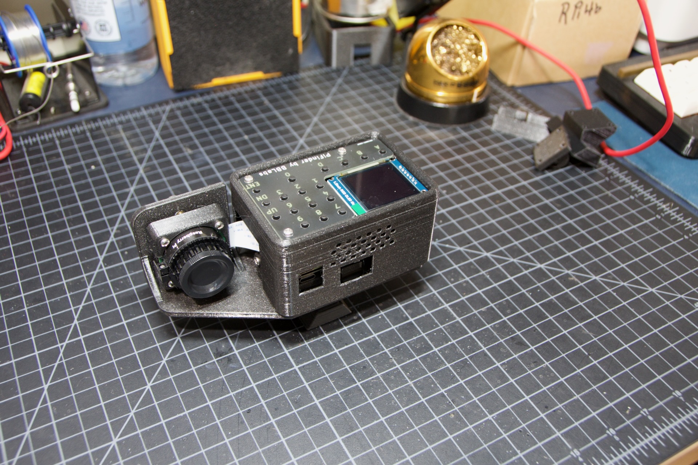
images/build_guide/v1.6/flat/flat_build_guide_18.jpeg
