testezt/EZTFinder5/images/screenshots/how_to_see_CATALOG_004.png

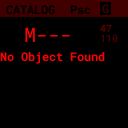
images/screenshots/how_to_see_CATALOG_004.png
