testezt/EZTFinder5/images/screenshots/how_to_see_CHART_001.png

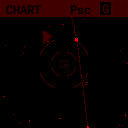
images/screenshots/how_to_see_CHART_001.png
