testezt/EZTFinder5/images/screenshots/how_to_see_LOG_OPTIONS_001.png

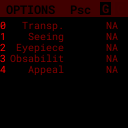
images/screenshots/how_to_see_LOG_OPTIONS_001.png
