testezt/EZTFinder5/images/screenshots/how_to_see_OPTIONS_006.png

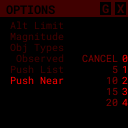
images/screenshots/how_to_see_OPTIONS_006.png
