testezt/EZTFinder5/images/user_guide/camera_controls.png

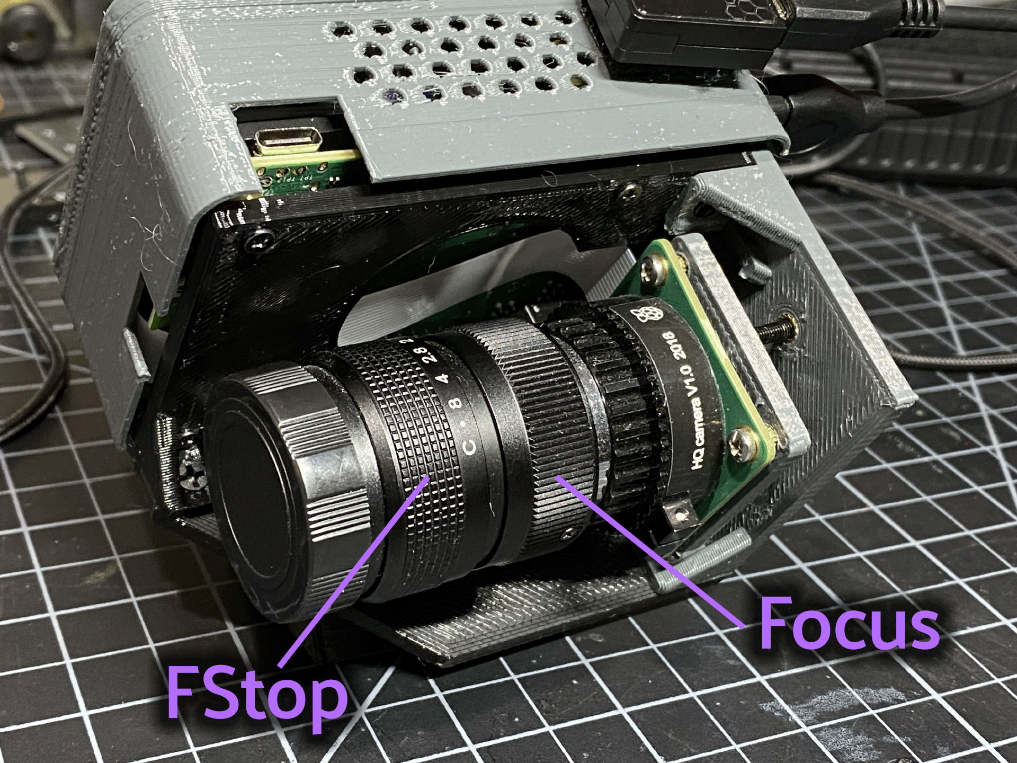
images/user_guide/camera_controls.png
