testezt/EZTFinder5/docs/source/images/user_guide/name_search_results.png

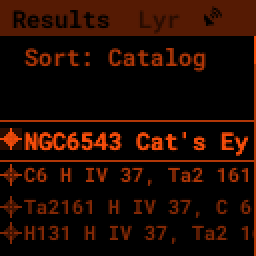
docs/source/images/user_guide/name_search_results.png
