testezt/EZTFinder5/python/PiFinder/splash.py

#!/usr/bin/python
# -*- coding:utf-8 -*-
"""
This module is the main entry point for PiFinder it:
* Initializes the display
* Spawns keyboard process
* Sets up time/location via GPS
* Spawns camers/solver process
* then runs the UI loop

"""

import os
from PIL import Image, ImageDraw
from PiFinder import displays
import numpy as np


def do_nothing():
    pass


def show_splash():
    display = displays.get_display("ssd1351")
    display.device.cleanup = do_nothing
    display.set_brightness(125)

    # load welcome image to screen
    root_dir = os.path.realpath(os.path.join(os.path.dirname(__file__), "..", ".."))
    welcome_image_path = os.path.join(root_dir, "images", "welcome.png")
    welcome_image = Image.open(welcome_image_path)
    welcome_image = Image.fromarray(np.array(welcome_image)[:, :, ::-1])
    screen_draw = ImageDraw.Draw(welcome_image)

    # Display version and Wifi mode
    with open(os.path.join(root_dir, "version.txt"), "r") as ver_f:
        version = "v" + ver_f.read()

    with open(os.path.join(root_dir, "wifi_status.txt"), "r") as wifi_f:
        wifi_mode = wifi_f.read()
    screen_draw.rectangle([0, 0, 128, 16], fill=(0, 0, 0))
    screen_draw.text(
        (0, 1),
        f"Wifi:{wifi_mode: <6}  {version: >8}",
        font=display.fonts.base.font,
        fill=(255, 0, 0),
    )

    display.device.display(welcome_image.convert(display.device.mode))


if __name__ == "__main__":
    show_splash()
