testezt/EZTFinder5/python/PiFinder/integrator.py

#!/usr/bin/python
# -*- coding:utf-8 -*-
"""
This module is the solver
* Checks IMU
* Plate solves high-res image

"""

import queue
import time
import copy
import logging

from PiFinder import config
from PiFinder import state_utils
import PiFinder.calc_utils as calc_utils
from PiFinder.multiproclogging import MultiprocLogging

IMU_ALT = 2
IMU_AZ = 0

logger = logging.getLogger("IMU.Integrator")


def imu_moved(imu_a, imu_b):
    """
    Compares two IMU states to determine if they are the 'same'
    if either is none, returns False
    """
    if imu_a is None:
        return False
    if imu_b is None:
        return False

    # figure out the abs difference
    diff = (
        abs(imu_a[0] - imu_b[0]) + abs(imu_a[1] - imu_b[1]) + abs(imu_a[2] - imu_b[2])
    )
    if diff > 0.001:
        return True
    return False


def integrator(shared_state, solver_queue, console_queue, log_queue, is_debug=False):
    MultiprocLogging.configurer(log_queue)
    try:
        if is_debug:
            logger.setLevel(logging.DEBUG)
        logger.debug("Starting Integrator")

        solved = {
            "RA": None,
            "Dec": None,
            "Roll": None,
            "camera_center": {
                "RA": None,
                "Dec": None,
                "Roll": None,
                "Alt": None,
                "Az": None,
            },
            "camera_solve": {
                "RA": None,
                "Dec": None,
                "Roll": None,
            },
            "Roll_offset": 0,  # May/may not be needed - for experimentation
            "imu_pos": None,
            "Alt": None,
            "Az": None,
            "solve_source": None,
            "solve_time": None,
            "cam_solve_time": 0,
            "constellation": None,
        }
        cfg = config.Config()
        if (
            cfg.get_option("screen_direction") == "left"
            or cfg.get_option("screen_direction") == "flat"
            or cfg.get_option("screen_direction") == "flat3"
            or cfg.get_option("screen_direction") == "straight"
        ):
            flip_alt_offset = True
        else:
            flip_alt_offset = False

        # This holds the last image solve position info
        # so we can delta for IMU updates
        last_image_solve = None
        last_solve_time = time.time()
        while True:
            state_utils.sleep_for_framerate(shared_state)

            # Check for new camera solve in queue
            next_image_solve = None
            try:
                next_image_solve = solver_queue.get(block=False)
            except queue.Empty:
                pass

            if type(next_image_solve) is dict:
                solved = next_image_solve

                # see if we can generate alt/az
                location = shared_state.location()
                dt = shared_state.datetime()

                # see if we can calc alt-az
                solved["Alt"] = None
                solved["Az"] = None
                if location and dt:
                    # We have position and time/date!
                    calc_utils.sf_utils.set_location(
                        location.lat,
                        location.lon,
                        location.altitude,
                    )
                    alt, az = calc_utils.sf_utils.radec_to_altaz(
                        solved["RA"],
                        solved["Dec"],
                        dt,
                    )
                    solved["Alt"] = alt
                    solved["Az"] = az

                    alt, az = calc_utils.sf_utils.radec_to_altaz(
                        solved["camera_center"]["RA"],
                        solved["camera_center"]["Dec"],
                        dt,
                    )
                    solved["camera_center"]["Alt"] = alt
                    solved["camera_center"]["Az"] = az

                    # Experimental: For monitoring roll offset
                    # Estimate the roll offset due misalignment of the
                    # camera sensor with the Pole-to-Source great circle.
                    solved["Roll_offset"] = estimate_roll_offset(solved, dt)
                    # Find the roll at the target RA/Dec. Note that this doesn't include the
                    # roll offset so it's not the roll that the PiFinder camear sees but the
                    # roll relative to the celestial pole
                    roll_target_calculated = calc_utils.sf_utils.radec_to_roll(
                        solved["RA"], solved["Dec"], dt
                    )
                    # Compensate for the roll offset. This gives the roll at the target
                    # as seen by the camera.
                    solved["Roll"] = roll_target_calculated + solved["Roll_offset"]

                    # calculate roll for camera center
                    roll_target_calculated = calc_utils.sf_utils.radec_to_roll(
                        solved["camera_center"]["RA"],
                        solved["camera_center"]["Dec"],
                        dt,
                    )
                    # Compensate for the roll offset. This gives the roll at the target
                    # as seen by the camera.
                    solved["camera_center"]["Roll"] = (
                        roll_target_calculated + solved["Roll_offset"]
                    )

                last_image_solve = copy.deepcopy(solved)
                solved["solve_source"] = "CAM"

            # Use IMU dead-reckoning from the last camera solve:
            # Check we have an alt/az solve, otherwise we can't use the IMU
            elif solved["Alt"]:
                imu = shared_state.imu()
                if imu:
                    dt = shared_state.datetime()
                    if last_image_solve and last_image_solve["Alt"]:
                        # If we have alt, then we have a position/time

                        # calc new alt/az
                        lis_imu = last_image_solve["imu_pos"]
                        imu_pos = imu["pos"]
                        if imu_moved(lis_imu, imu_pos):
                            alt_offset = imu_pos[IMU_ALT] - lis_imu[IMU_ALT]
                            if flip_alt_offset:
                                alt_offset = ((alt_offset + 180) % 360 - 180) * -1
                            else:
                                alt_offset = (alt_offset + 180) % 360 - 180
                            solved["Alt"] = (last_image_solve["Alt"] - alt_offset) % 360
                            solved["camera_center"]["Alt"] = (
                                last_image_solve["camera_center"]["Alt"] - alt_offset
                            ) % 360

                            az_offset = imu_pos[IMU_AZ] - lis_imu[IMU_AZ]
                            az_offset = (az_offset + 180) % 360 - 180
                            solved["Az"] = (last_image_solve["Az"] + az_offset) % 360
                            solved["camera_center"]["Az"] = (
                                last_image_solve["camera_center"]["Az"] + az_offset
                            ) % 360

                            # N.B. Assumes that location hasn't changed since last solve
                            # Turn this into RA/DEC
                            (
                                solved["RA"],
                                solved["Dec"],
                            ) = calc_utils.sf_utils.altaz_to_radec(
                                solved["Alt"], solved["Az"], dt
                            )
                            # Calculate the roll at the target RA/Dec and compensate for the offset.
                            solved["Roll"] = (
                                calc_utils.sf_utils.radec_to_roll(
                                    solved["RA"], solved["Dec"], dt
                                )
                                + solved["Roll_offset"]
                            )

                            # Now for camera centered solve
                            (
                                solved["camera_center"]["RA"],
                                solved["camera_center"]["Dec"],
                            ) = calc_utils.sf_utils.altaz_to_radec(
                                solved["camera_center"]["Alt"],
                                solved["camera_center"]["Az"],
                                dt,
                            )
                            # Calculate the roll at the target RA/Dec and compensate for the offset.
                            solved["camera_center"]["Roll"] = (
                                calc_utils.sf_utils.radec_to_roll(
                                    solved["camera_center"]["RA"],
                                    solved["camera_center"]["Dec"],
                                    dt,
                                )
                                + solved["Roll_offset"]
                            )

                            solved["solve_time"] = time.time()
                            solved["solve_source"] = "IMU"

            # Is the solution new?
            if solved["RA"] and solved["solve_time"] > last_solve_time:
                last_solve_time = time.time()
                # Update remaining solved keys
                solved["constellation"] = calc_utils.sf_utils.radec_to_constellation(
                    solved["RA"], solved["Dec"]
                )

                # add solution
                shared_state.set_solution(solved)
                shared_state.set_solve_state(True)
    except EOFError:
        logger.error("Main no longer running for integrator")


def estimate_roll_offset(solved, dt):
    """
    Estimate the roll offset due to misalignment of the camera sensor with
    the mount/scope's coordinate system. The offset is calculated at the
    center of the camera's FoV.

    To calculate the roll with offset: roll = calculated_roll + roll_offset
    """
    # Calculate the expected roll at the camera center given the RA/Dec of
    # of the camera center.
    roll_camera_calculated = calc_utils.sf_utils.radec_to_roll(
        solved["camera_center"]["RA"], solved["camera_center"]["Dec"], dt
    )
    roll_offset = solved["camera_center"]["Roll"] - roll_camera_calculated

    return roll_offset
