testezt/EZTFinder5/python/PiFinder/obslist.py

#!/usr/bin/python
# -*- coding:utf-8 -*-
"""
This module has functions
for reading / writing
observing lists in skylist
format used by SkySafari
but supported by other
tools
"""

import os
import logging
from textwrap import dedent
from PiFinder import utils
from PiFinder.catalogs import Catalogs

logger = logging.getLogger("Observation.List")

OBSLIST_DIR = f"{utils.data_dir}/obslists/"

SKYSAFARI_CATALOG_NAMES = {
    "CAL": "C",
    "COL": "Cr",
}

SKYSAFARI_CATALOG_NAMES_INV = {v: k for k, v in SKYSAFARI_CATALOG_NAMES.items()}


def write_list(catalog_objects, name):
    """
    Writes the list of catalog objects
    to a file.
    """
    index_num = 0
    with open(OBSLIST_DIR + name + ".skylist", "w") as skylist:
        skylist.write("SkySafariObservingListVersion=3.0\n")
        for obj in catalog_objects:
            catalog_name = SKYSAFARI_CATALOG_NAMES.get(
                obj.catalog_code, obj.catalog_code
            )
            catalog_number = f"{catalog_name} {obj.sequence}"
            entry_text = dedent(
                f"""
                SkyObject=BeginObject
                    ObjectID=4,-1,-1
                    CatalogNumber={catalog_number}
                    DefaultIndex={index_num}
                EndObject=SkyObject
                """
            ).strip()
            skylist.write(entry_text + "\n")
            index_num += 1


def resolve_object(catalog_numbers, catalogs: Catalogs):
    """
    Takes a list of SkySafari catalog
    numbers and tries to find an object
    in our DB which matches
    """
    for catalog_number in catalog_numbers:
        catalog = catalog_number.split(" ")[0]
        catalog = SKYSAFARI_CATALOG_NAMES_INV.get(catalog, catalog)
        try:
            sequence = catalog_number.split(" ")[1].strip()
            sequence = int(sequence)
        except (ValueError, IndexError):
            sequence = None

        if sequence is not None:
            _object = catalogs.get_object(catalog, sequence)
            if _object:
                return _object
    return None


def read_list(catalogs: Catalogs, name):
    """
    Reads a skylist style observing
    list.  Matches against catalogs
    and returns a catalog list
    """

    list_catalog: list = []
    catalog_numbers: list = []
    objects_parsed = 0
    in_object = False
    with open(OBSLIST_DIR + name + ".skylist", "r") as skylist:
        for line in skylist:
            line = line.strip()
            if line == "SkyObject=BeginObject":
                if in_object:
                    logger.critical(
                        "Encountered object start while in object.  File is corrupt"
                    )
                    return {
                        "result": "error",
                        "objects_parsed": objects_parsed,
                        "message": "Bad start tag",
                        "catalog_objects": list_catalog,
                    }

                catalog_numbers = []
                in_object = True

            elif line == "EndObject=SkyObject":
                if not in_object:
                    logger.critical(
                        "Encountered object end while not in object.  File is corrupt"
                    )
                    return {
                        "result": "error",
                        "objects_parsed": objects_parsed,
                        "message": "Bad end tag",
                        "catalog_objects": list_catalog,
                    }

                # see if we can resolve an object
                _object = resolve_object(catalog_numbers, catalogs)

                if _object:
                    list_catalog.append(_object)

                objects_parsed += 1
                in_object = False

            elif line.startswith("CatalogNumber"):
                if not in_object:
                    logger.critical(
                        "Encountered catalog number while not in object.  File is corrupt"
                    )
                    return {
                        "result": "error",
                        "objects_parsed": objects_parsed,
                        "message": "Bad catalog tag",
                        "catalog_objects": list_catalog,
                    }
                catalog_numbers.append(line.split("=")[1])

            else:
                pass

    return {
        "result": "success",
        "objects_parsed": objects_parsed,
        "message": "Complete",
        "catalog_objects": list_catalog,
    }


def get_lists():
    """
    Returns a list of list names on disk
    """
    obs_files = []
    for filename in os.listdir(OBSLIST_DIR):
        if not filename.startswith(".") and filename.endswith(".skylist"):
            obs_files.append(filename[:-8])

    return obs_files
