testezt/EZTFinder5/python/PiFinder/keyboard_none.py

import time
from PiFinder.keyboard_interface import KeyboardInterface
import logging

from PiFinder.multiproclogging import MultiprocLogging

logger = logging.getLogger("Keyboard.None")


class KeyboardNone(KeyboardInterface):
    def __init__(self, q):
        try:
            self.q = q
        except Exception as e:
            logger.error("KeyboardLocal.__init__: {}".format(e))
        # manager.logger = True
        logger.debug("KeyboardLocal.__init__")

    def callback(self, key):
        self.q.put(key)


def run_keyboard(q, shared_state, log_queue):
    MultiprocLogging.configurer(log_queue)
    KeyboardNone(q)

    while True:
        # We just need to not terminate here
        time.sleep(1)
