testezt/EZTFinder5/python/PiFinder/manager_patch.py

# mypy: ignore-errors
# Backport of https://github.com/python/cpython/pull/4819
# Improvements to the Manager / proxied shared values code
# broke handling of proxied objects without a custom proxy type,
# as the AutoProxy function was not updated.
#
# This code adds a wrapper to AutoProxy if it is missing the
# new argument.

import logging
from inspect import signature
from functools import wraps
from multiprocessing import managers


logger = logging.getLogger(__name__)
orig_AutoProxy = managers.AutoProxy


@wraps(managers.AutoProxy)
def AutoProxy(*args, incref=True, manager_owned=False, **kwargs):
    # Create the autoproxy without the manager_owned flag, then
    # update the flag on the generated instance. If the manager_owned flag
    # is set, `incref` is disabled, so set it to False here for the same
    # result.
    autoproxy_incref = False if manager_owned else incref
    proxy = orig_AutoProxy(*args, incref=autoproxy_incref, **kwargs)
    proxy._owned_by_manager = manager_owned
    return proxy


def apply():
    if "manager_owned" in signature(managers.AutoProxy).parameters:
        return

    logger.debug("Patching multiprocessing.managers.AutoProxy to add manager_owned")
    managers.AutoProxy = AutoProxy

    # re-register any types already registered to SyncManager without a custom
    # proxy type, as otherwise these would all be using the old unpatched AutoProxy
    SyncManager = managers.SyncManager
    registry = managers.SyncManager._registry
    for typeid, (callable, exposed, method_to_typeid, proxytype) in registry.items():
        if proxytype is not orig_AutoProxy:
            continue
        create_method = hasattr(managers.SyncManager, typeid)
        SyncManager.register(
            typeid,
            callable=callable,
            exposed=exposed,
            method_to_typeid=method_to_typeid,
            create_method=create_method,
        )
